CodeByMika/technikerarbeit2026-hardwarepruefadapter/Gehause/ISO-Ansicht.pdf

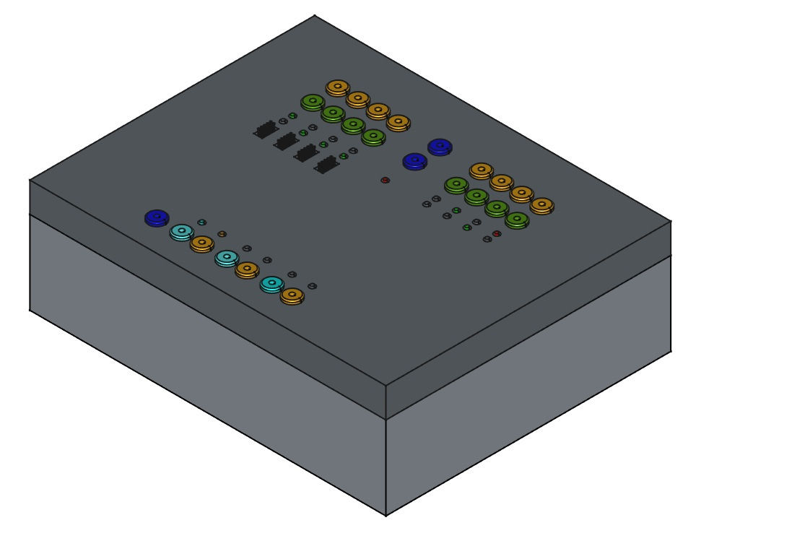
[picture p3: page 1]
