CodeByMika/technikerarbeit2026-hardwarepruefadapter/Hardware/Bauteildesigndaten/DMP3130L-7/DMP3130L-7.step

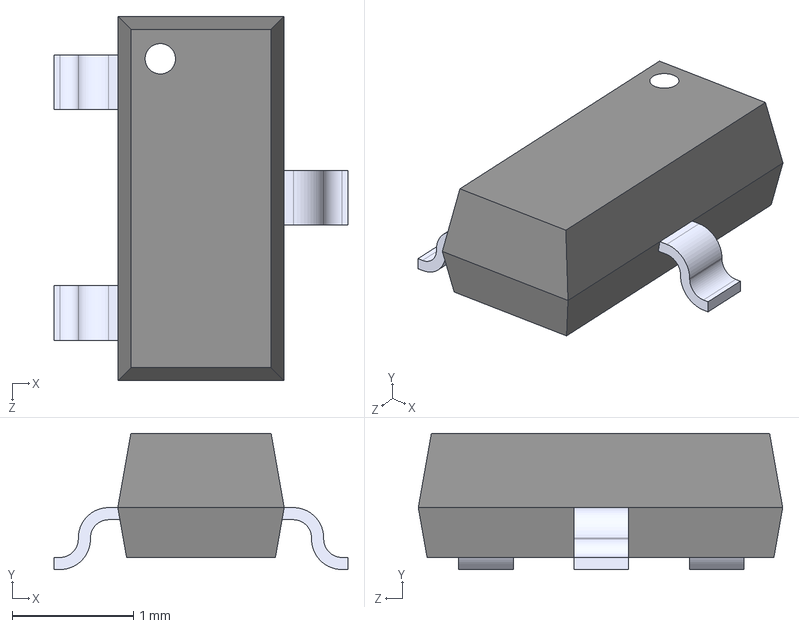
[picture p20: CAD file, 2026-06-18]
Hardware/Bauteildesigndaten/DMP3130L-7/DMP3130L-7.step
2.42 x 1.12 x 3.00 mm
