CodeByMika/technikerarbeit2026-hardwarepruefadapter/Hardware/Bauteildesigndaten/Importierte Bauteile/Buchsen/6120XX21621_61200821621/6120XX21621_61200821621.step

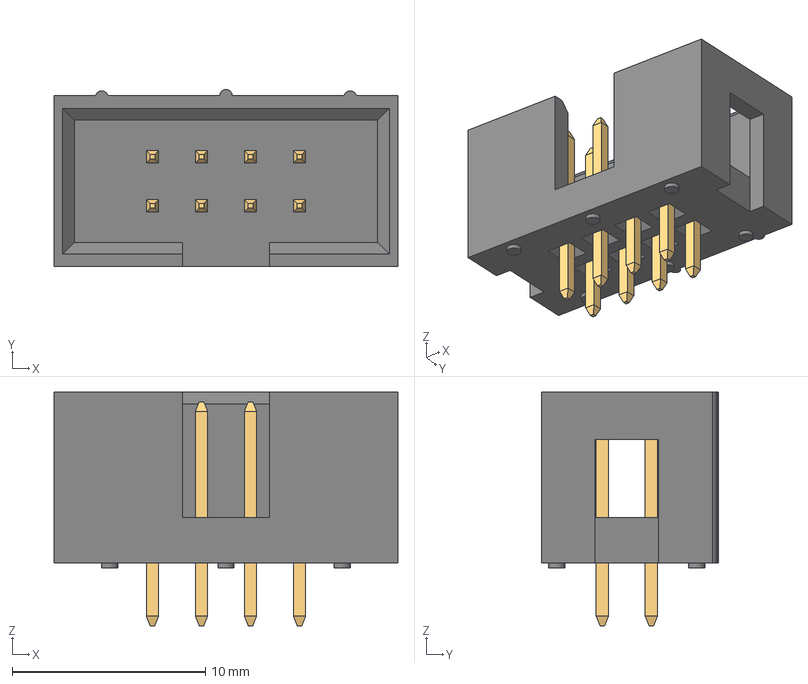
[picture p21: CAD file, 2026-06-18]
Hardware/Bauteildesigndaten/Importierte Bauteile/Buchsen/6120XX21621_61200821621/6120XX21621_61200821621.step
17.8 x 9.18 x 12.1 mm
6120xx21621_PIN x 8
