CodeByMika/technikerarbeit2026-hardwarepruefadapter/Hardware/Bauteildesigndaten/Importierte Bauteile/Buchsen/6120XX21621_61201021621/6120XX21621_61201021621.step

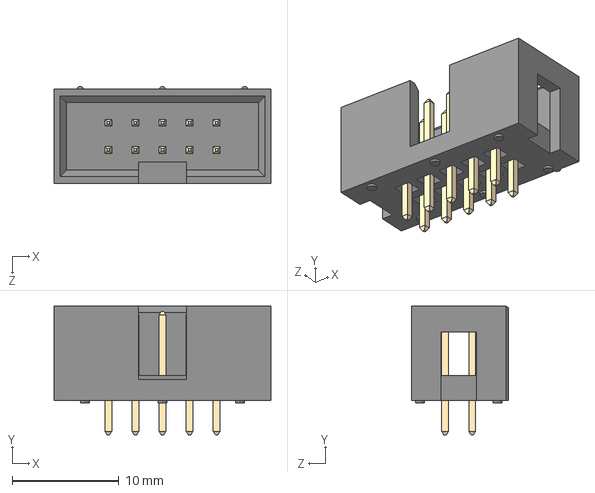
[picture p22: CAD file, 2026-06-18]
Hardware/Bauteildesigndaten/Importierte Bauteile/Buchsen/6120XX21621_61201021621/6120XX21621_61201021621.step
20.4 x 12.1 x 9.10 mm
