CodeByMika/technikerarbeit2026-hardwarepruefadapter/Hardware/Bauteildesigndaten/Importierte Bauteile/Buchsen/6130XX21121_61300621121/6130XX21121_61300621121.step

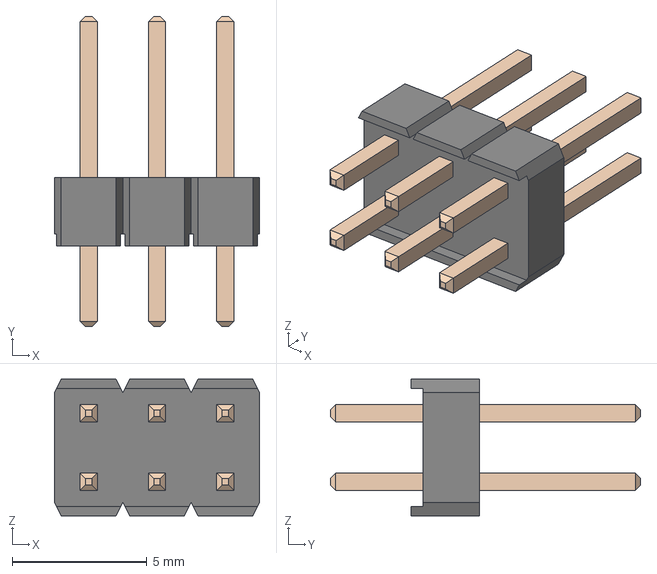
[picture p23: CAD file, 2026-06-18]
Hardware/Bauteildesigndaten/Importierte Bauteile/Buchsen/6130XX21121_61300621121/6130XX21121_61300621121.step
7.62 x 11.5 x 5.08 mm
6130xx21121_PIN x 6
