CodeByMika/technikerarbeit2026-hardwarepruefadapter/Hardware/Bauteildesigndaten/Importierte Bauteile/Buchsen/6130XX21121_61301221121/6130XX21121_61301221121.step

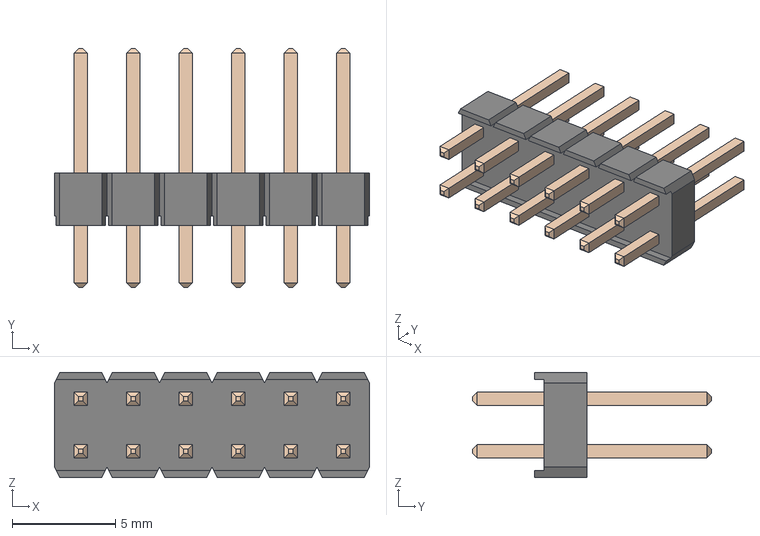
[picture p24: CAD file, 2026-06-18]
Hardware/Bauteildesigndaten/Importierte Bauteile/Buchsen/6130XX21121_61301221121/6130XX21121_61301221121.step
15.2 x 11.5 x 5.08 mm
6130xx21121_PIN x 12
