CodeByMika/technikerarbeit2026-hardwarepruefadapter/Hardware/Bauteildesigndaten/Importierte Bauteile/Buchsen/G800LQ592005HR/G800LQ592005HR.step

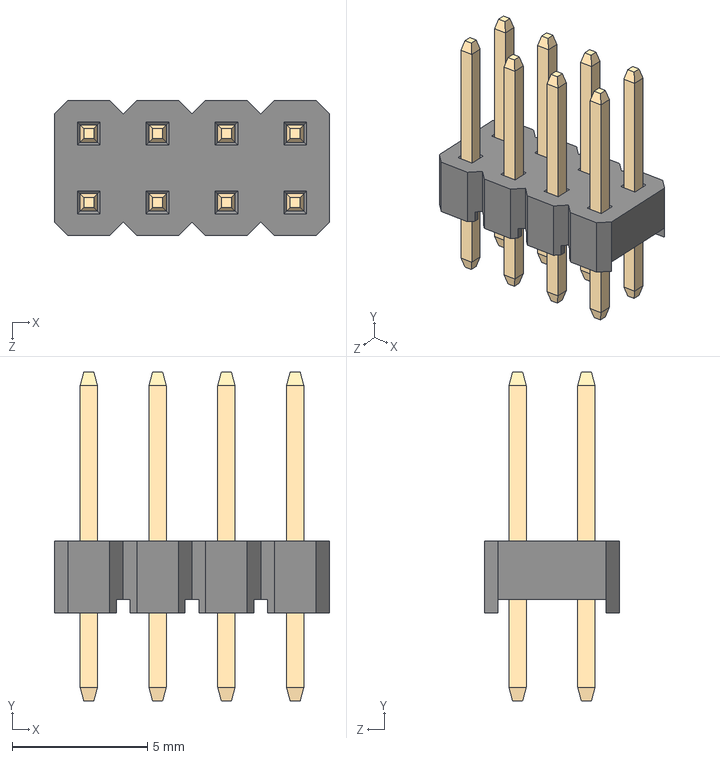
[picture p25: CAD file, 2026-06-18]
Hardware/Bauteildesigndaten/Importierte Bauteile/Buchsen/G800LQ592005HR/G800LQ592005HR.step
10.2 x 12.2 x 5.00 mm
