CodeByMika/technikerarbeit2026-hardwarepruefadapter/Hardware/Bauteildesigndaten/INA168QDBVRQ1/INA168QDBVRQ1.step

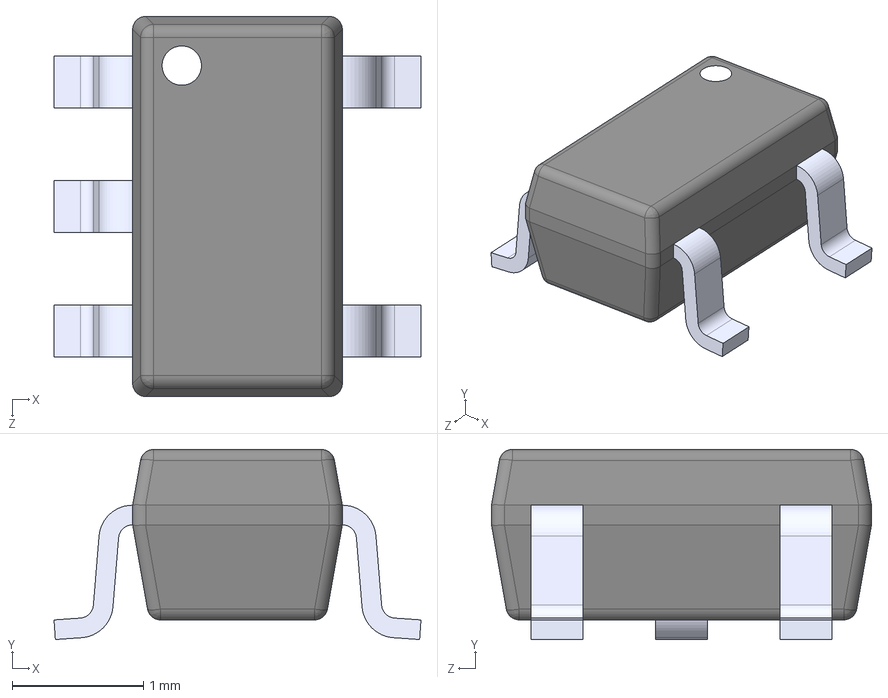
[picture p26: CAD file, 2026-06-18]
Hardware/Bauteildesigndaten/INA168QDBVRQ1/INA168QDBVRQ1.step
2.80 x 1.45 x 2.90 mm
