CodeByMika/technikerarbeit2026-hardwarepruefadapter/Hardware/Bauteildesigndaten/IRF9358PBF/IRF9358PBF.step

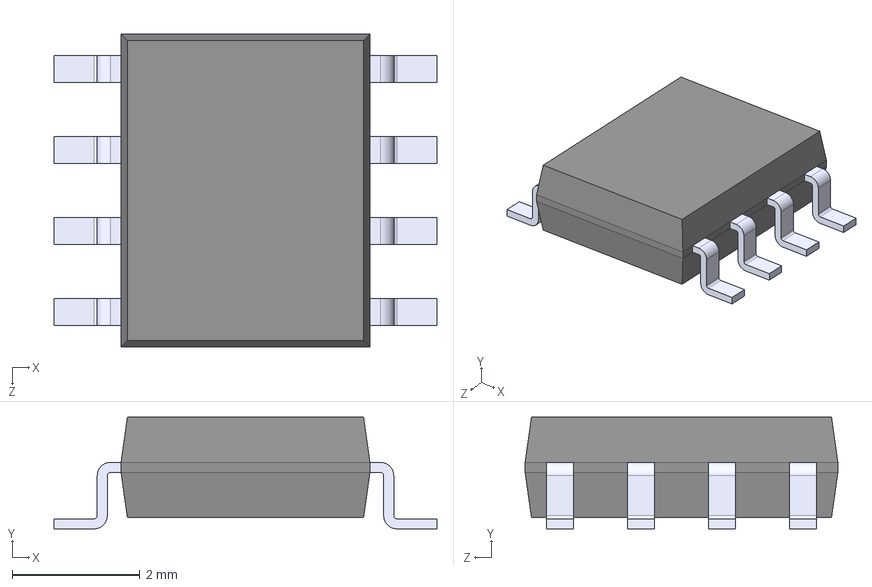
[picture p27: CAD file, 2026-06-18]
Hardware/Bauteildesigndaten/IRF9358PBF/IRF9358PBF.step
6.00 x 1.75 x 4.90 mm
