CodeByMika/technikerarbeit2026-hardwarepruefadapter/Hardware/Bauteildesigndaten/LP5018RSMR/LP5018RSMR.step

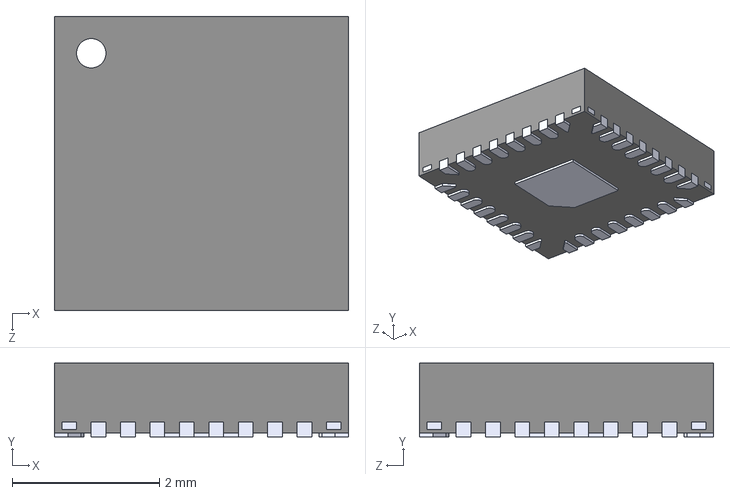
[picture p28: CAD file, 2026-06-18]
Hardware/Bauteildesigndaten/LP5018RSMR/LP5018RSMR.step
4.00 x 1.00 x 4.00 mm
