CodeByMika/technikerarbeit2026-hardwarepruefadapter/Hardware/Bauteildesigndaten/LSF0102DCTR/LSF0102DCTR.step

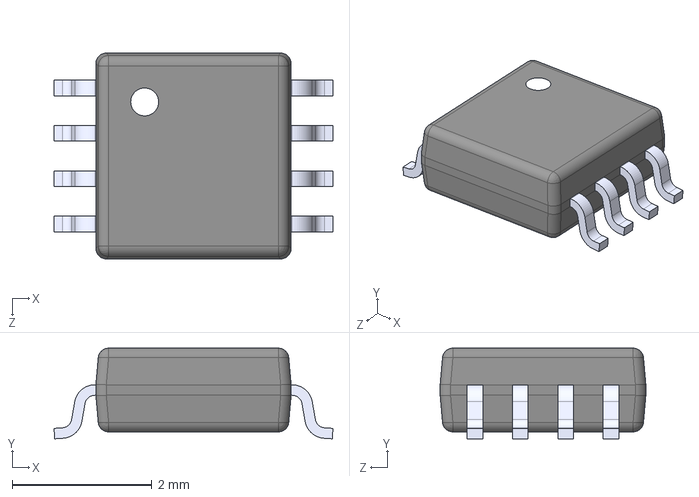
[picture p29: CAD file, 2026-06-18]
Hardware/Bauteildesigndaten/LSF0102DCTR/LSF0102DCTR.step
4.00 x 1.30 x 2.95 mm
