CodeByMika/technikerarbeit2026-hardwarepruefadapter/Hardware/Bauteildesigndaten/MF-MSMF010-2/MF-MSMF010-2.step

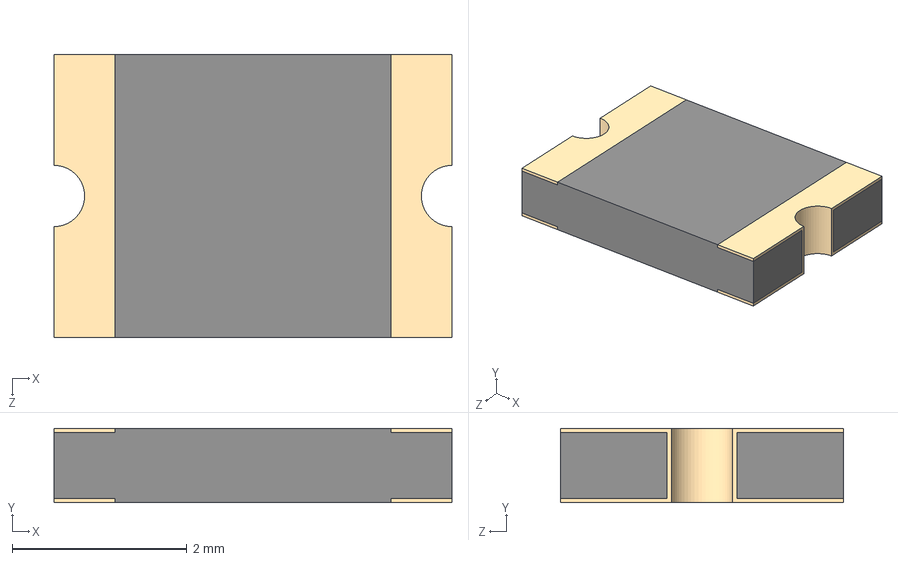
[picture p30: CAD file, 2026-06-18]
Hardware/Bauteildesigndaten/MF-MSMF010-2/MF-MSMF010-2.step
4.55 x 0.85 x 3.24 mm
