CodeByMika/technikerarbeit2026-hardwarepruefadapter/Hardware/Bauteildesigndaten/OPA2990IDR/OPA2990IDR.step

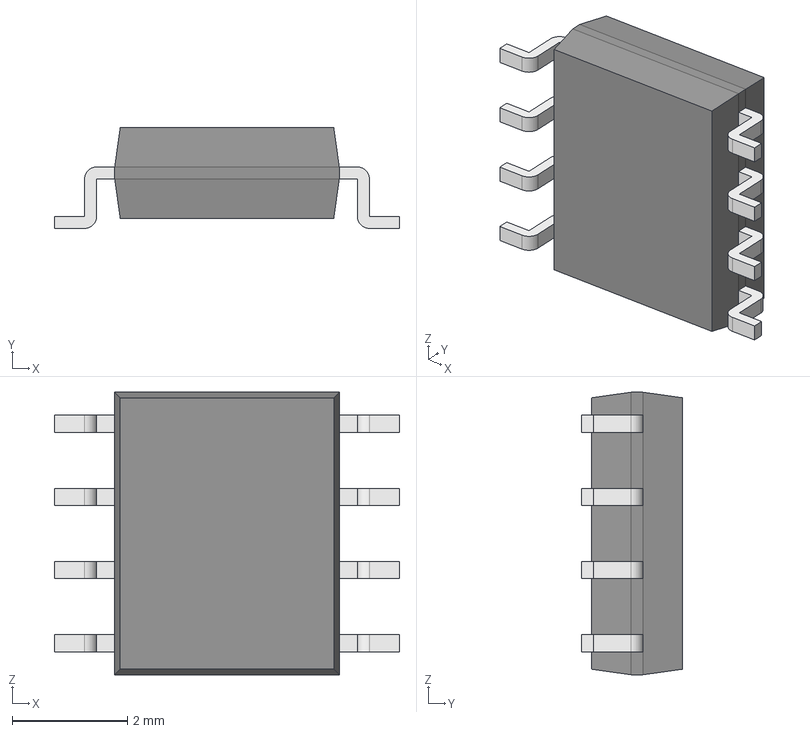
[picture p31: CAD file, 2026-06-18]
Hardware/Bauteildesigndaten/OPA2990IDR/OPA2990IDR.step
5.99 x 1.75 x 4.91 mm
Body001 (Mirror #1) x 4
XY-plane x 12
X-axis x 12
