CodeByMika/technikerarbeit2026-hardwarepruefadapter/Hardware/Bauteildesigndaten/SN65HVD3082ED/SN65HVD3082ED.step

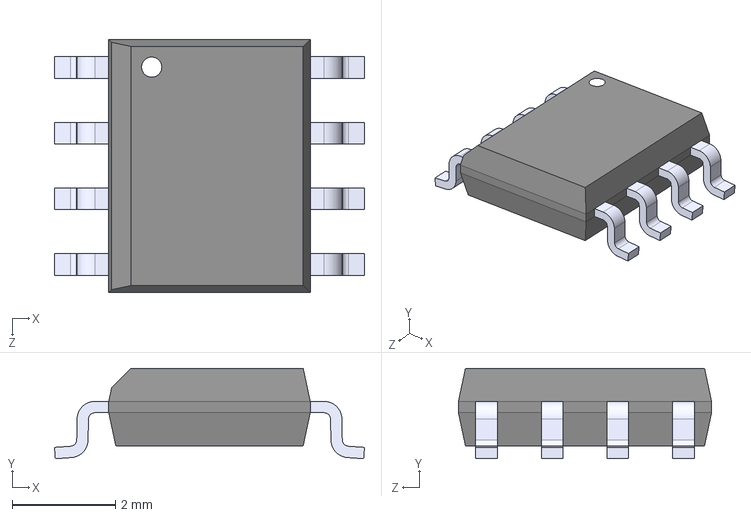
[picture p32: CAD file, 2026-06-18]
Hardware/Bauteildesigndaten/SN65HVD3082ED/SN65HVD3082ED.step
6.00 x 1.75 x 4.90 mm
