CodeByMika/technikerarbeit2026-hardwarepruefadapter/Hardware/Bauteildesigndaten/Spannungsversorgung/LM1117MPX-3.3_NOPB/LM1117MPX-3.3_NOPB.step

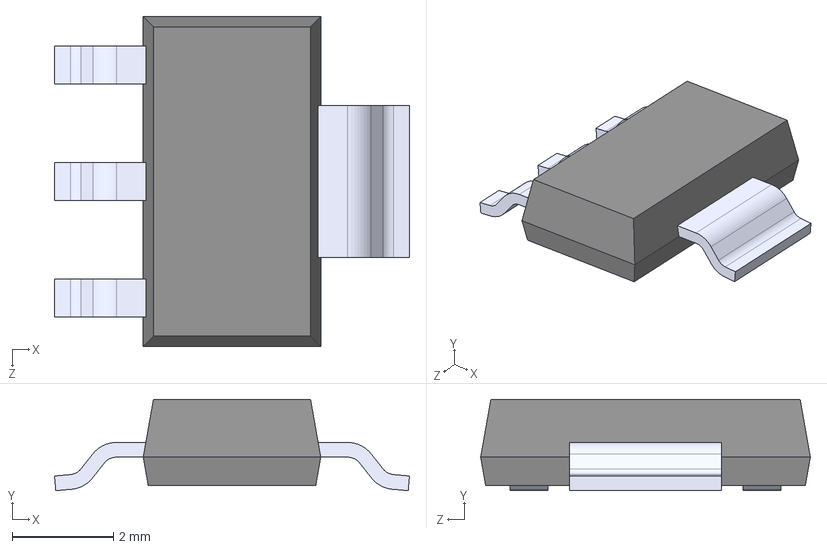
[picture p33: CAD file, 2026-06-18]
Hardware/Bauteildesigndaten/Spannungsversorgung/LM1117MPX-3.3_NOPB/LM1117MPX-3.3_NOPB.step
7.00 x 1.80 x 6.50 mm
