CodeByMika/technikerarbeit2026-hardwarepruefadapter/Hardware/Bauteildesigndaten/Stiftleisten u Buchsen/6120XX21621_61201621621/6120XX21621_61201621621.step

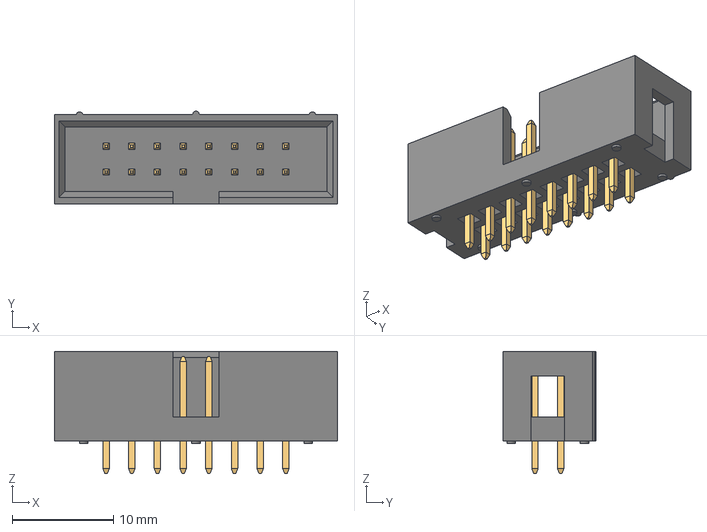
[picture p35: CAD file, 2026-06-18]
Hardware/Bauteildesigndaten/Stiftleisten u Buchsen/6120XX21621_61201621621/6120XX21621_61201621621.step
28.0 x 9.18 x 12.1 mm
6120xx21621_PIN x 16
