CodeByMika/technikerarbeit2026-hardwarepruefadapter/Hardware/Bauteildesigndaten/Stiftleisten u Buchsen/6130XX21121_61301421121/6130XX21121_61301421121.step

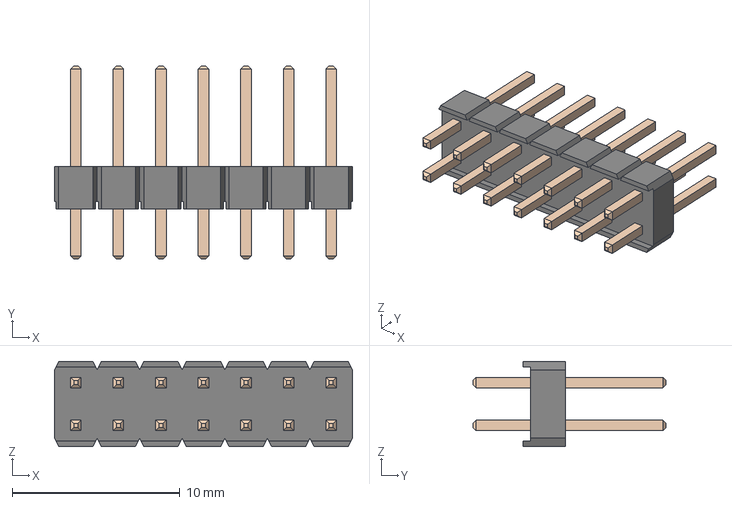
[picture p36: CAD file, 2026-06-18]
Hardware/Bauteildesigndaten/Stiftleisten u Buchsen/6130XX21121_61301421121/6130XX21121_61301421121.step
17.8 x 11.5 x 5.08 mm
6130xx21121_PIN x 14
