CodeByMika/technikerarbeit2026-hardwarepruefadapter/Hardware/Bauteildesigndaten/WE-LQS_3015/WE-LQS_3015.step

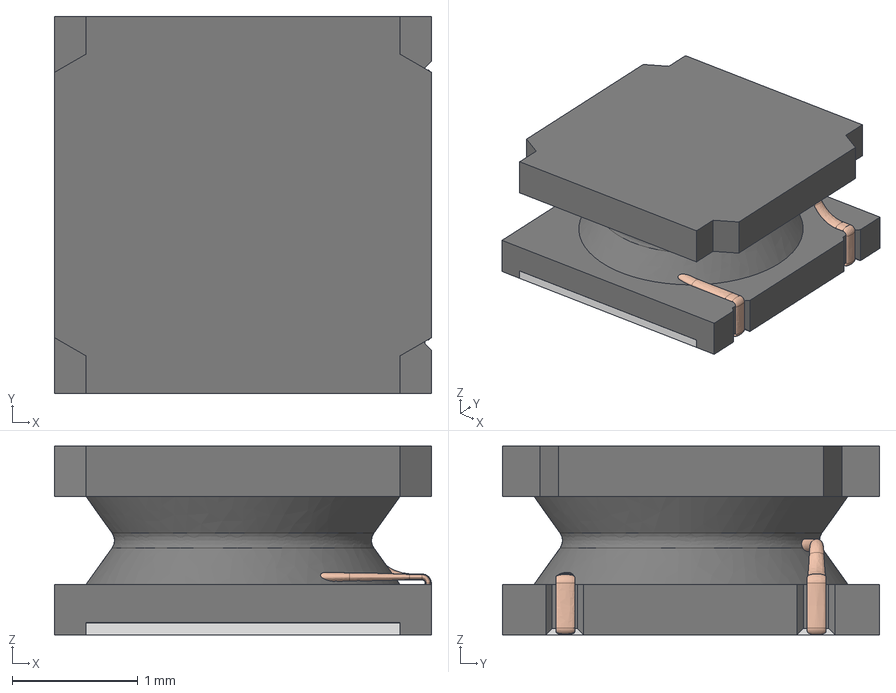
[picture p37: CAD file, 2026-06-18]
Hardware/Bauteildesigndaten/WE-LQS_3015/WE-LQS_3015.step
3.00 x 3.00 x 1.50 mm
