CodeByMika/technikerarbeit2026-hardwarepruefadapter/Hardware/Bauteildesigndaten/WE-MAPI_4020/Download_STP_WE-MAPI_4020+%28rev1%29.stp

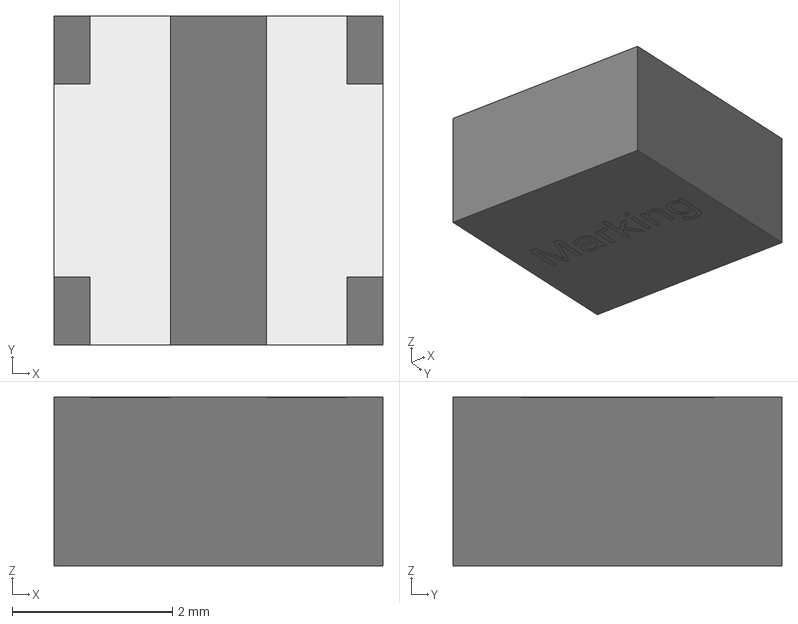
[picture p38: CAD file, 2026-06-18]
Hardware/Bauteildesigndaten/WE-MAPI_4020/Download_STP_WE-MAPI_4020+%28rev1%29.stp
4.10 x 4.10 x 2.10 mm
body_SSMC_4020
land_pattern_SSMC_4020 x 2
