CodeByMika/technikerarbeit2026-hardwarepruefadapter/Hardware/Bauteildesigndaten/WE-MPSB_1812/WE-MPSB_1812.step

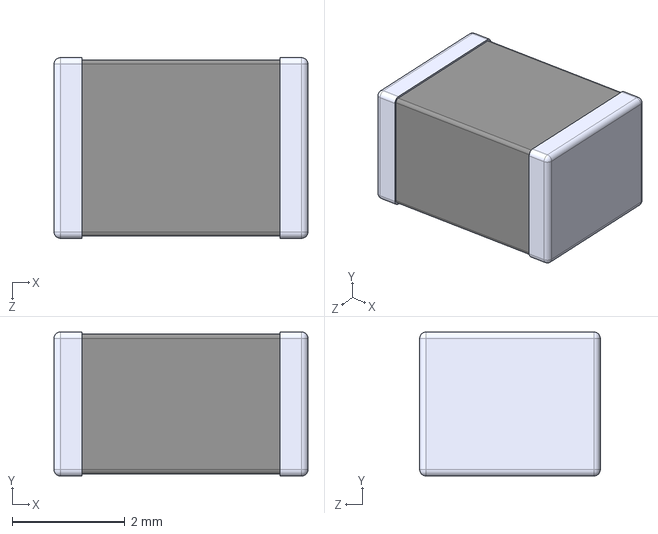
[picture p39: CAD file, 2026-06-18]
Hardware/Bauteildesigndaten/WE-MPSB_1812/WE-MPSB_1812.step
4.50 x 2.55 x 3.20 mm
