CodeByMika/technikerarbeit2026-hardwarepruefadapter/Hardware/Bauteildesigndaten/WL-SMSW_1204_A/WL-SMSW_1204_A.step

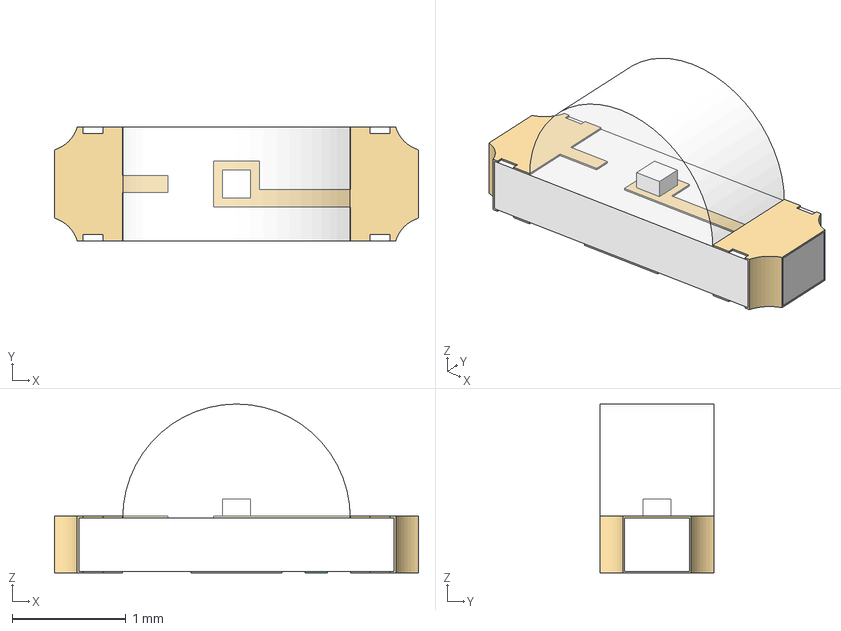
[picture p40: CAD file, 2026-06-18]
Hardware/Bauteildesigndaten/WL-SMSW_1204_A/WL-SMSW_1204_A.step
3.20 x 1.00 x 1.48 mm
glass housing
PCB
contact-pins
