CodeByMika/technikerarbeit2026-hardwarepruefadapter/Hardware/Bauteildesigndaten/XAL7030-332MEB/XAL7030-332MEB.step

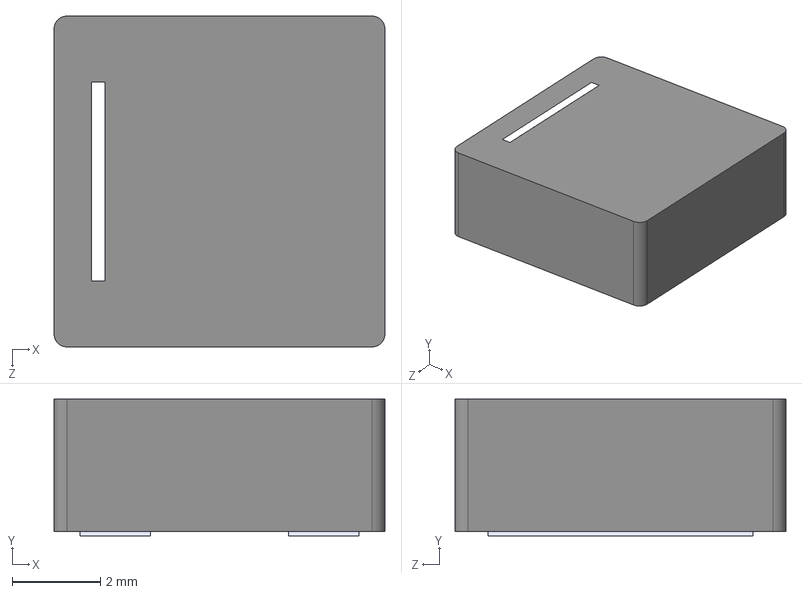
[picture p41: CAD file, 2026-06-18]
Hardware/Bauteildesigndaten/XAL7030-332MEB/XAL7030-332MEB.step
7.50 x 3.10 x 7.50 mm
