CodeByMika/technikerarbeit2026-hardwarepruefadapter/Dokumentation/Technikerarbeit2026-Pflichtenheft.pdf

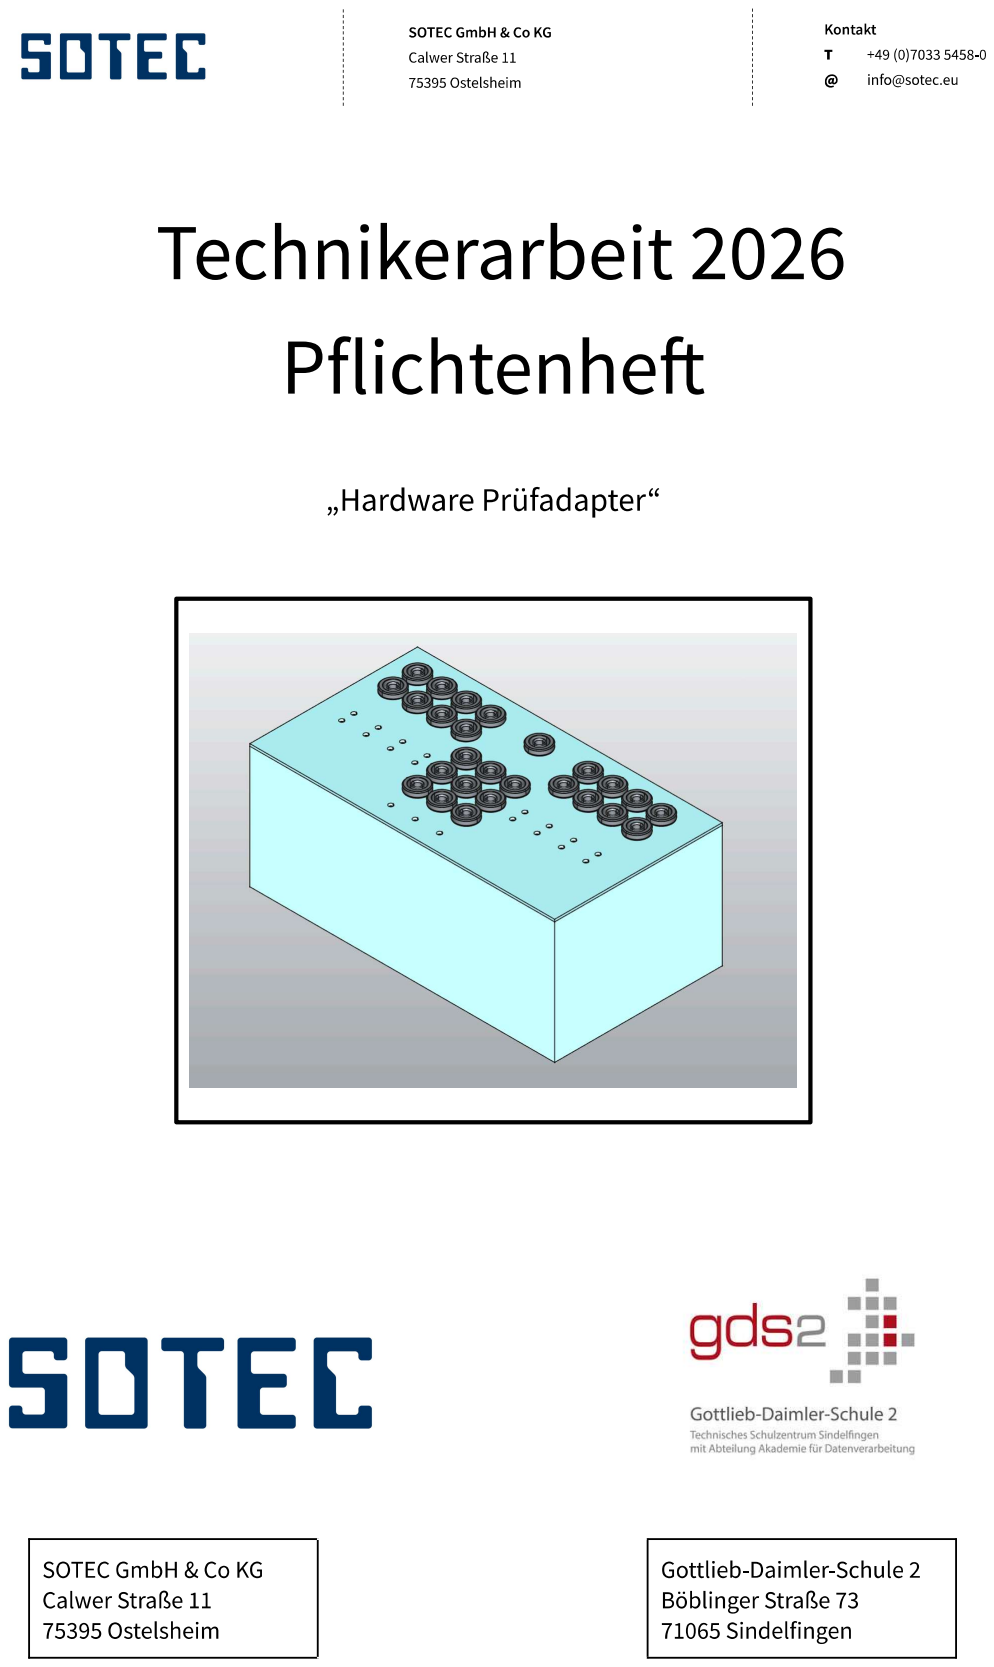
[picture p44: page 1]

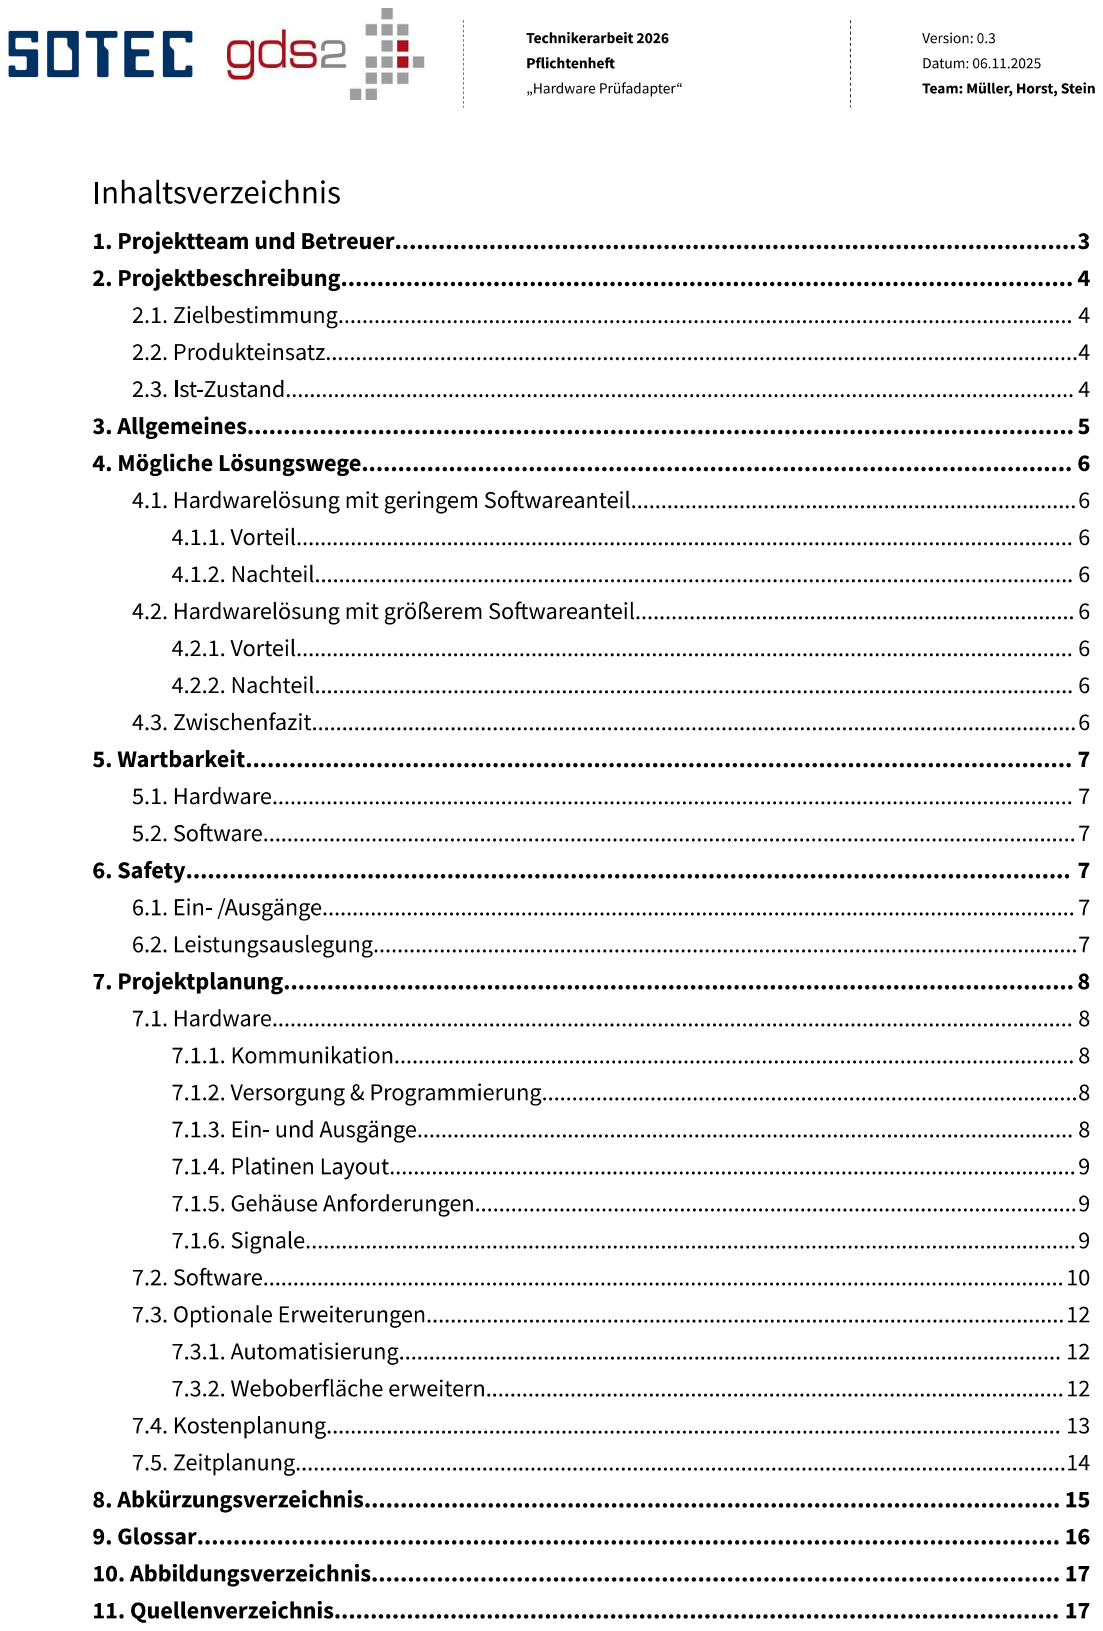
[picture p45: page 2]

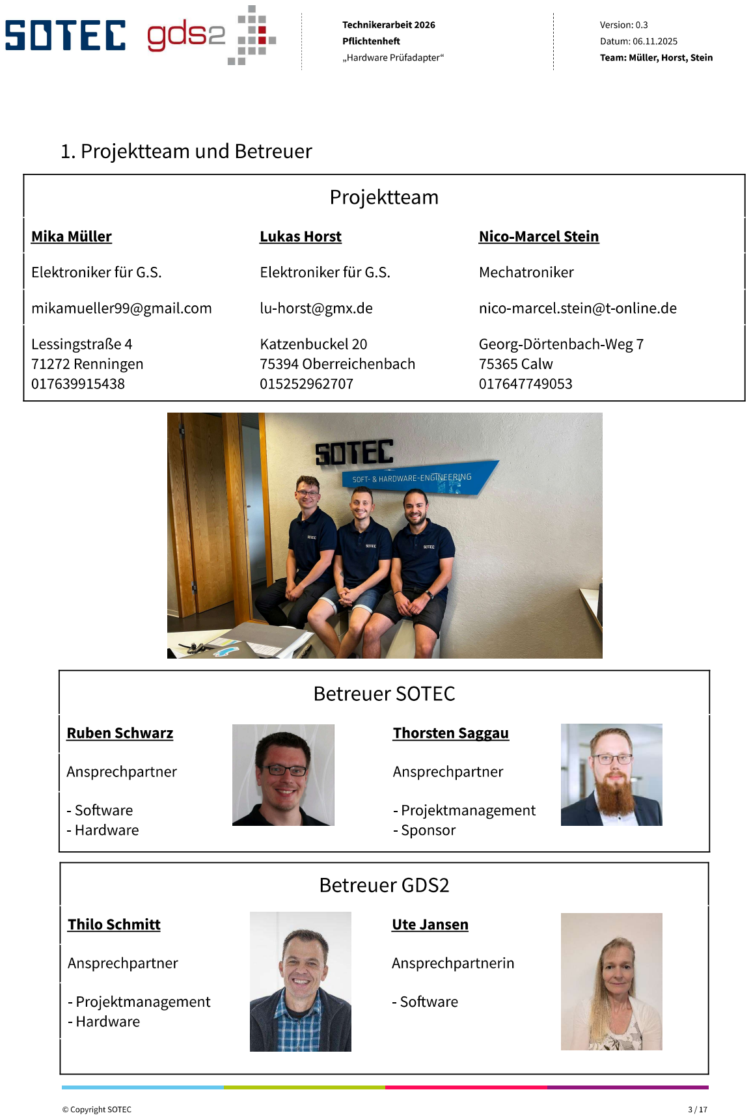
[picture p46: page 3]

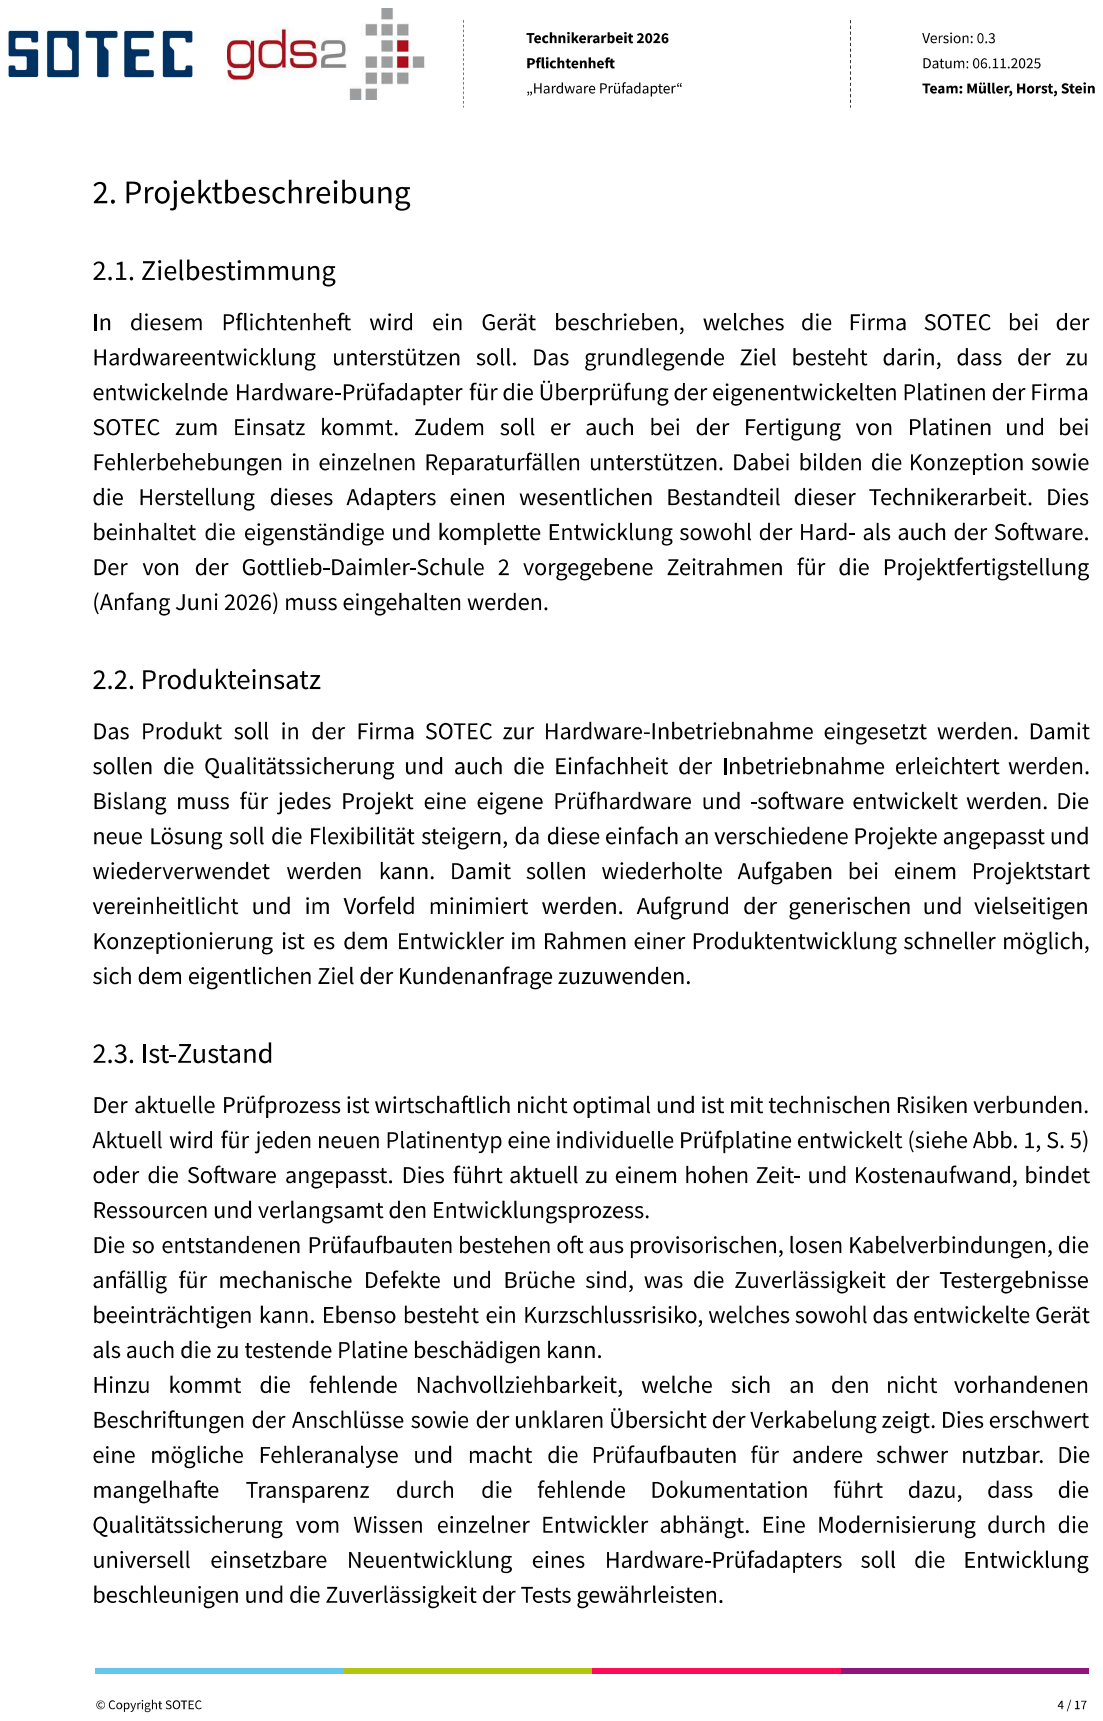
[picture p47: page 4]

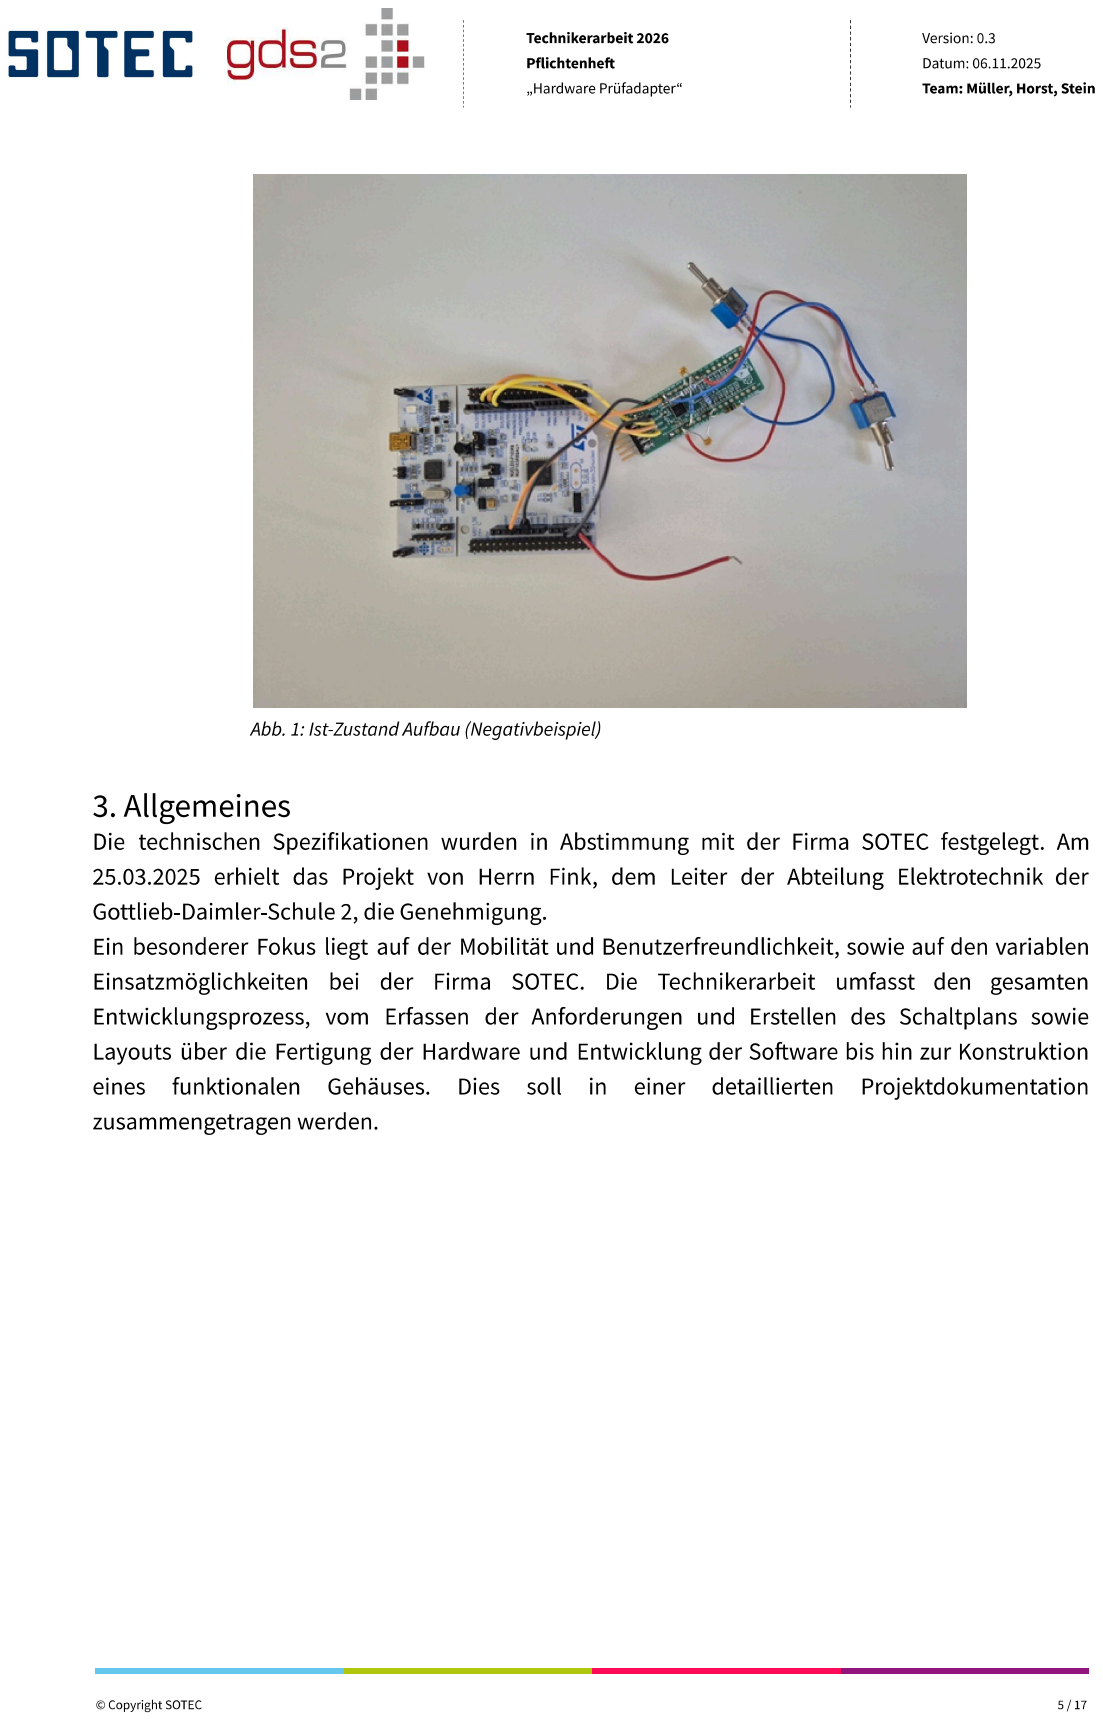
[picture p48: page 5]

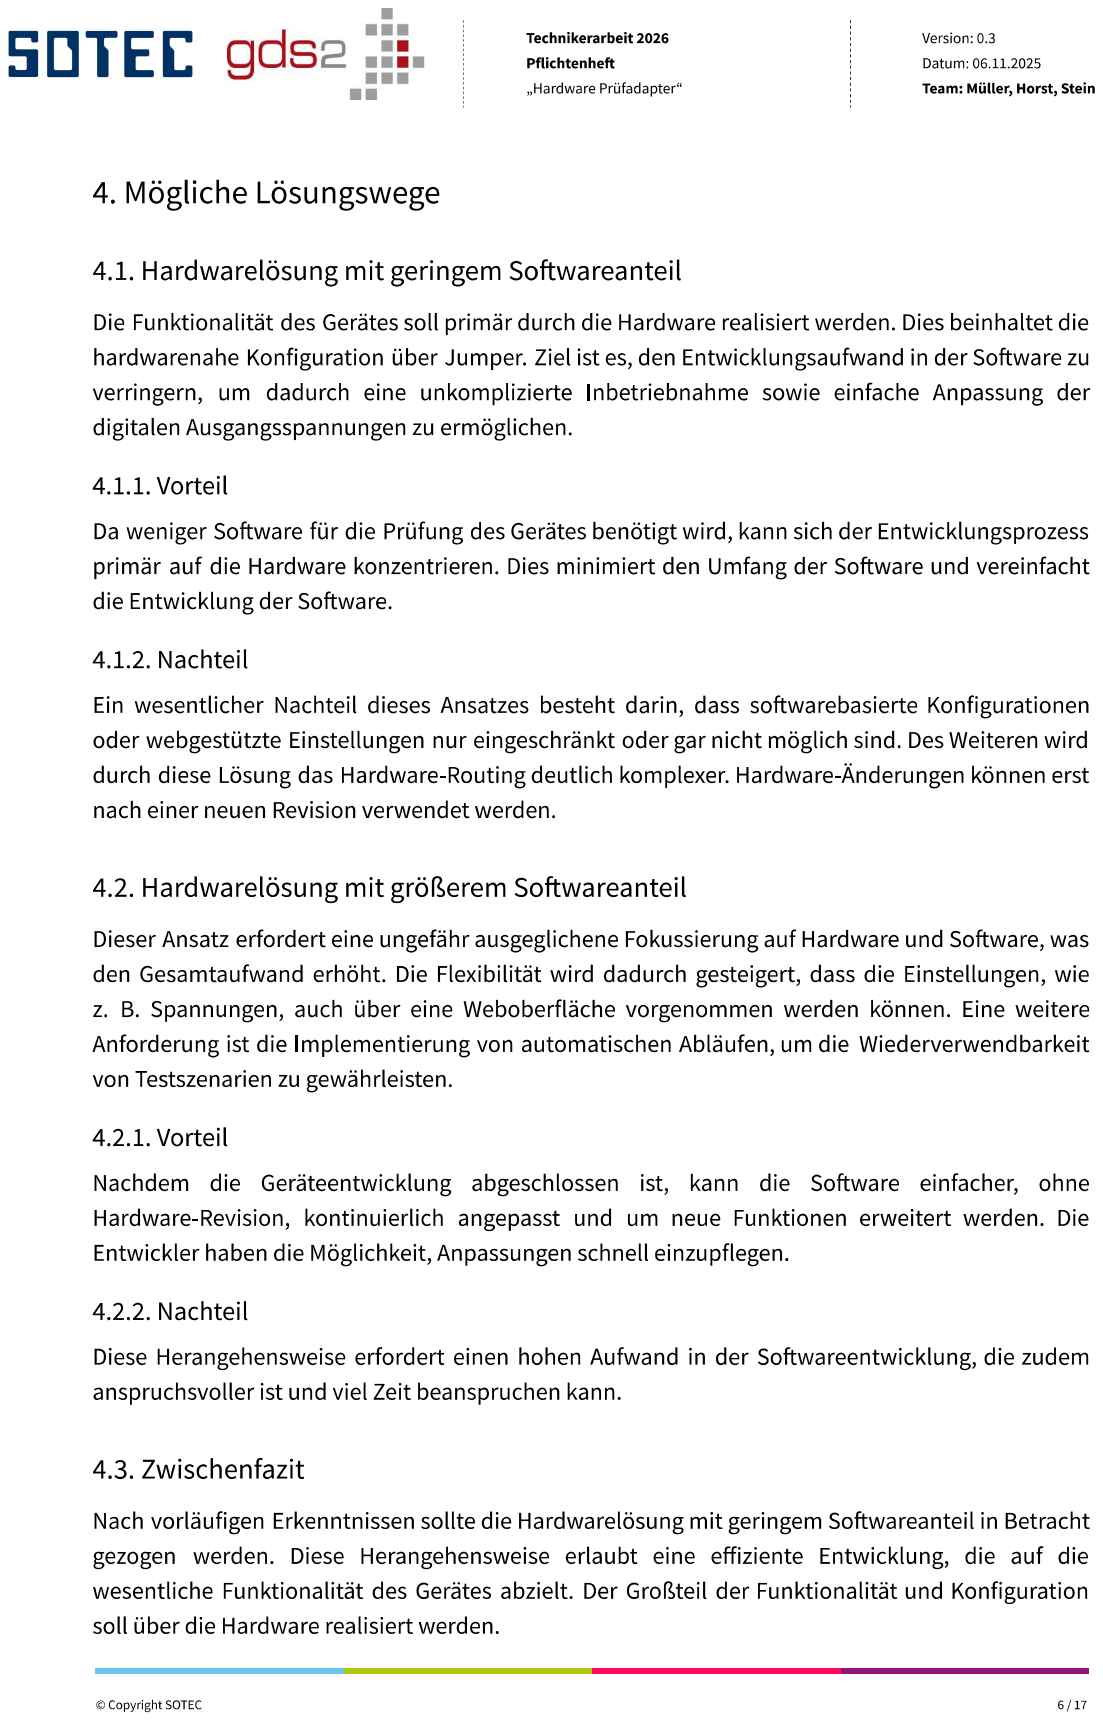
[picture p49: page 6]

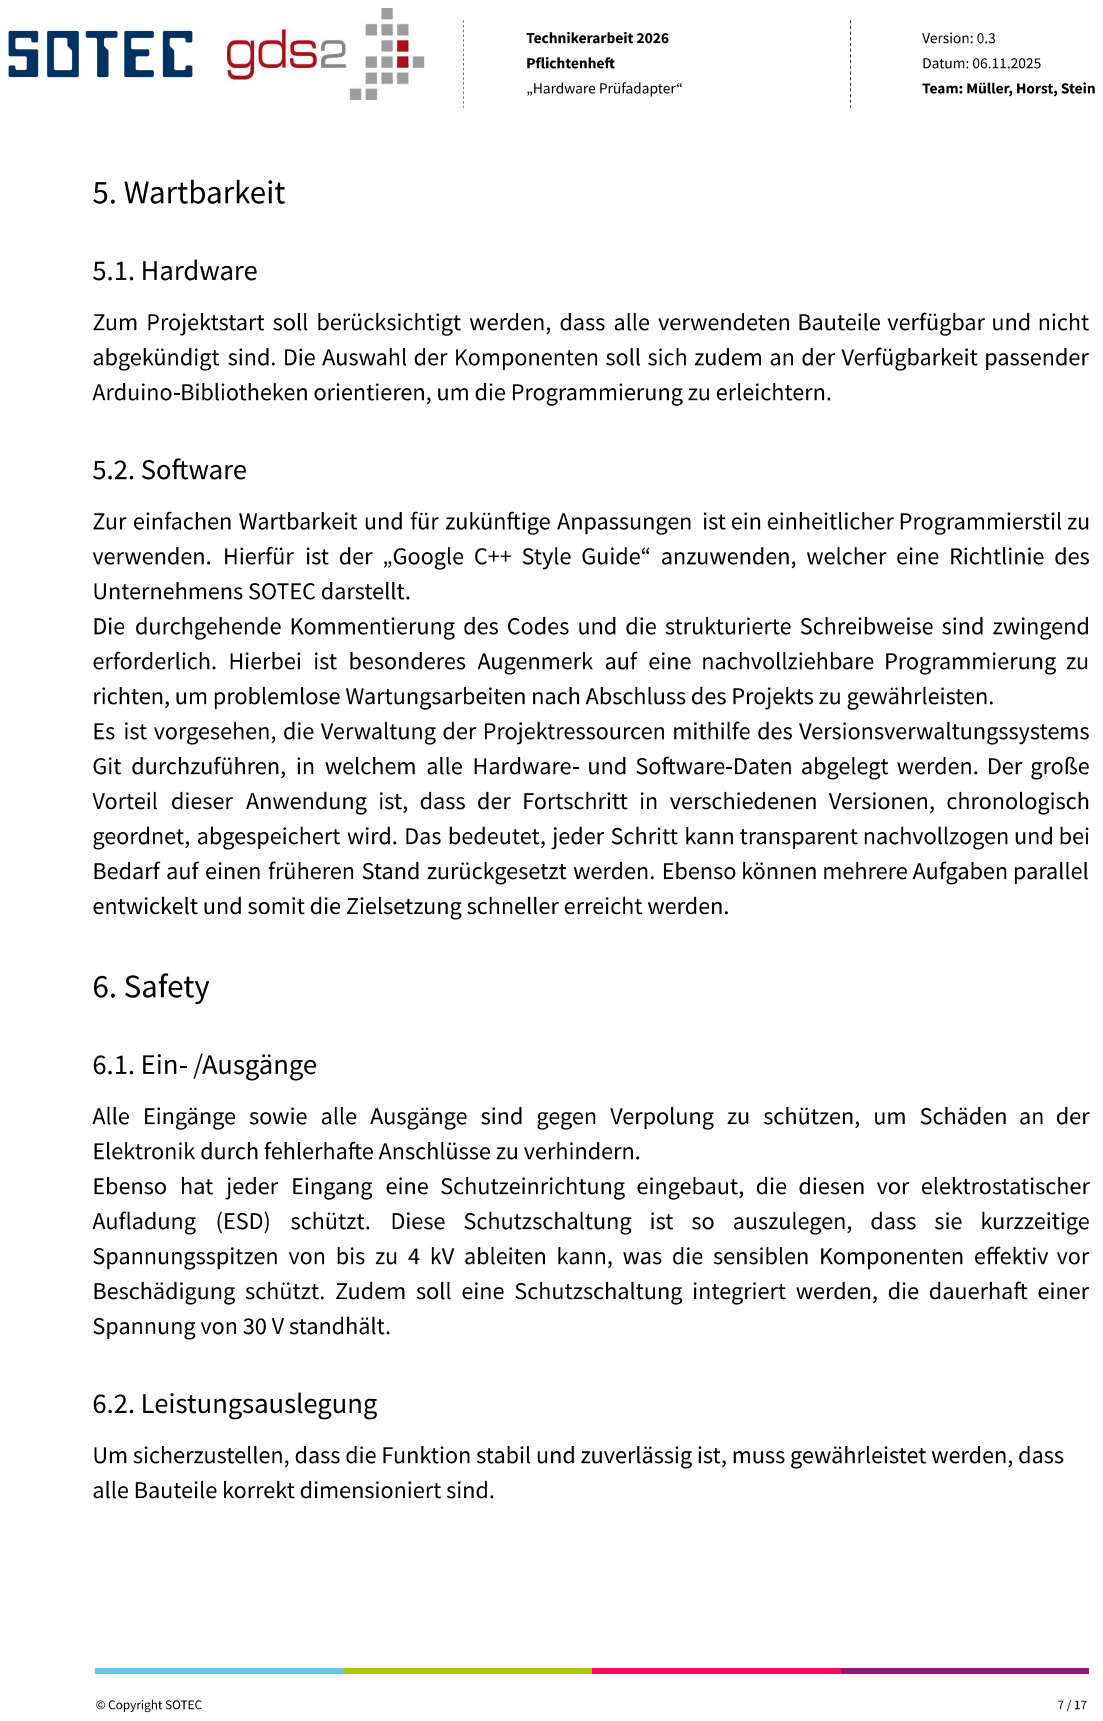
[picture p50: page 7]

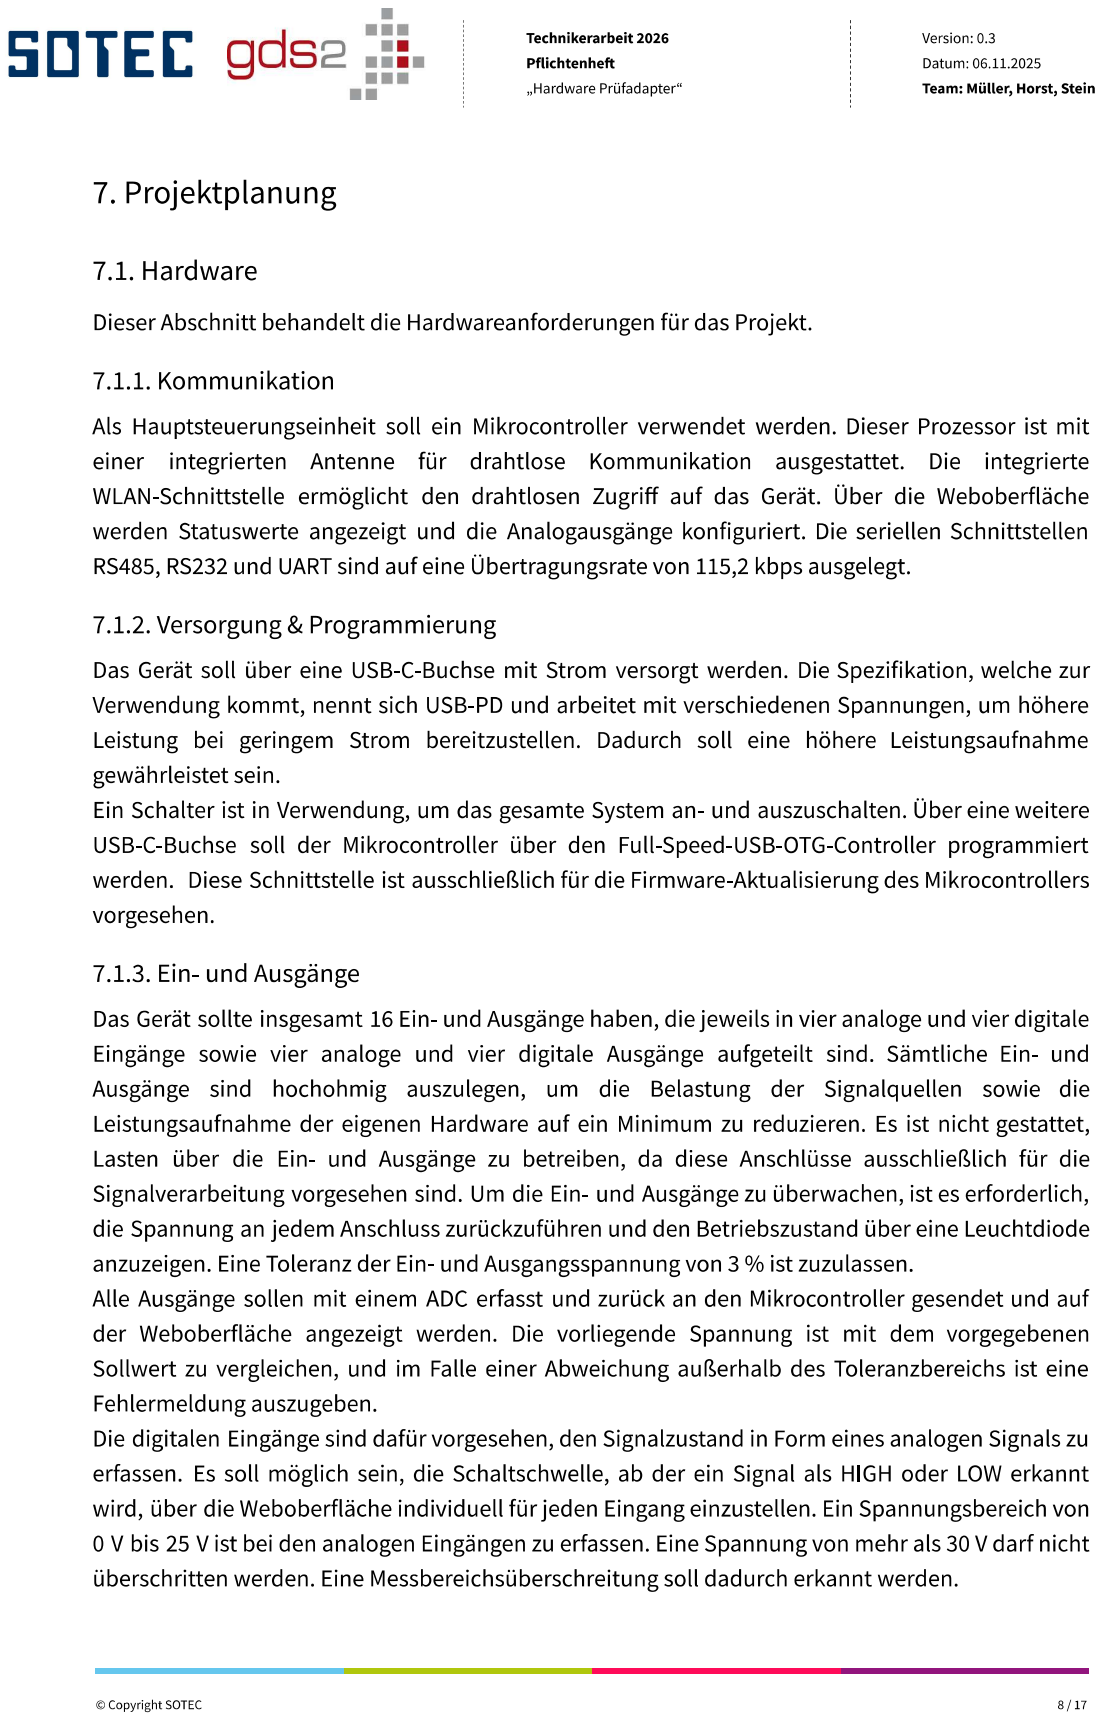
[picture p51: page 8]

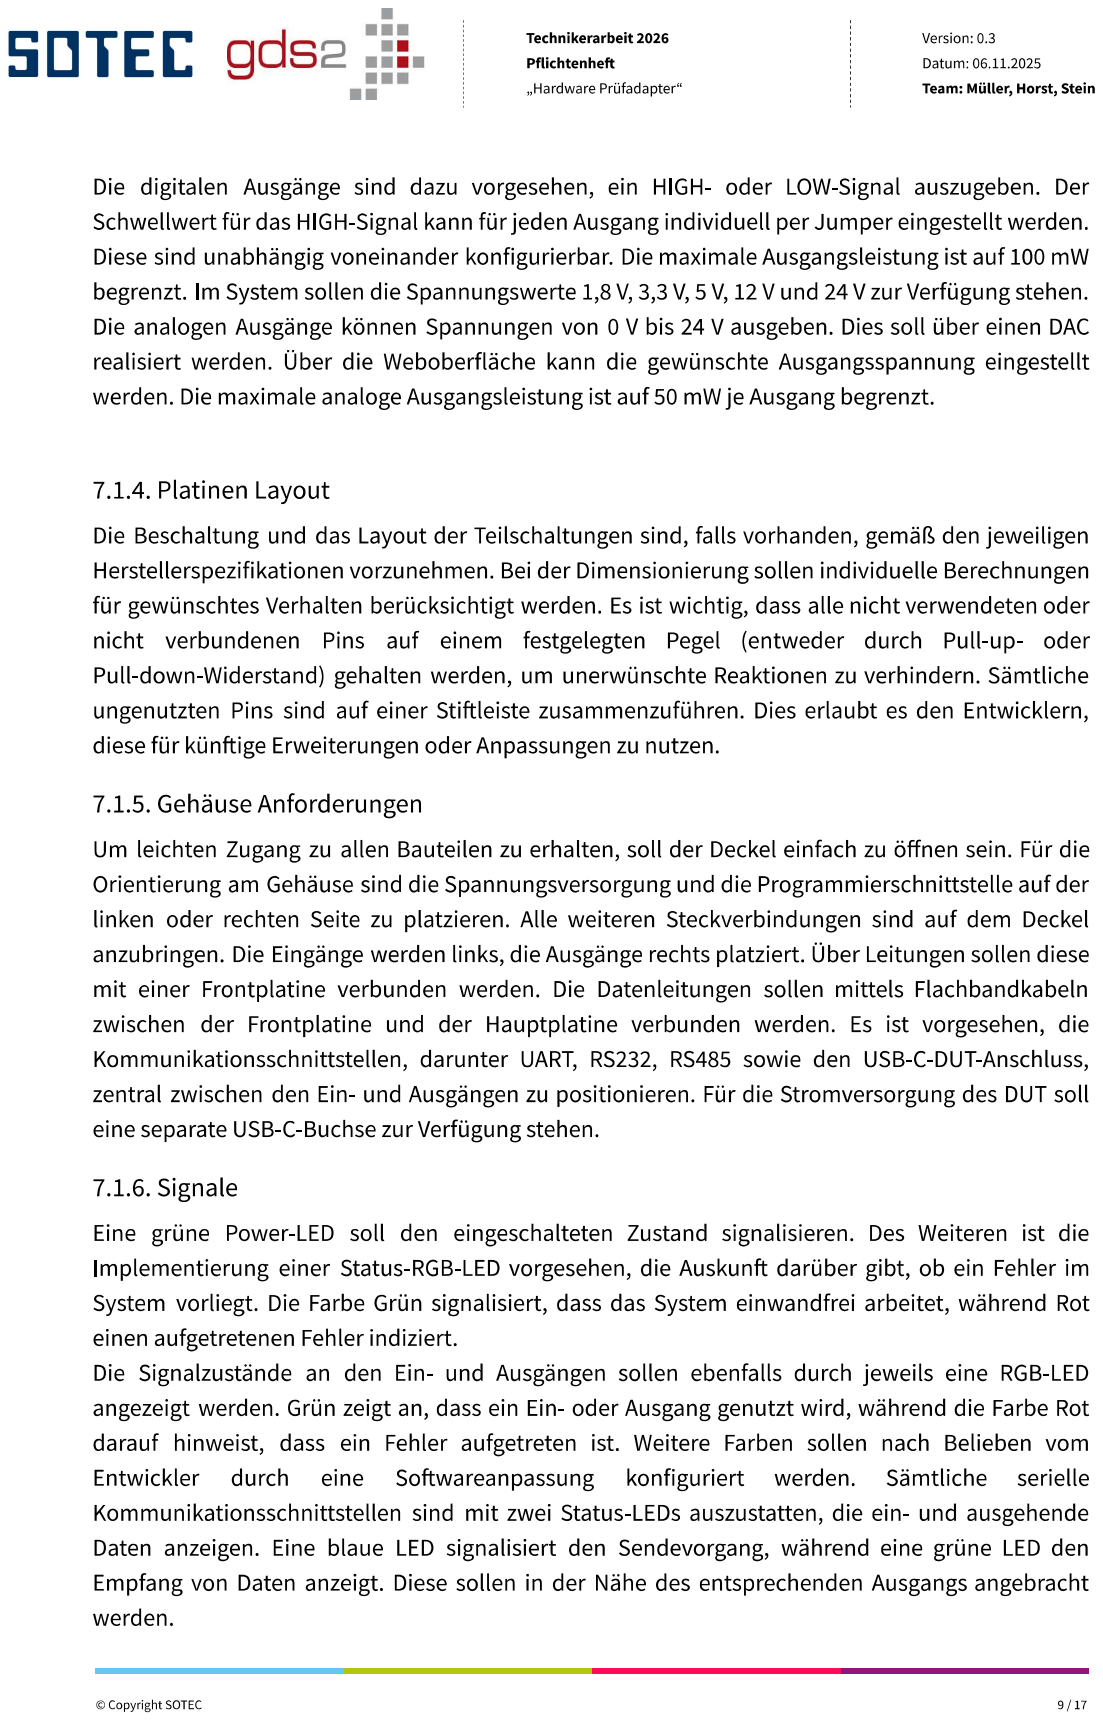
[picture p52: page 9]

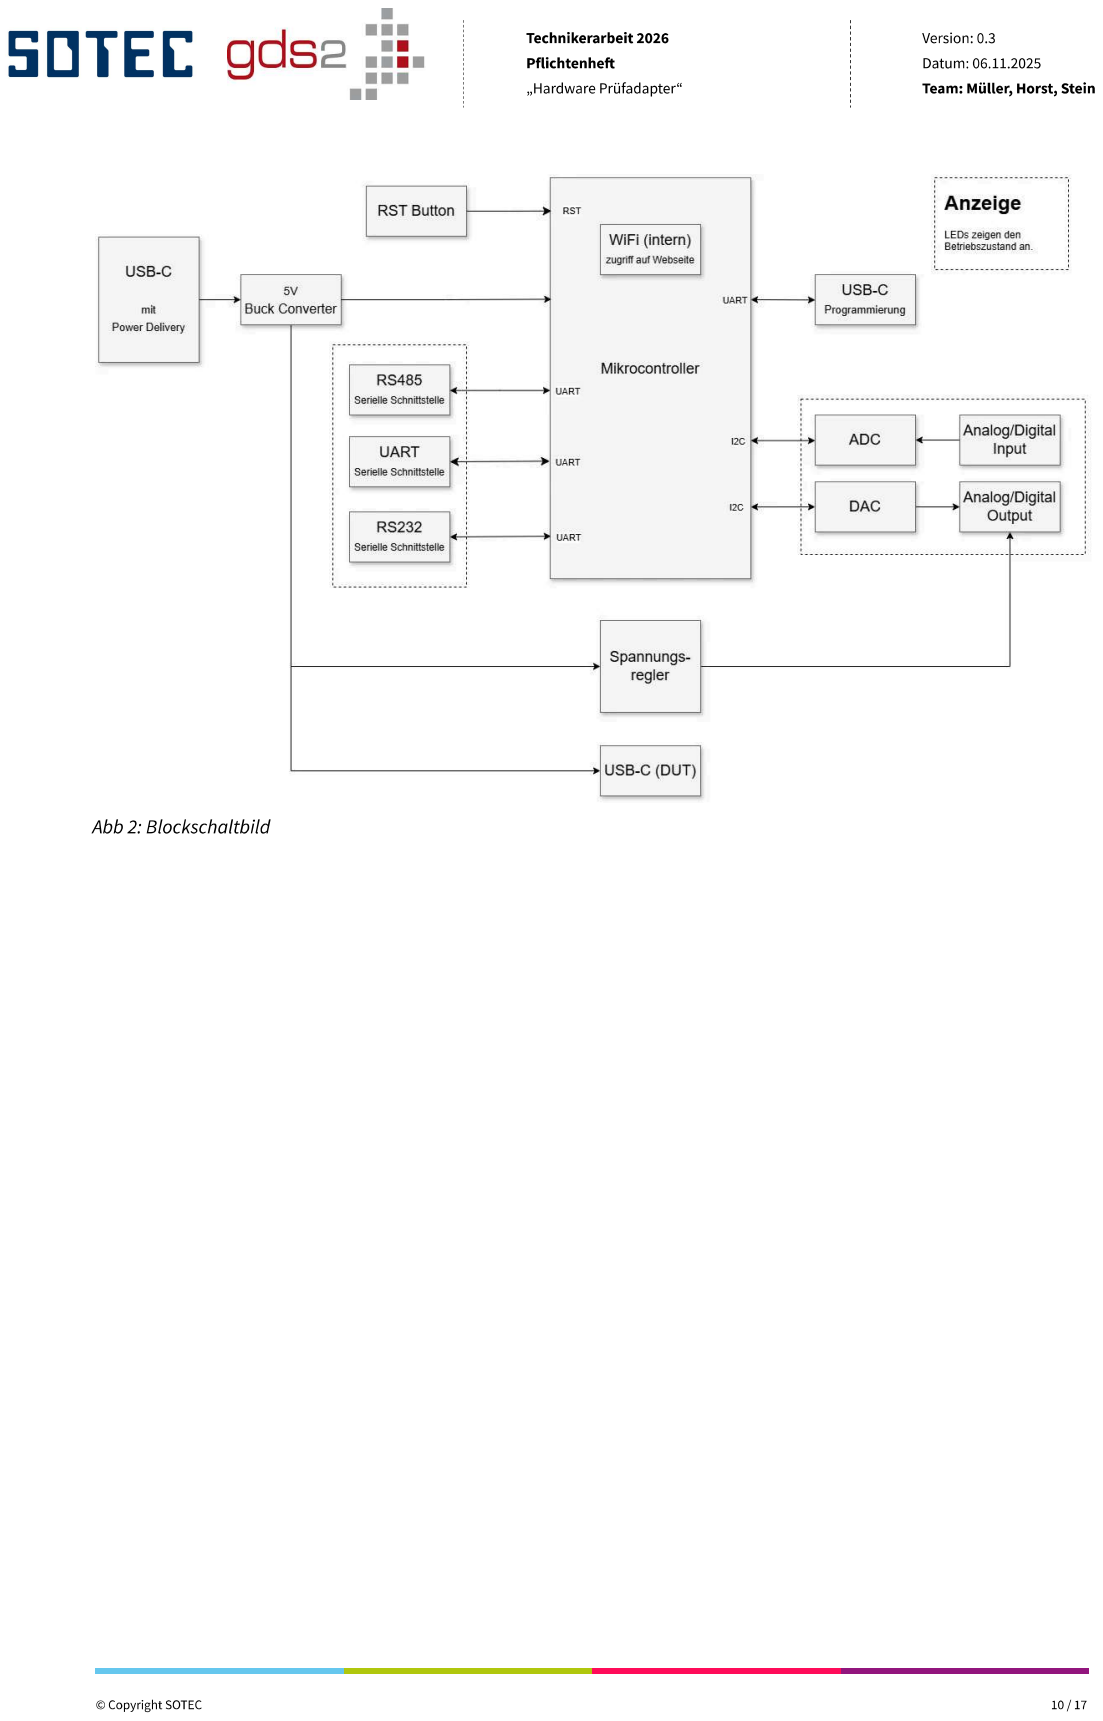
[picture p53: page 10]

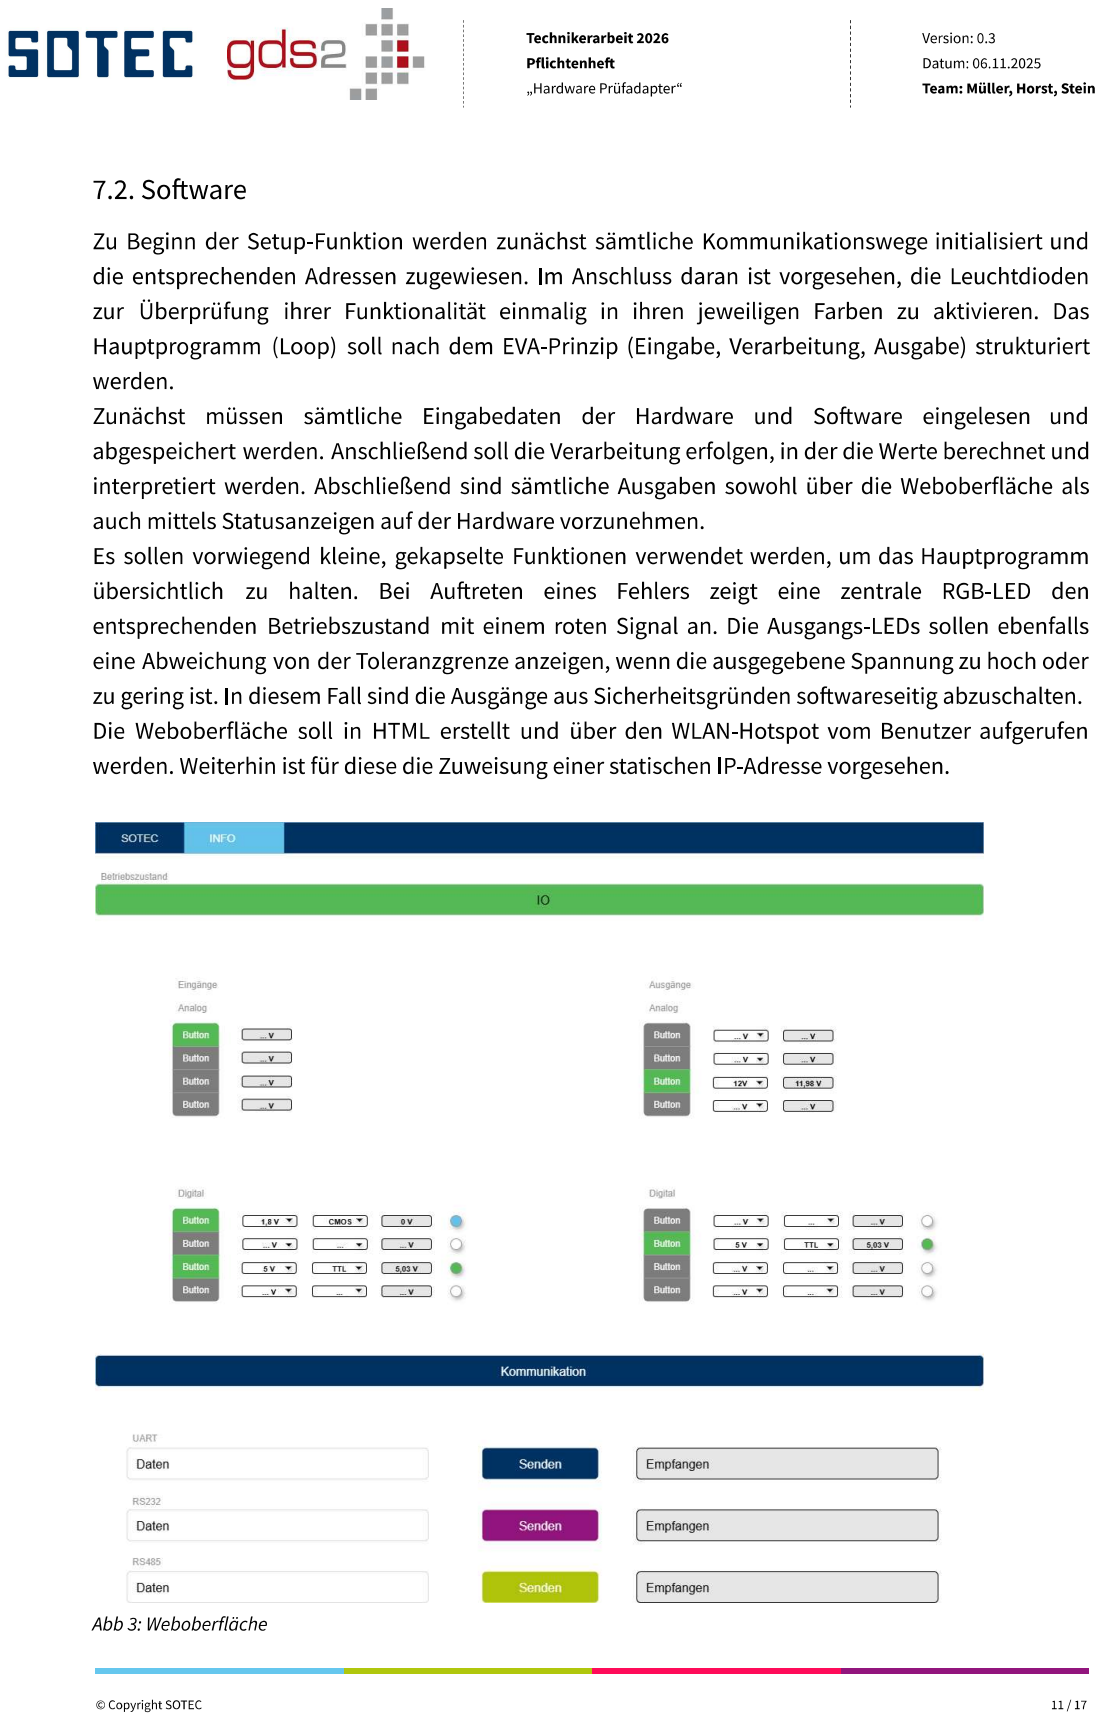
[picture p54: page 11]

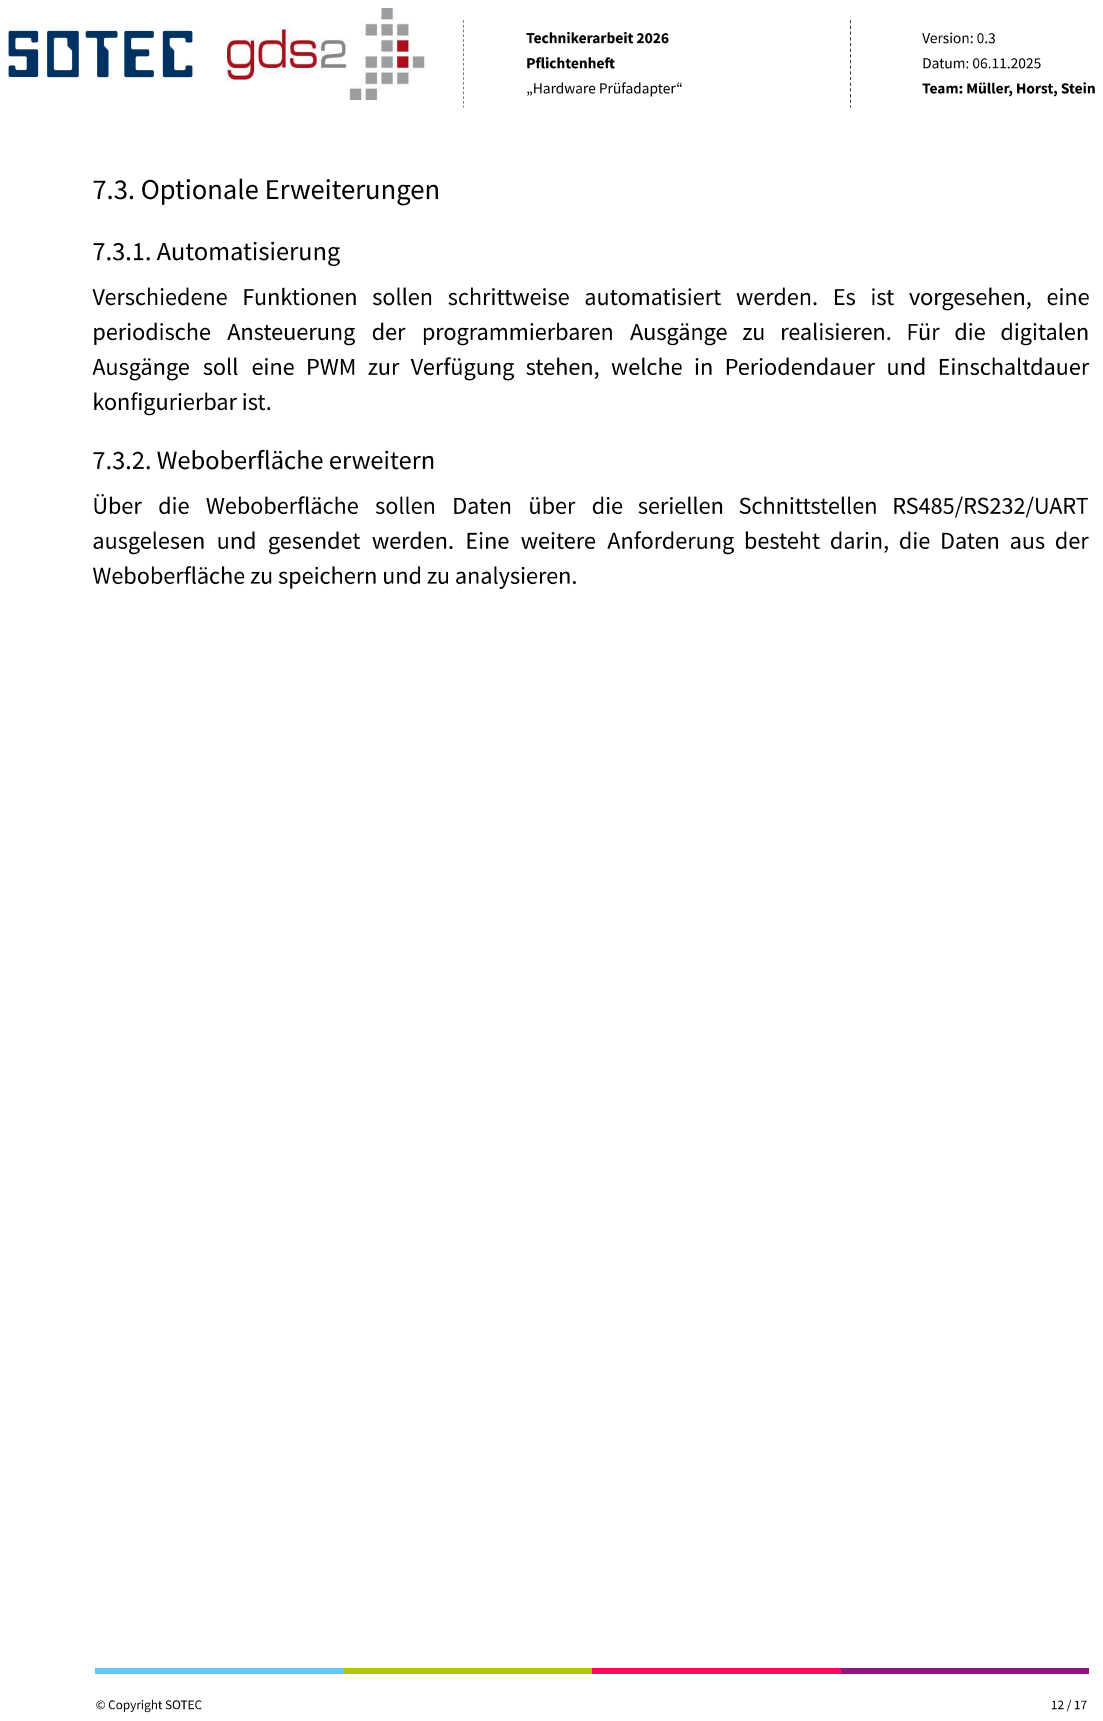
[picture p55: page 12]

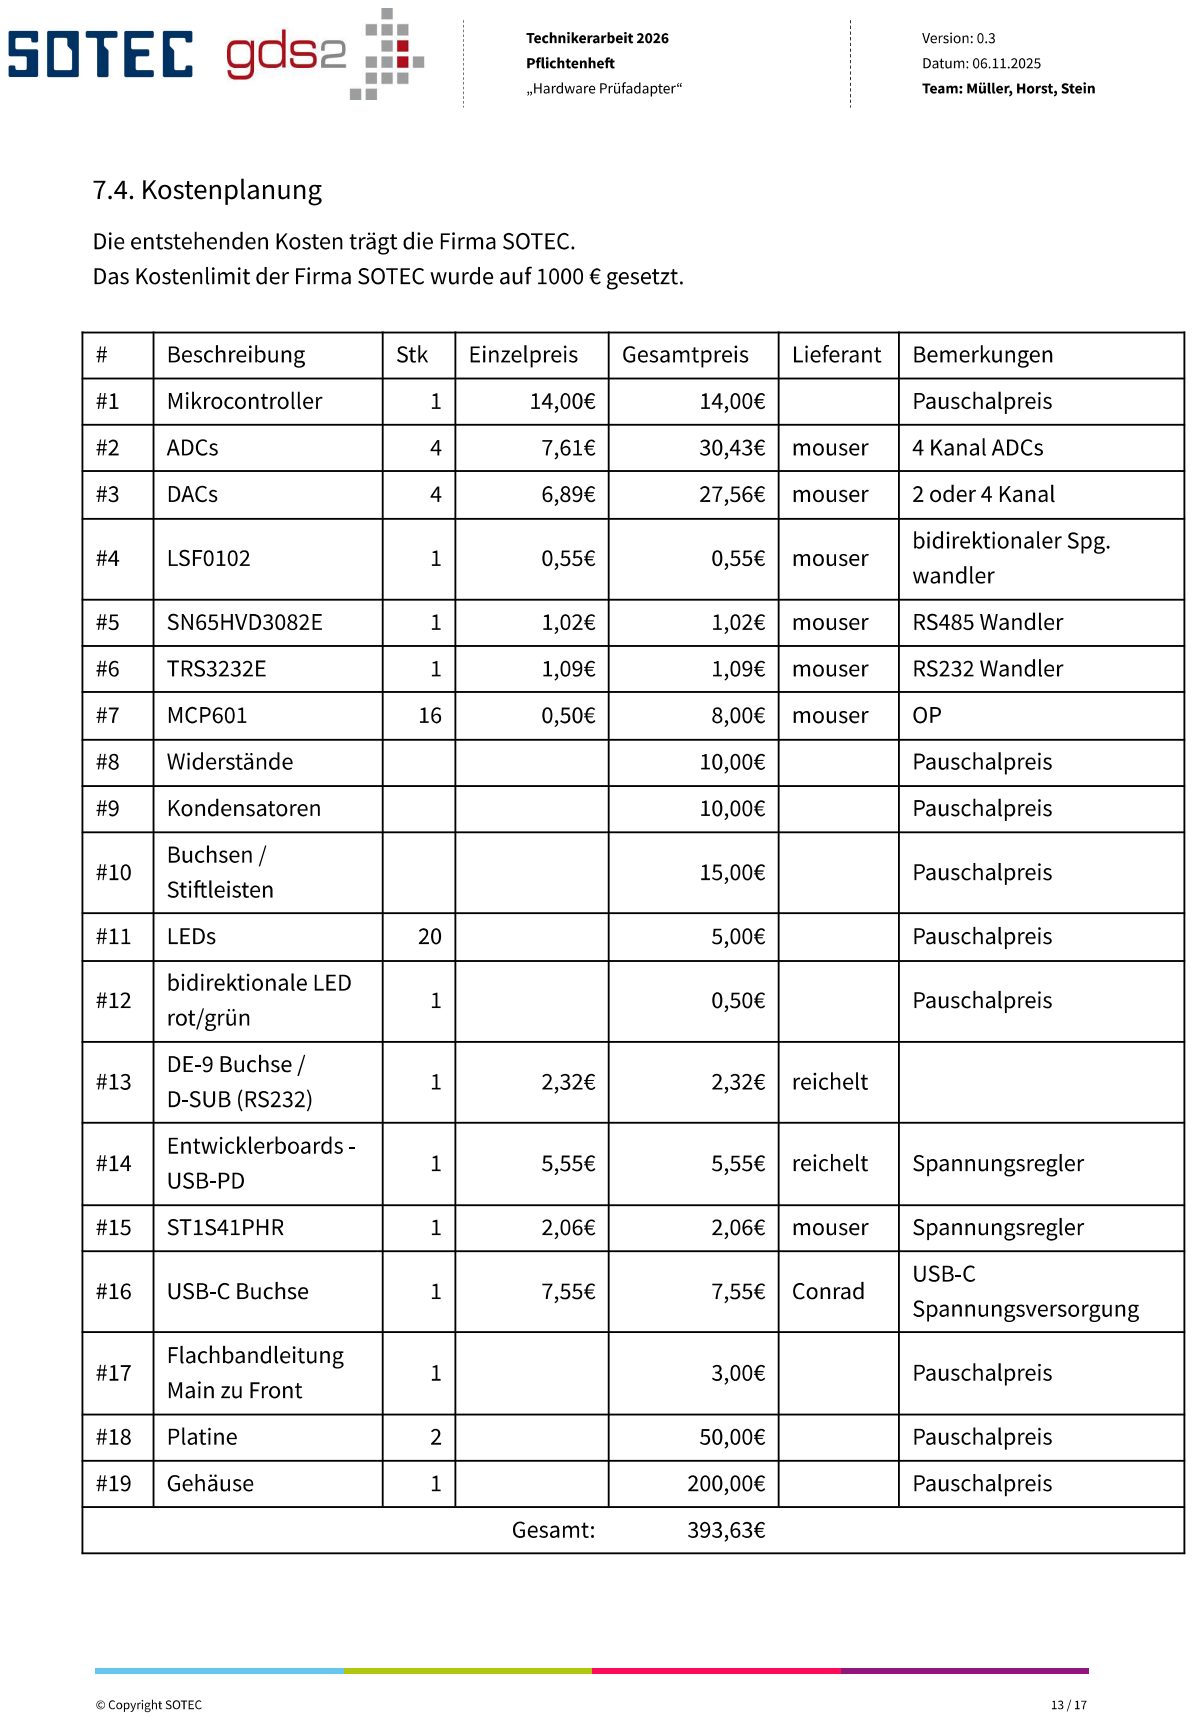
[picture p56: page 13]

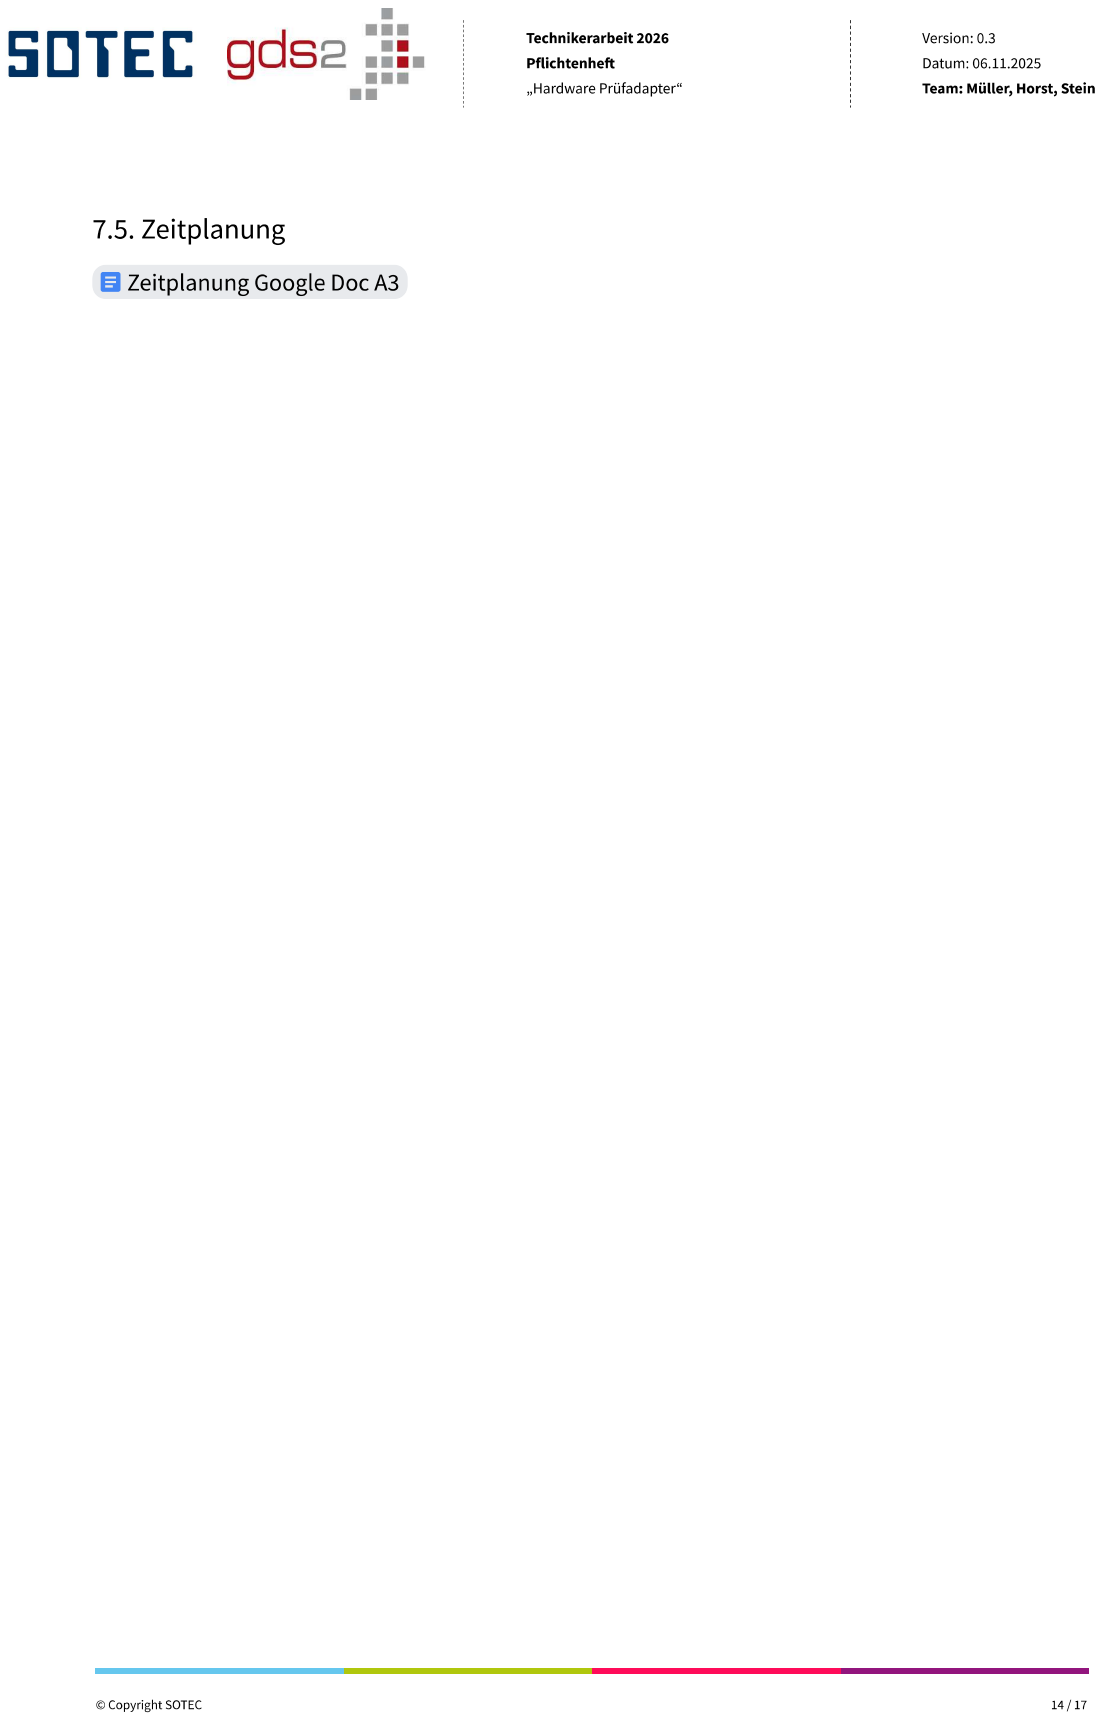
[picture p57: page 14]

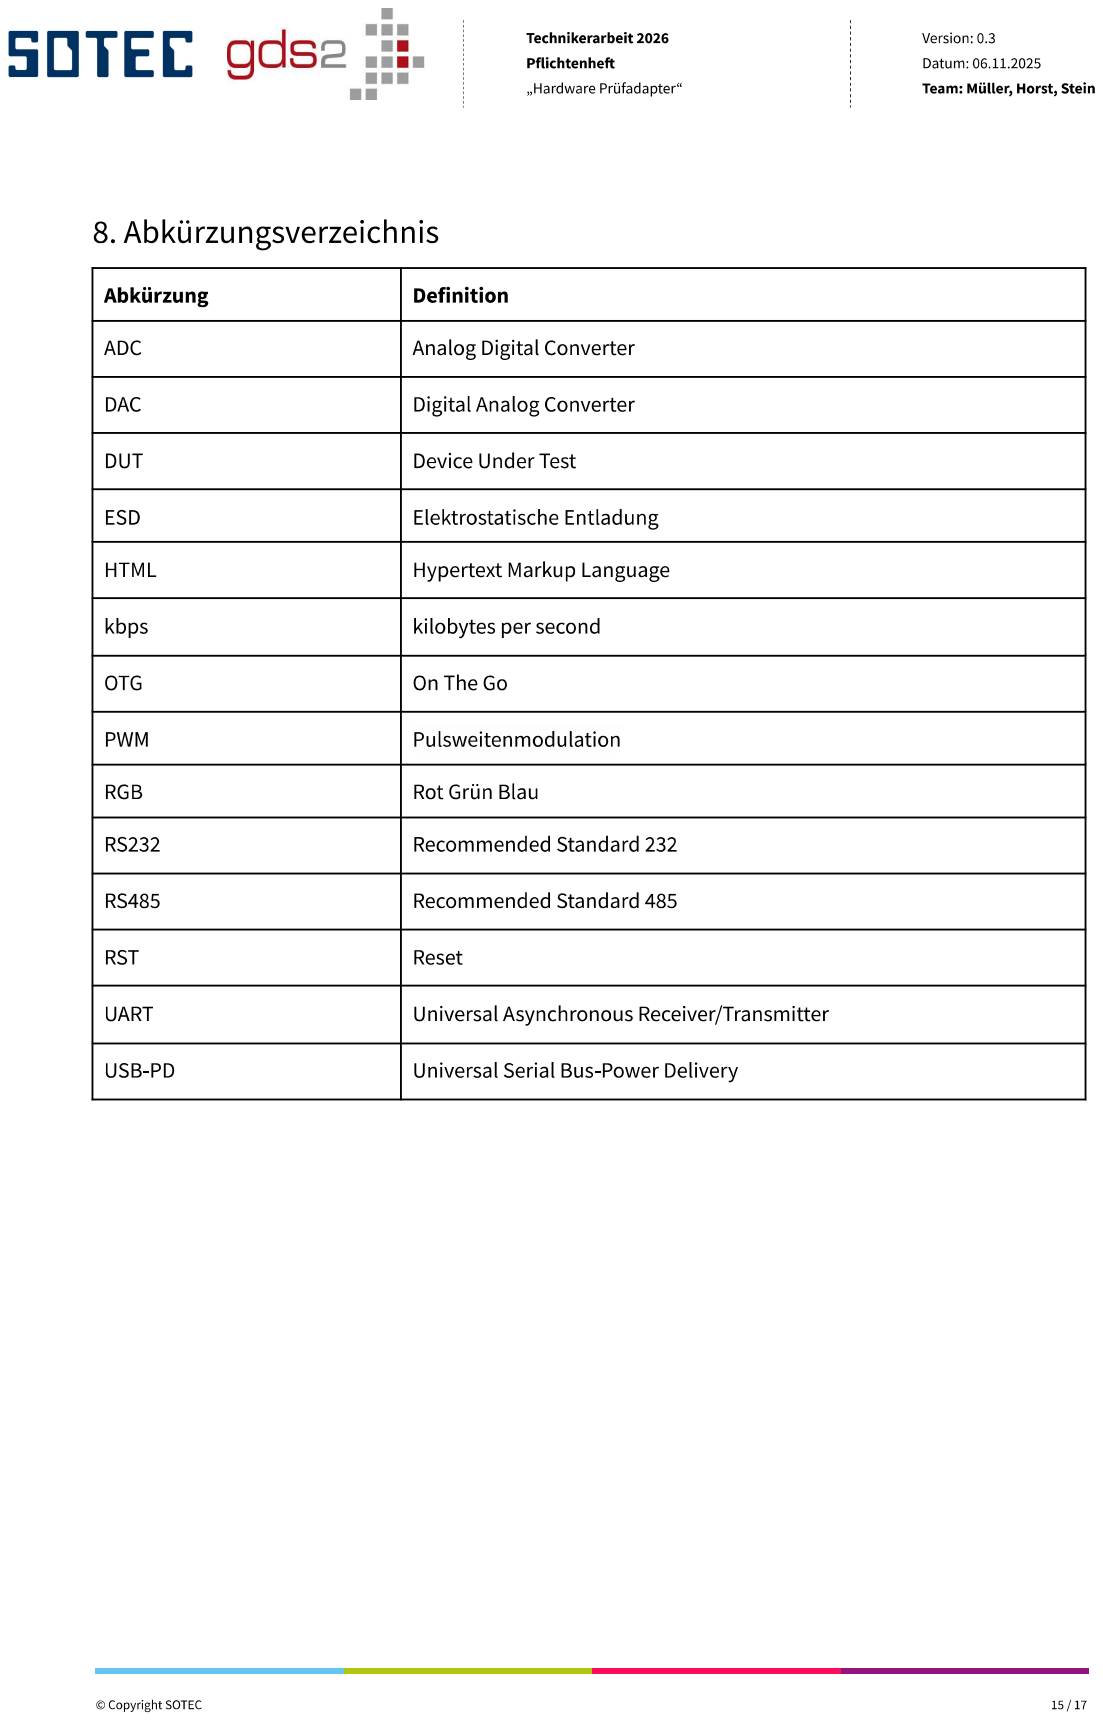
[picture p58: page 15]

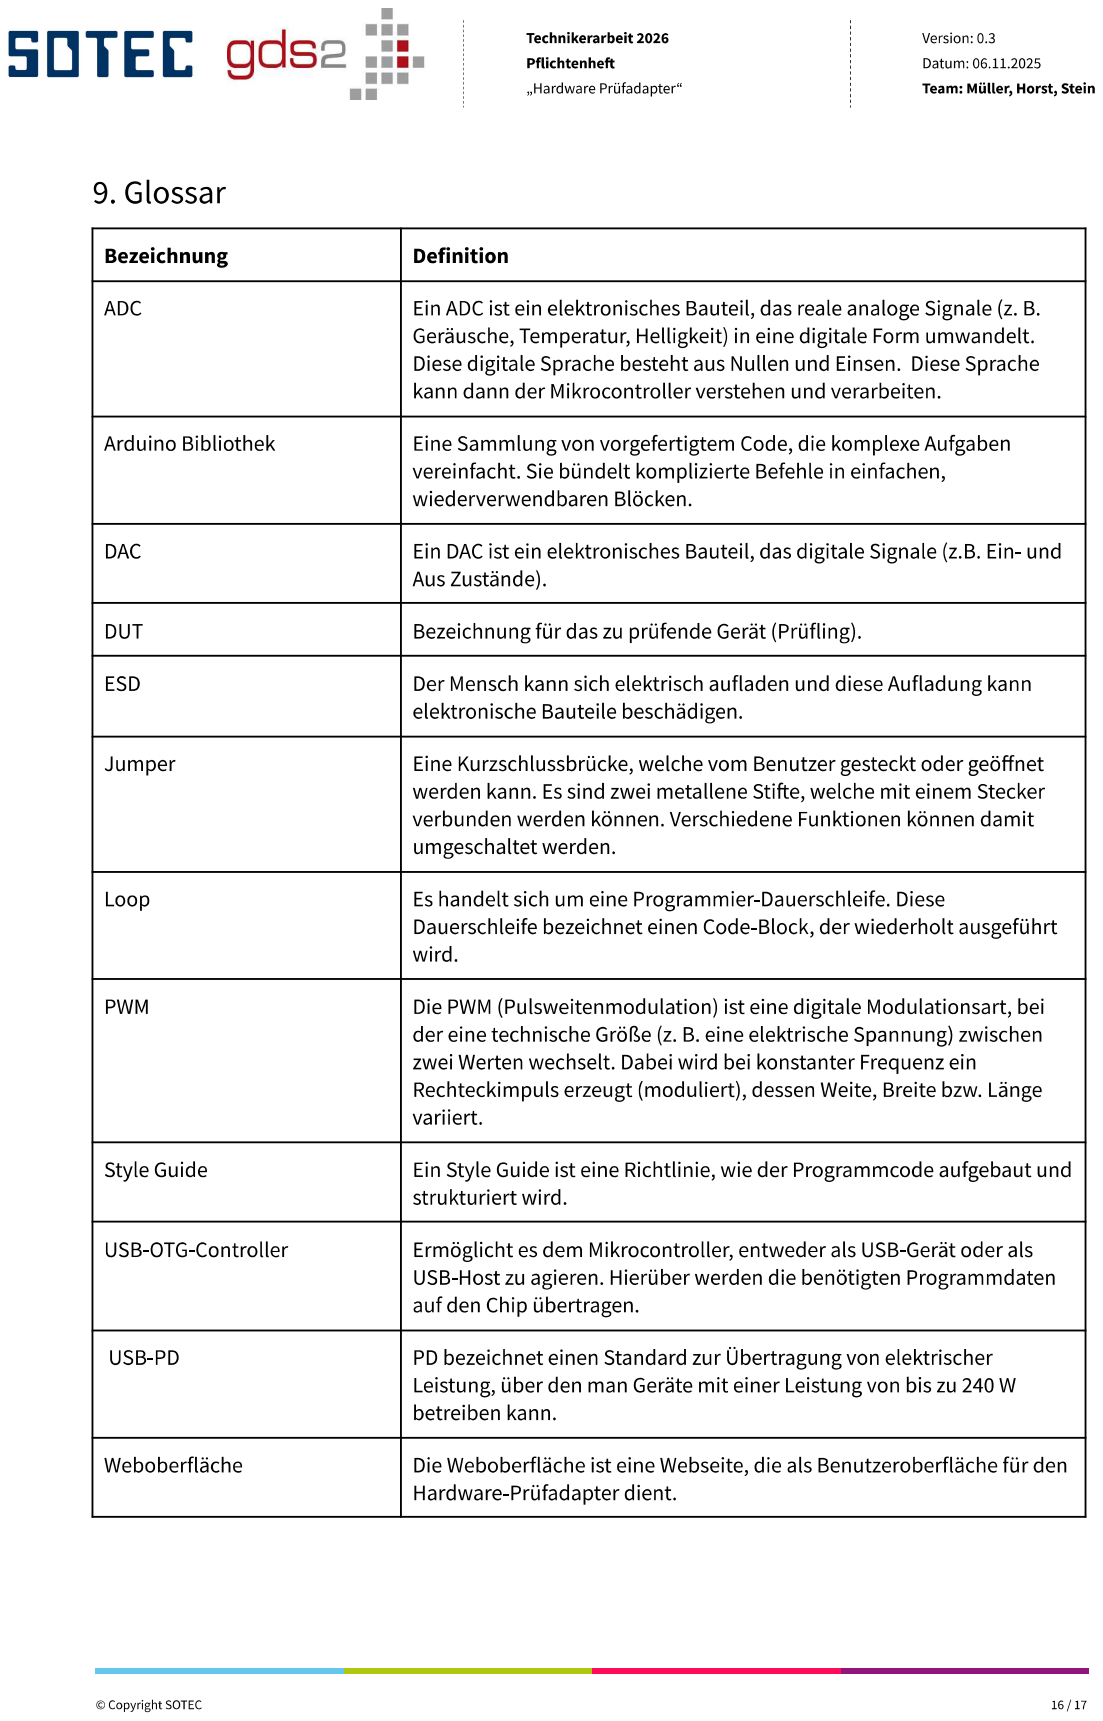
[picture p59: page 16]

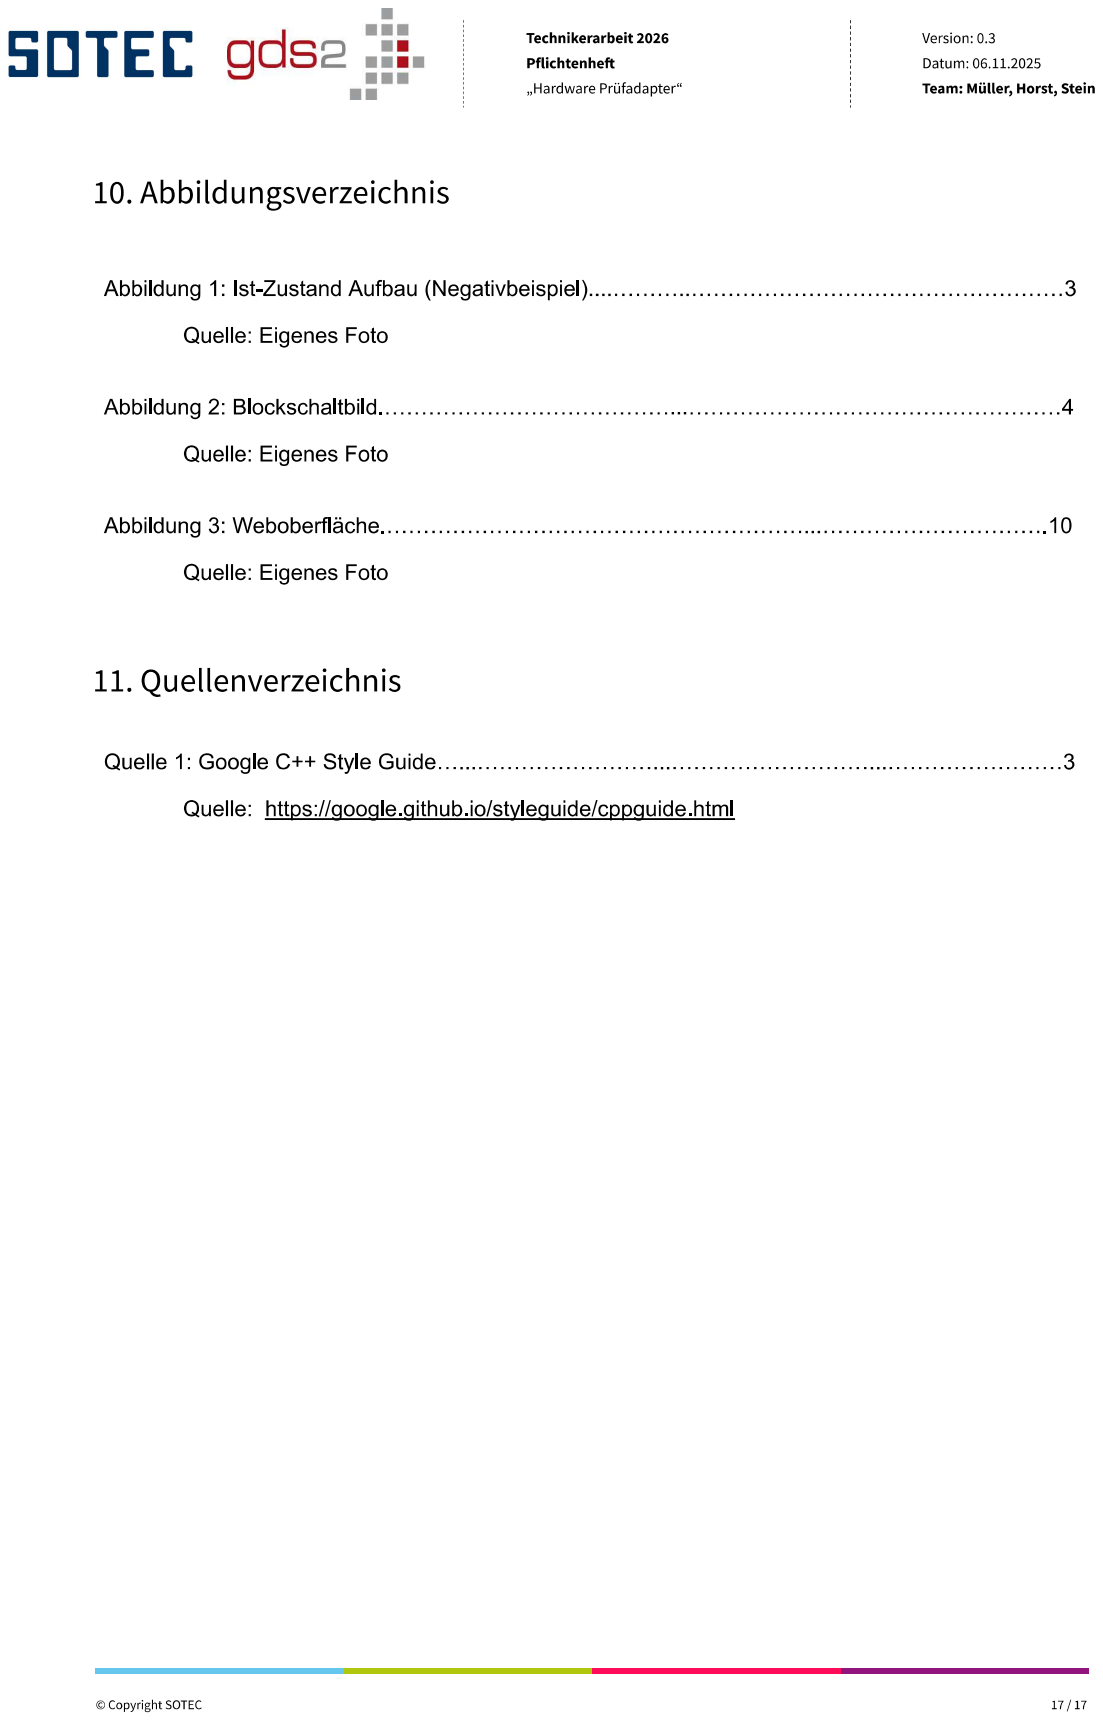
[picture p60: page 17]
