CodeByMika/technikerarbeit2026-hardwarepruefadapter/Hardware/hardware-pruefadapter/Analog-Eingaenge.kicad_sch

## KiCad design Hardware/hardware-pruefadapter/Analog-Eingaenge.kicad_sch (2026-06-18)

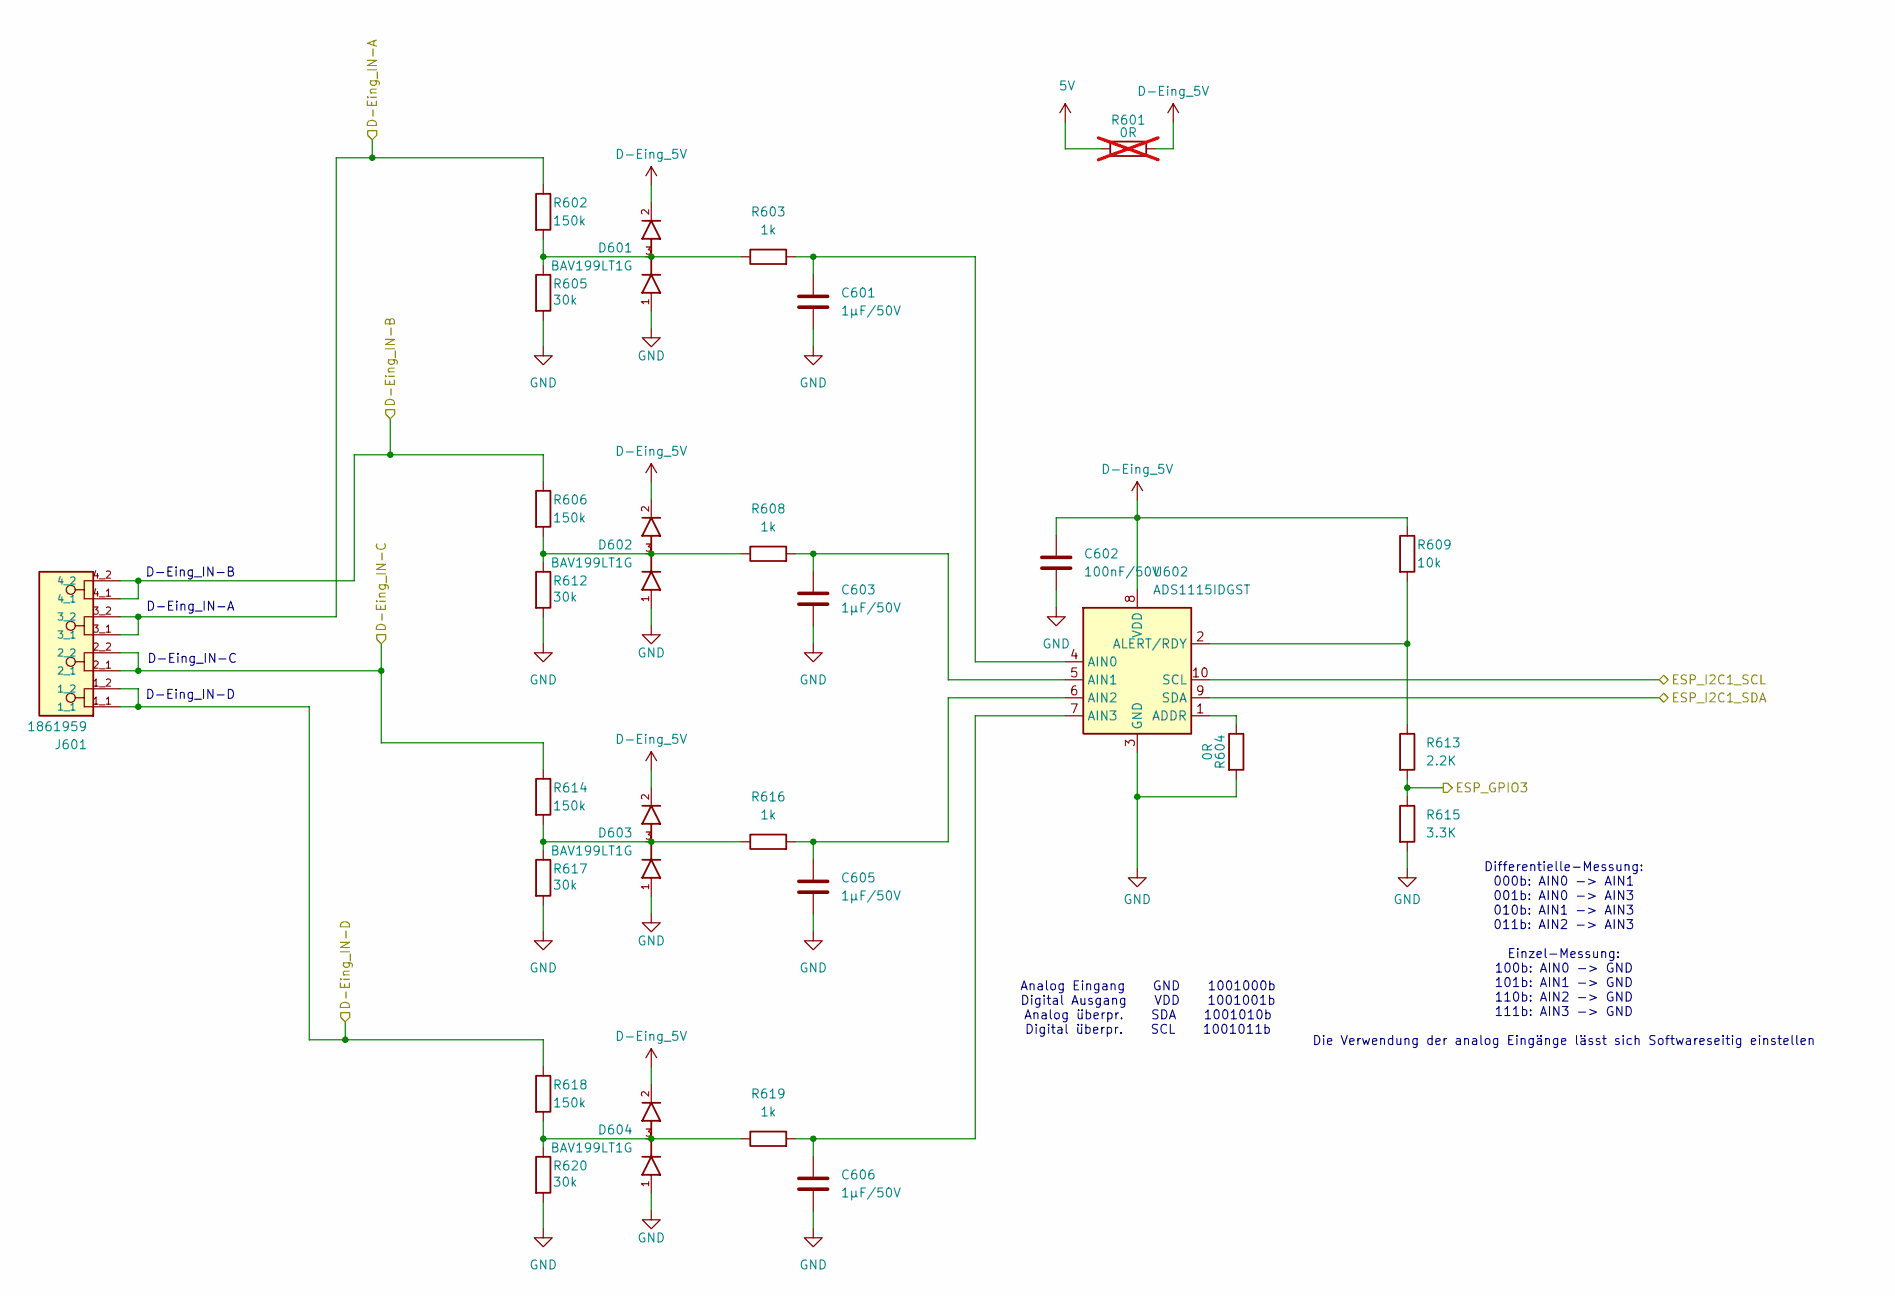
[picture p61: schematic Analog-Eingaenge.kicad_sch]

Parts:
C601, C603, C605, C606: 1µF/50V; C_0805_2012Metric; JLCPCB PN C28323
C602: 100nF/50V; C_0805_2012Metric; JLCPCB PN C1711
D601, D602, D603, D604: BAV199LT1G; TSOT-23; PARTREV 1.1.0; JLCPCB PN C145516
J601: 1861959; PHOENIX_1861959; Manufacturer_Part_Number 1861959; JLCPCB PN C6656102
R601: 0R; R_1206_3216Metric; JLCPCB PN C17888; not fitted
R602, R606, R614, R618: 150k; R_0805_2012Metric; JLCPCB PN C17470
R603, R608, R616, R619: 1k; R_0805_2012Metric; JLCPCB PN C17513
R604: 0R; R_0805_2012Metric; JLCPCB PN C17477
R605, R612, R617, R620: 30k; R_0805_2012Metric; JLCPCB PN C17621
R609: 10k; R_0805_2012Metric; JLCPCB PN C149881
R613: 2.2K; R_0805_2012Metric; JLCPCB PN C17520
R615: 3.3K; R_0805_2012Metric; JLCPCB PN C26010
U602: ADS1115IDGST; TSSOP-10_3x3mm_P0.5mm; Manufacturer_Part_Number ADS1115IDGST; JLCPCB PN C468683

Connections:
5V: R601.1
D-Eing_5V: C602.1, D601.2, D602.2, D603.2, D604.2, R601.2, R609.1, U602.8 (VDD)
D-Eing_IN-A: J601.3_1, J601.3_2, R602.1
D-Eing_IN-B: J601.4_1, J601.4_2, R606.1
D-Eing_IN-C: J601.2_1, J601.2_2, R614.1
D-Eing_IN-D: J601.1_1, J601.1_2, R618.1
ESP_GPIO3: R613.2, R615.1
ESP_I2C1_SCL: U602.10 (SCL)
ESP_I2C1_SDA: U602.9 (SDA)
GND: C601.2, C602.2, C603.2, C605.2, C606.2, D601.1, D602.1, D603.1, D604.1, R604.2, R605.2, R612.2, R615.2, R617.2, R620.2, U602.3 (GND)
unnamed: C601.1, R603.2, U602.4 (AIN0)
unnamed: C603.1, R608.2, U602.5 (AIN1)
unnamed: C605.1, R616.2, U602.6 (AIN2)
unnamed: C606.1, R619.2, U602.7 (AIN3)
unnamed: D601.3, R602.2, R603.1, R605.1
unnamed: D602.3, R606.2, R608.1, R612.1
unnamed: D603.3, R614.2, R616.1, R617.1
unnamed: D604.3, R618.2, R619.1, R620.1
unnamed: R604.1, U602.1 (ADDR)
unnamed: R609.2, R613.1, U602.2 (ALERT/RDY)

Notes on the sheet:
D-Eing_IN-D
D-Eing_IN-A
Analog Eingang GND 1001000b Digital Ausgang VDD 1001001b Analog überpr. SDA 1001010b Digital überpr. SCL 1001011b
D-Eing_IN-B
D-Eing_IN-C
Differentielle-Messung: 000b: AIN0 -> AIN1 001b: AIN0 -> AIN3 010b: AIN1 -> AIN3 011b: AIN2 -> AIN3 Einzel-Messung: 100b: AIN0 -> GND 101b: AIN1 -> GND 110b: AIN2 -> GND 111b: AIN3 -> GND Die Verwendung der analog Eingänge lässt sich Softwareseitig einstellen
