CodeByMika/technikerarbeit2026-hardwarepruefadapter/Hardware/hardware-pruefadapter/Analoge-Ausgaeng.kicad_sch

## KiCad design Hardware/hardware-pruefadapter/Analoge-Ausgaeng.kicad_sch (2026-06-18)

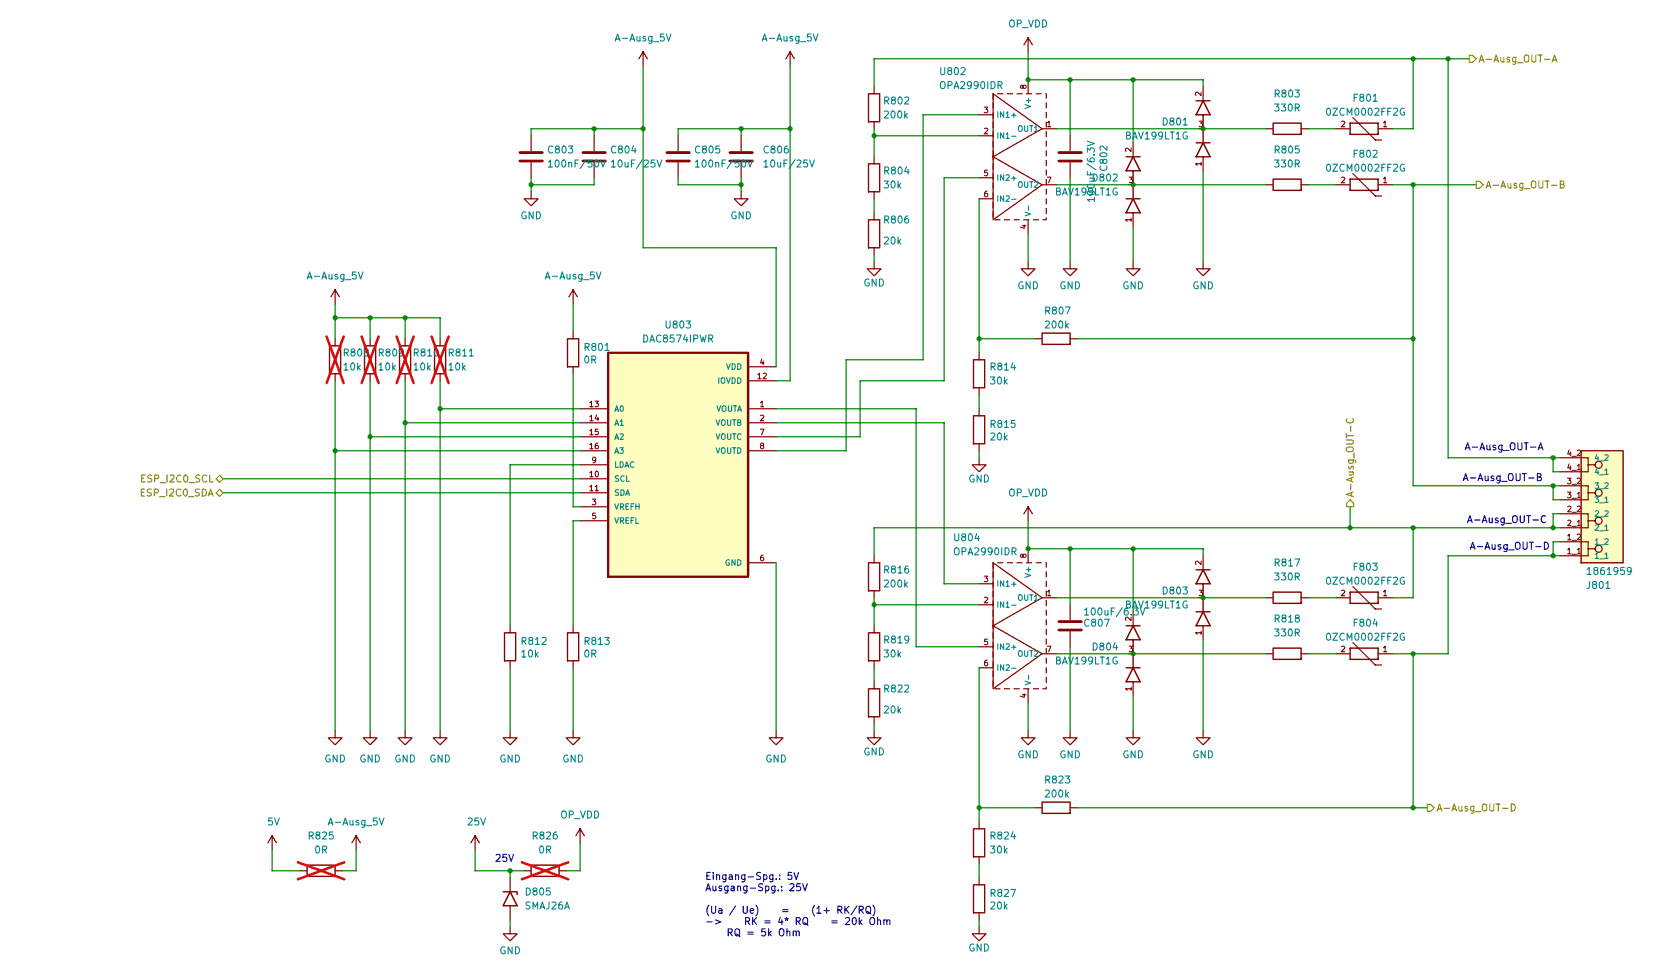
[picture p62: schematic Analoge-Ausgaeng.kicad_sch, part in row 1, column 2]

Parts:
C802, C807: 100uF/6.3V; C_1206_3216Metric; JLCPCB PN C15008
C803, C805: 100nF/50V; C_0805_2012Metric; JLCPCB PN C1711
C804, C806: 10uF/25V; C_0805_2012Metric; JLCPCB PN C15850
D801, D802, D803, D804: BAV199LT1G; TSOT-23; PARTREV 1.1.0; JLCPCB PN C145516
D805: SMAJ26A; D_SMA; Manufacturer_Part_Number SMAJ26A; JLCPCB PN C49370
F801, F802, F803, F804: 0ZCM0002FF2G; FUSC1607X85N; PARTREV Apr2020; JLCPCB PN C5299556
J801: 1861959; PHOENIX_1861959; Manufacturer_Part_Number 1861959; JLCPCB PN C6656102
R801, R813: 0R; R_0805_2012Metric; JLCPCB PN C17477
R802, R807, R816, R823: 200k; R_0805_2012Metric; JLCPCB PN C17539
R803, R805, R817, R818: 330R; R_2512_6332Metric; JLCPCB PN C19866
R804, R814, R819, R824: 30k; R_0805_2012Metric; JLCPCB PN C17621
R806, R815, R822, R827: 20k; R_0805_2012Metric; JLCPCB PN C4328
R808, R809, R810, R811: 10k; R_0805_2012Metric; JLCPCB PN C149881; not fitted
R812: 10k; R_0805_2012Metric; JLCPCB PN C149881
R825, R826: 0R; R_0805_2012Metric; JLCPCB PN C17477; not fitted
U802, U804: OPA2990IDR; SOIC127P600X175-8N; Manufacturer_Part_Number OPA2990IDR; JLCPCB PN C2058283
U803: DAC8574IPWR; SOP65P640X120-16N; Manufacturer_Part_Number DAC8574IPWR; JLCPCB PN C2864663

Connections:
5V: R825.1
25V: D805.1 (A1), R826.1
A-Ausg_5V: C803.1, C804.1, C805.1, C806.1, R801.1, R808.1, R809.1, R810.1, R811.1, R825.2, U803.4 (VDD), U803.12 (IOVDD)
A-Ausg_OUT-A: F801.1, J801.4_1, J801.4_2, R802.1
A-Ausg_OUT-B: F802.1, J801.3_1, J801.3_2, R807.2
A-Ausg_OUT-C: F803.1, J801.2_1, J801.2_2, R816.1
A-Ausg_OUT-D: F804.1, J801.1_1, J801.1_2, R823.2
ESP_I2C0_SCL: U803.10 (SCL)
ESP_I2C0_SDA: U803.11 (SDA)
GND: C802.1, C803.2, C804.2, C805.2, C806.2, C807.1, D801.1, D802.1, D803.1, D804.1, D805.2 (A2), R806.2, R808.2, R809.2, R810.2, R811.2, R812.2, R813.2, R815.2, R822.2, R827.2, U802.4 (V-), U803.6 (GND), U803.13 (A0), U803.14 (A1), U803.15 (A2), U803.16 (A3), U804.4 (V-)
unnamed: D801.3, R803.1, U802.1 (OUT1)
unnamed: D802.3, R805.1, U802.7 (OUT2)
unnamed: D803.3, R817.1, U804.1 (OUT1)
unnamed: D804.3, R818.1, U804.7 (OUT2)
unnamed: F801.2, R803.2
unnamed: F802.2, R805.2
unnamed: F803.2, R817.2
unnamed: F804.2, R818.2
unnamed: R801.2, U803.3 (VREFH)
unnamed: R802.2, R804.1, U802.2 (IN1-)
unnamed: R804.2, R806.1
unnamed: R807.1, R814.1, U802.6 (IN2-)
unnamed: R812.1, U803.9 (LDAC)
unnamed: R813.1, U803.5 (VREFL)
unnamed: R814.2, R815.1
unnamed: R816.2, R819.1, U804.2 (IN1-)
unnamed: R819.2, R822.1
unnamed: R823.1, R824.1, U804.6 (IN2-)
unnamed: R824.2, R827.1
unnamed: U802.3 (IN1+), U803.8 (VOUTD)
unnamed: U802.5 (IN2+), U803.7 (VOUTC)
unnamed: U803.1 (VOUTA), U804.5 (IN2+)
unnamed: U803.2 (VOUTB), U804.3 (IN1+)
OP_VDD: C802.2, C807.2, D801.2, D802.2, D803.2, D804.2, R826.2, U802.8 (V+), U804.8 (V+)

Notes on the sheet:
A-Ausg_OUT-B
A-Ausg_OUT-A
A-Ausg_OUT-C
A-Ausg_OUT-D
25V
https://www.ti.com/lit/ug/slau109/slau109.pdf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
Eingang-Spg.: 5V Ausgang-Spg.: 25V (Ua / Ue) = (1+ RK/RQ) -> RK = 4* RQ = 20k Ohm RQ = 5k Ohm
