CodeByMika/technikerarbeit2026-hardwarepruefadapter/Hardware/hardware-pruefadapter/Ausgang-Ueberpruefung.kicad_sch

## KiCad design Hardware/hardware-pruefadapter/Ausgang-Ueberpruefung.kicad_sch (2026-06-18)

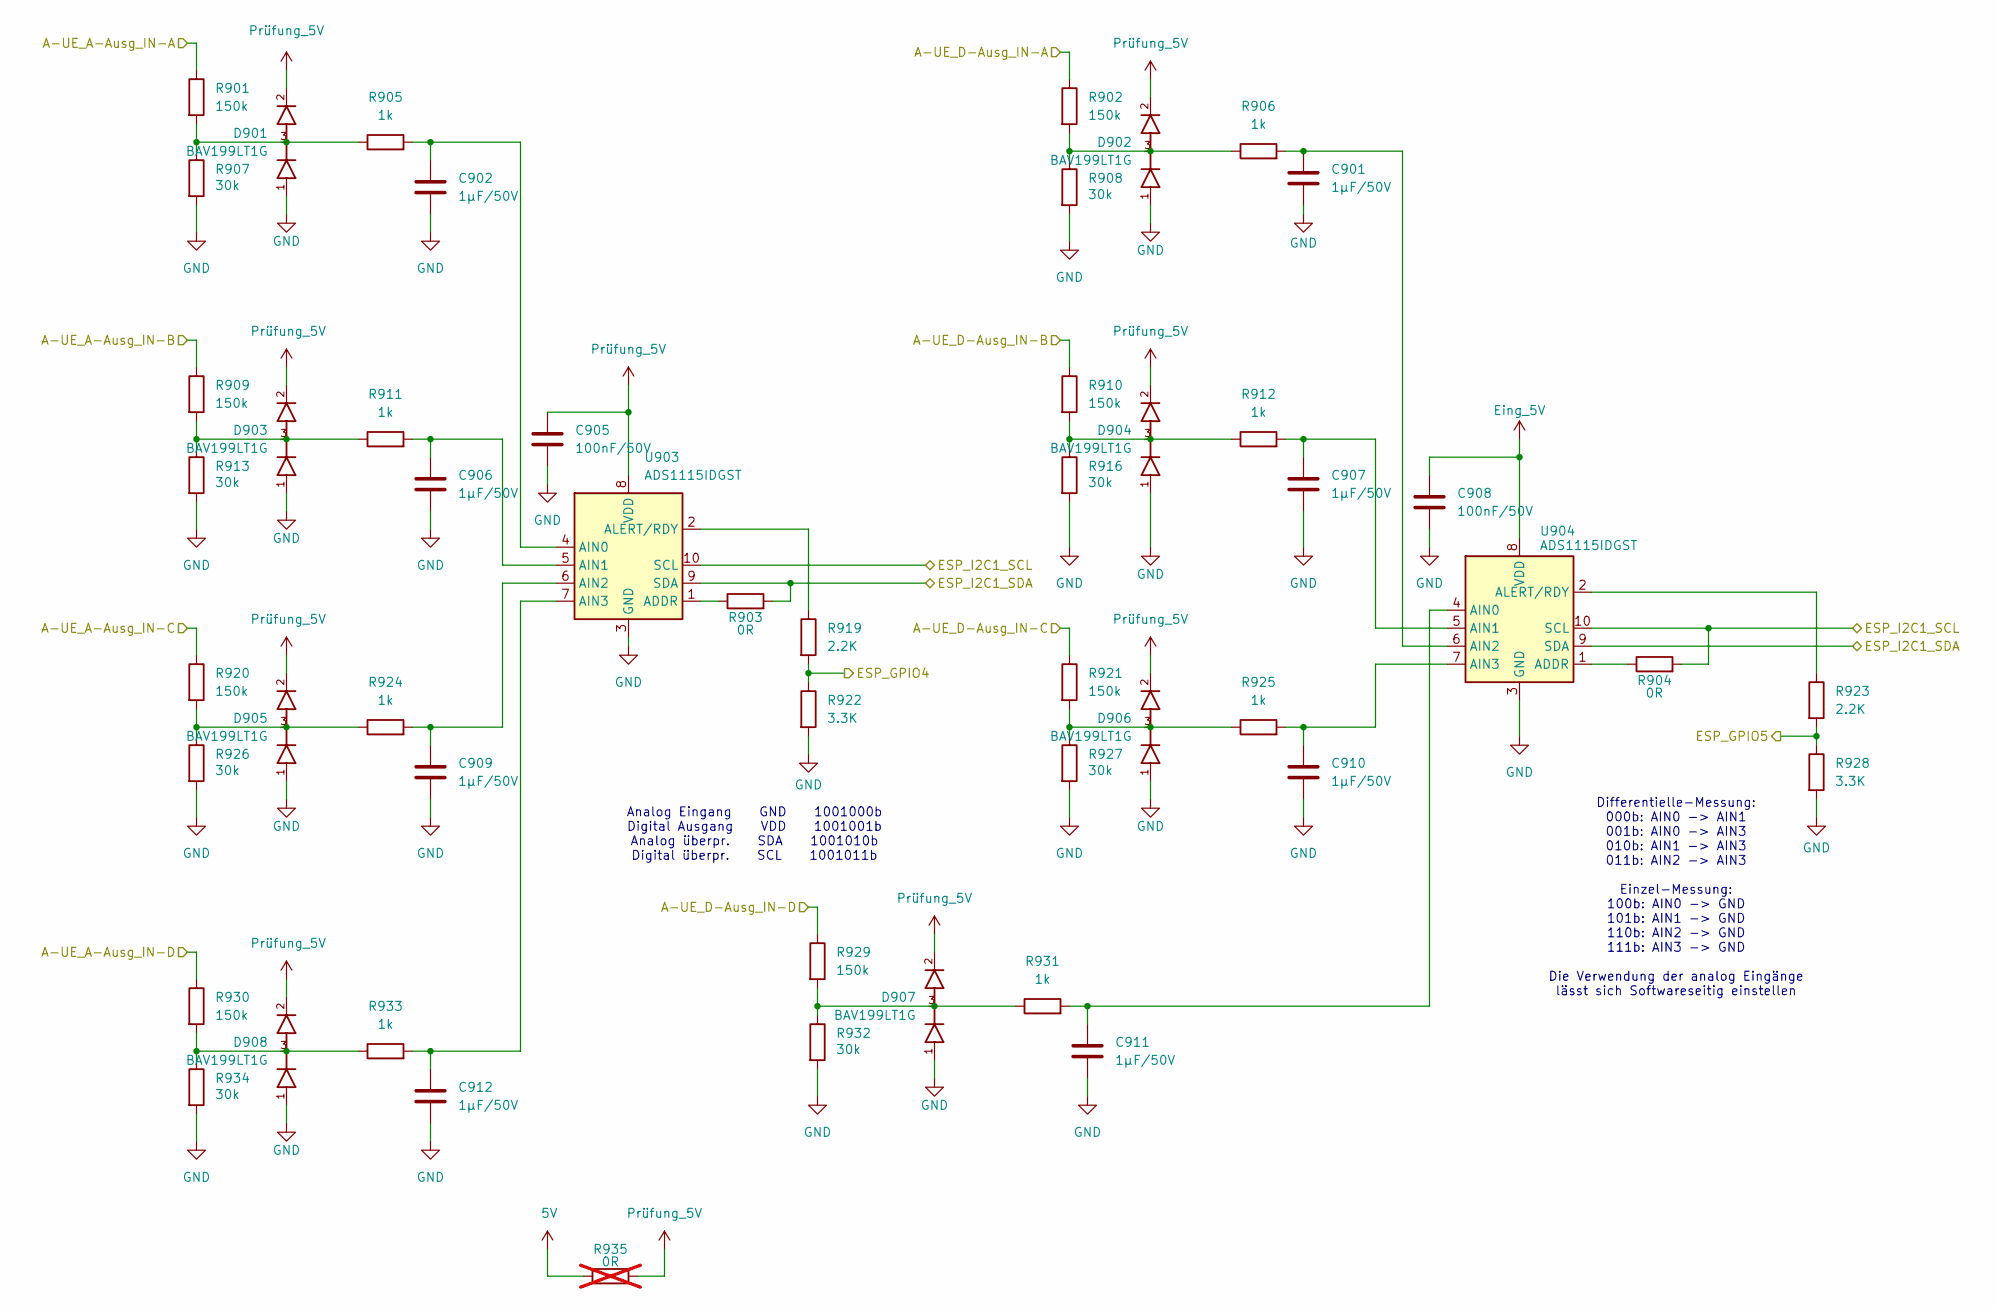
[picture p63: schematic Ausgang-Ueberpruefung.kicad_sch]

Parts:
C901, C902, C906, C907, C909, C910, C911, C912: 1µF/50V; C_0805_2012Metric; JLCPCB PN C28323
C905, C908: 100nF/50V; C_0805_2012Metric; JLCPCB PN C1711
D901, D902, D903, D904, D905, D906, D907, D908: BAV199LT1G; TSOT-23; PARTREV 1.1.0; JLCPCB PN C145516
R901, R902, R909, R910, R920, R921, R929, R930: 150k; R_0805_2012Metric; JLCPCB PN C17470
R903, R904: 0R; R_0805_2012Metric; JLCPCB PN C17477
R905, R906, R911, R912, R924, R925, R931, R933: 1k; R_0805_2012Metric; JLCPCB PN C17513
R907, R908, R913, R916, R926, R927, R932, R934: 30k; R_0805_2012Metric; JLCPCB PN C17621
R919, R923: 2.2K; R_0805_2012Metric; JLCPCB PN C17520
R922, R928: 3.3K; R_0805_2012Metric; JLCPCB PN C26010
R935: 0R; R_1206_3216Metric; JLCPCB PN C17888; not fitted
U903, U904: ADS1115IDGST; TSSOP-10_3x3mm_P0.5mm; Manufacturer_Part_Number ADS1115IDGST; JLCPCB PN C468683

Connections:
5V: R935.1
A-UE_A-Ausg_IN-A: R901.1
A-UE_A-Ausg_IN-B: R909.1
A-UE_A-Ausg_IN-C: R920.1
A-UE_A-Ausg_IN-D: R930.1
A-UE_D-Ausg_IN-A: R902.1
A-UE_D-Ausg_IN-B: R910.1
A-UE_D-Ausg_IN-C: R921.1
A-UE_D-Ausg_IN-D: R929.1
ESP_GPIO4: R919.2, R922.1
ESP_GPIO5: R923.2, R928.1
ESP_I2C1_SCL: R904.2, U903.10 (SCL), U904.10 (SCL)
ESP_I2C1_SDA: R903.2, U903.9 (SDA), U904.9 (SDA)
Eing_5V: C908.1, U904.8 (VDD)
GND: C901.2, C902.2, C905.2, C906.2, C907.2, C908.2, C909.2, C910.2, C911.2, C912.2, D901.1, D902.1, D903.1, D904.1, D905.1, D906.1, D907.1, D908.1, R907.2, R908.2, R913.2, R916.2, R922.2, R926.2, R927.2, R928.2, R932.2, R934.2, U903.3 (GND), U904.3 (GND)
unnamed: C901.1, R906.2, U904.6 (AIN2)
unnamed: C902.1, R905.2, U903.4 (AIN0)
unnamed: C906.1, R911.2, U903.5 (AIN1)
unnamed: C907.1, R912.2, U904.5 (AIN1)
unnamed: C909.1, R924.2, U903.6 (AIN2)
unnamed: C910.1, R925.2, U904.7 (AIN3)
unnamed: C911.1, R931.2, U904.4 (AIN0)
unnamed: C912.1, R933.2, U903.7 (AIN3)
unnamed: D901.3, R901.2, R905.1, R907.1
unnamed: D902.3, R902.2, R906.1, R908.1
unnamed: D903.3, R909.2, R911.1, R913.1
unnamed: D904.3, R910.2, R912.1, R916.1
unnamed: D905.3, R920.2, R924.1, R926.1
unnamed: D906.3, R921.2, R925.1, R927.1
unnamed: D907.3, R929.2, R931.1, R932.1
unnamed: D908.3, R930.2, R933.1, R934.1
unnamed: R903.1, U903.1 (ADDR)
unnamed: R904.1, U904.1 (ADDR)
unnamed: R919.1, U903.2 (ALERT/RDY)
unnamed: R923.1, U904.2 (ALERT/RDY)
Prüfung_5V: C905.1, D901.2, D902.2, D903.2, D904.2, D905.2, D906.2, D907.2, D908.2, R935.2, U903.8 (VDD)

Notes on the sheet:
Analog Eingang GND 1001000b Digital Ausgang VDD 1001001b Analog überpr. SDA 1001010b Digital überpr. SCL 1001011b
Differentielle-Messung: 000b: AIN0 -> AIN1 001b: AIN0 -> AIN3 010b: AIN1 -> AIN3 011b: AIN2 -> AIN3 Einzel-Messung: 100b: AIN0 -> GND 101b: AIN1 -> GND 110b: AIN2 -> GND 111b: AIN3 -> GND Die Verwendung der analog Eingänge lässt sich Softwareseitig einstellen
