CodeByMika/technikerarbeit2026-hardwarepruefadapter/Hardware/hardware-pruefadapter/Digital-Eingaenge.kicad_sch

## KiCad design Hardware/hardware-pruefadapter/Digital-Eingaenge.kicad_sch (2026-06-18)

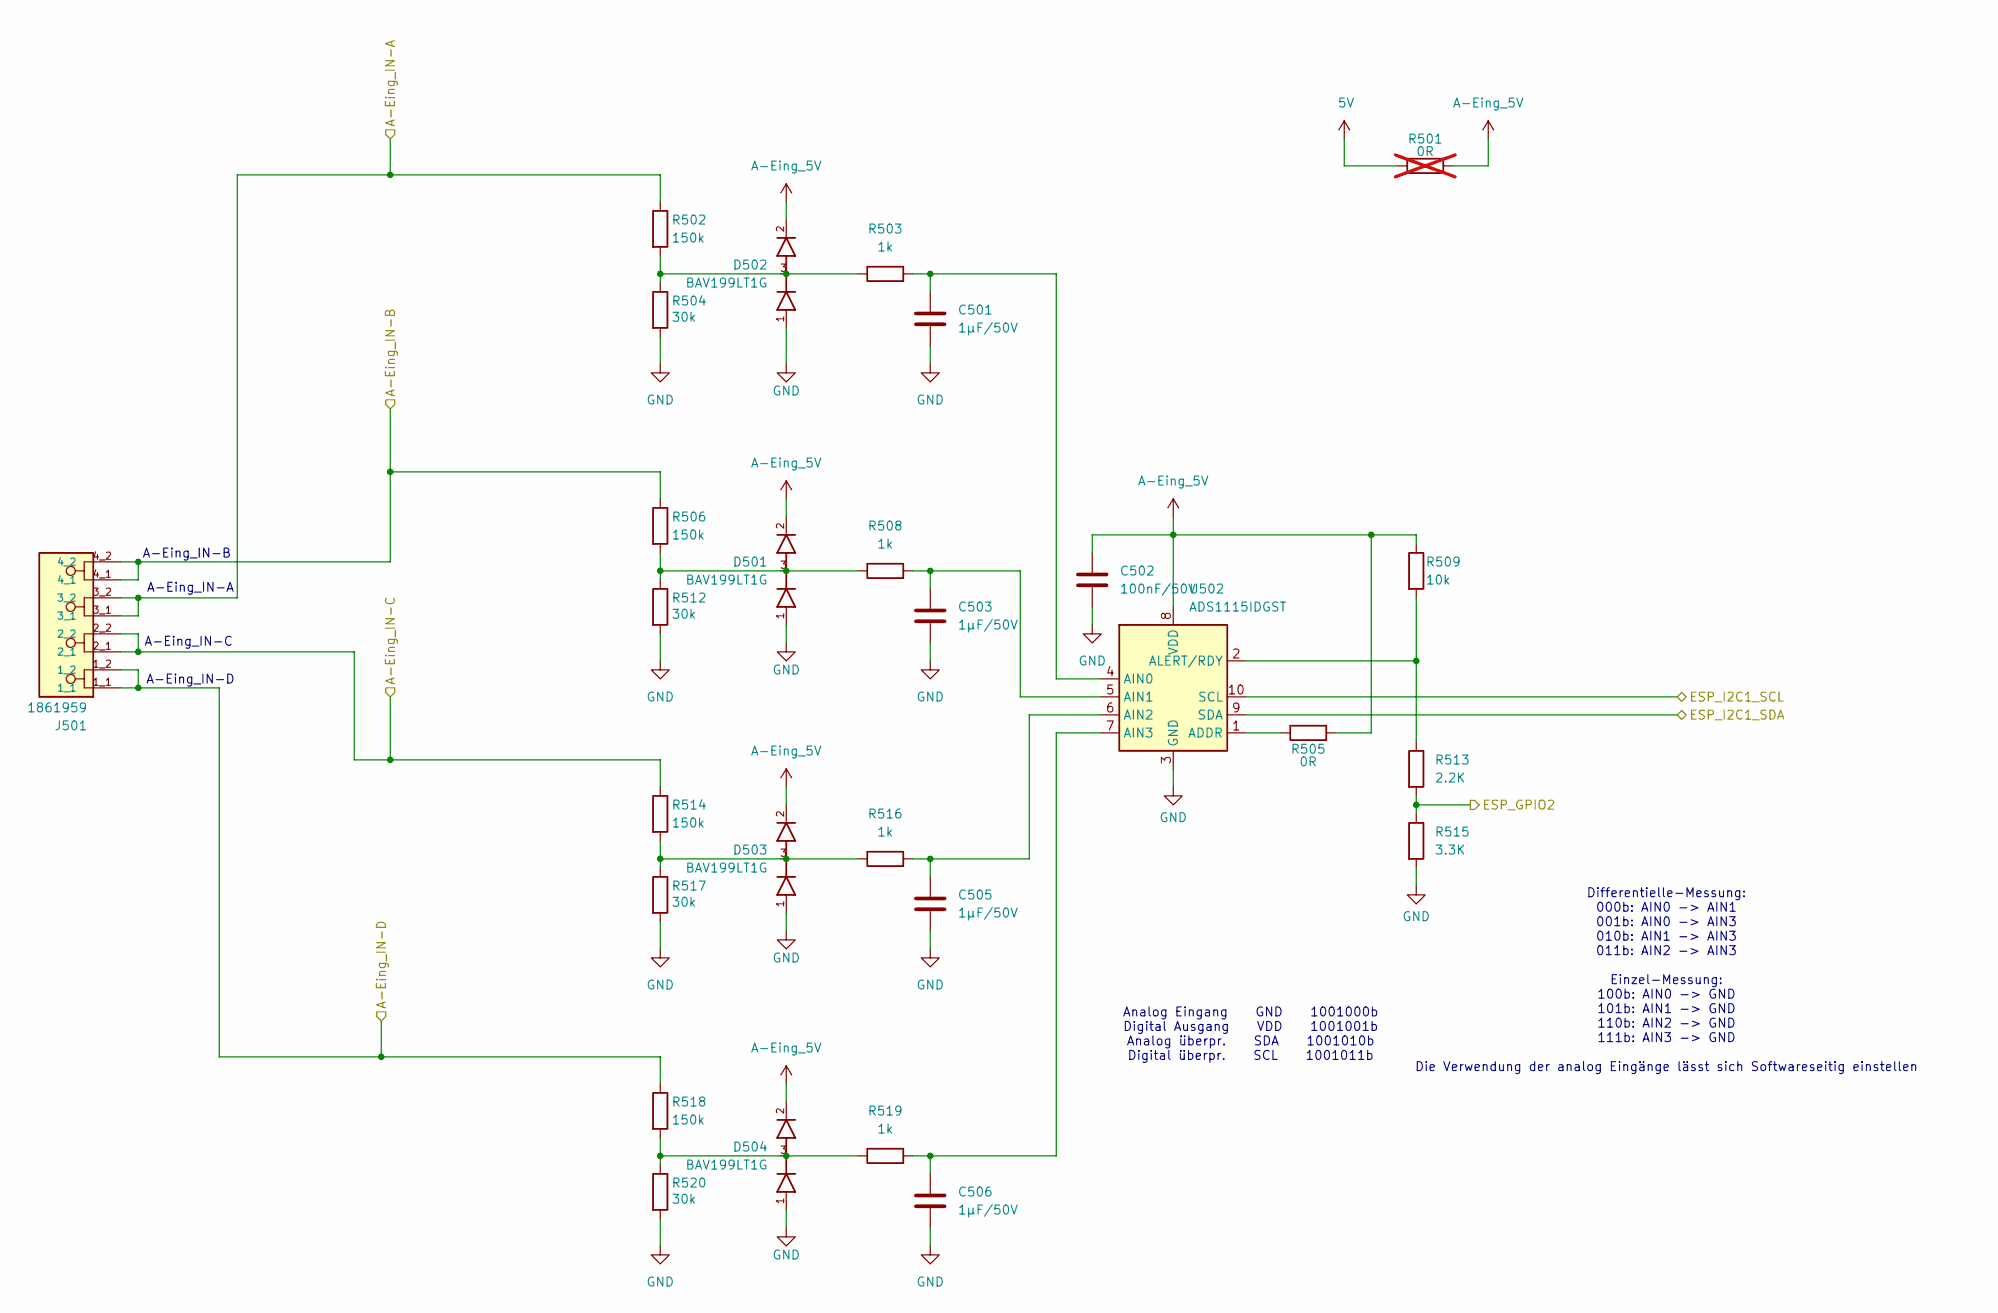
[picture p64: schematic Digital-Eingaenge.kicad_sch]

Parts:
C501, C503, C505, C506: 1µF/50V; C_0805_2012Metric; JLCPCB PN C28323
C502: 100nF/50V; C_0805_2012Metric; JLCPCB PN C1711
D501, D502, D503, D504: BAV199LT1G; TSOT-23; PARTREV 1.1.0; JLCPCB PN C145516
J501: 1861959; PHOENIX_1861959; Manufacturer_Part_Number 1861959; JLCPCB PN C6656102
R501: 0R; R_1206_3216Metric; JLCPCB PN C17888; not fitted
R502, R506, R514, R518: 150k; R_0805_2012Metric; JLCPCB PN C17470
R503, R508, R516, R519: 1k; R_0805_2012Metric; JLCPCB PN C17513
R504, R512, R517, R520: 30k; R_0805_2012Metric; JLCPCB PN C17621
R505: 0R; R_0805_2012Metric; JLCPCB PN C17477
R509: 10k; R_0805_2012Metric; JLCPCB PN C149881
R513: 2.2K; R_0805_2012Metric; JLCPCB PN C17520
R515: 3.3K; R_0805_2012Metric; JLCPCB PN C26010
U502: ADS1115IDGST; TSSOP-10_3x3mm_P0.5mm; Manufacturer_Part_Number ADS1115IDGST; JLCPCB PN C468683

Connections:
5V: R501.1
A-Eing_5V: C502.2, D501.2, D502.2, D503.2, D504.2, R501.2, R505.2, R509.1, U502.8 (VDD)
A-Eing_IN-A: J501.3_1, J501.3_2, R502.1
A-Eing_IN-B: J501.4_1, J501.4_2, R506.1
A-Eing_IN-C: J501.2_1, J501.2_2, R514.1
A-Eing_IN-D: J501.1_1, J501.1_2, R518.1
ESP_GPIO2: R513.2, R515.1
ESP_I2C1_SCL: U502.10 (SCL)
ESP_I2C1_SDA: U502.9 (SDA)
GND: C501.2, C502.1, C503.2, C505.2, C506.2, D501.1, D502.1, D503.1, D504.1, R504.2, R512.2, R515.2, R517.2, R520.2, U502.3 (GND)
unnamed: C501.1, R503.2, U502.4 (AIN0)
unnamed: C503.1, R508.2, U502.5 (AIN1)
unnamed: C505.1, R516.2, U502.6 (AIN2)
unnamed: C506.1, R519.2, U502.7 (AIN3)
unnamed: D501.3, R506.2, R508.1, R512.1
unnamed: D502.3, R502.2, R503.1, R504.1
unnamed: D503.3, R514.2, R516.1, R517.1
unnamed: D504.3, R518.2, R519.1, R520.1
unnamed: R505.1, U502.1 (ADDR)
unnamed: R509.2, R513.1, U502.2 (ALERT/RDY)

Notes on the sheet:
A-Eing_IN-B
Differentielle-Messung: 000b: AIN0 -> AIN1 001b: AIN0 -> AIN3 010b: AIN1 -> AIN3 011b: AIN2 -> AIN3 Einzel-Messung: 100b: AIN0 -> GND 101b: AIN1 -> GND 110b: AIN2 -> GND 111b: AIN3 -> GND Die Verwendung der analog Eingänge lässt sich Softwareseitig einstellen
A-Eing_IN-A
A-Eing_IN-C
A-Eing_IN-D
Analog Eingang GND 1001000b Digital Ausgang VDD 1001001b Analog überpr. SDA 1001010b Digital überpr. SCL 1001011b
