CodeByMika/technikerarbeit2026-hardwarepruefadapter/Hardware/hardware-pruefadapter/Digitale-Ausgaenge.kicad_sch

## KiCad design Hardware/hardware-pruefadapter/Digitale-Ausgaenge.kicad_sch (2026-06-18)

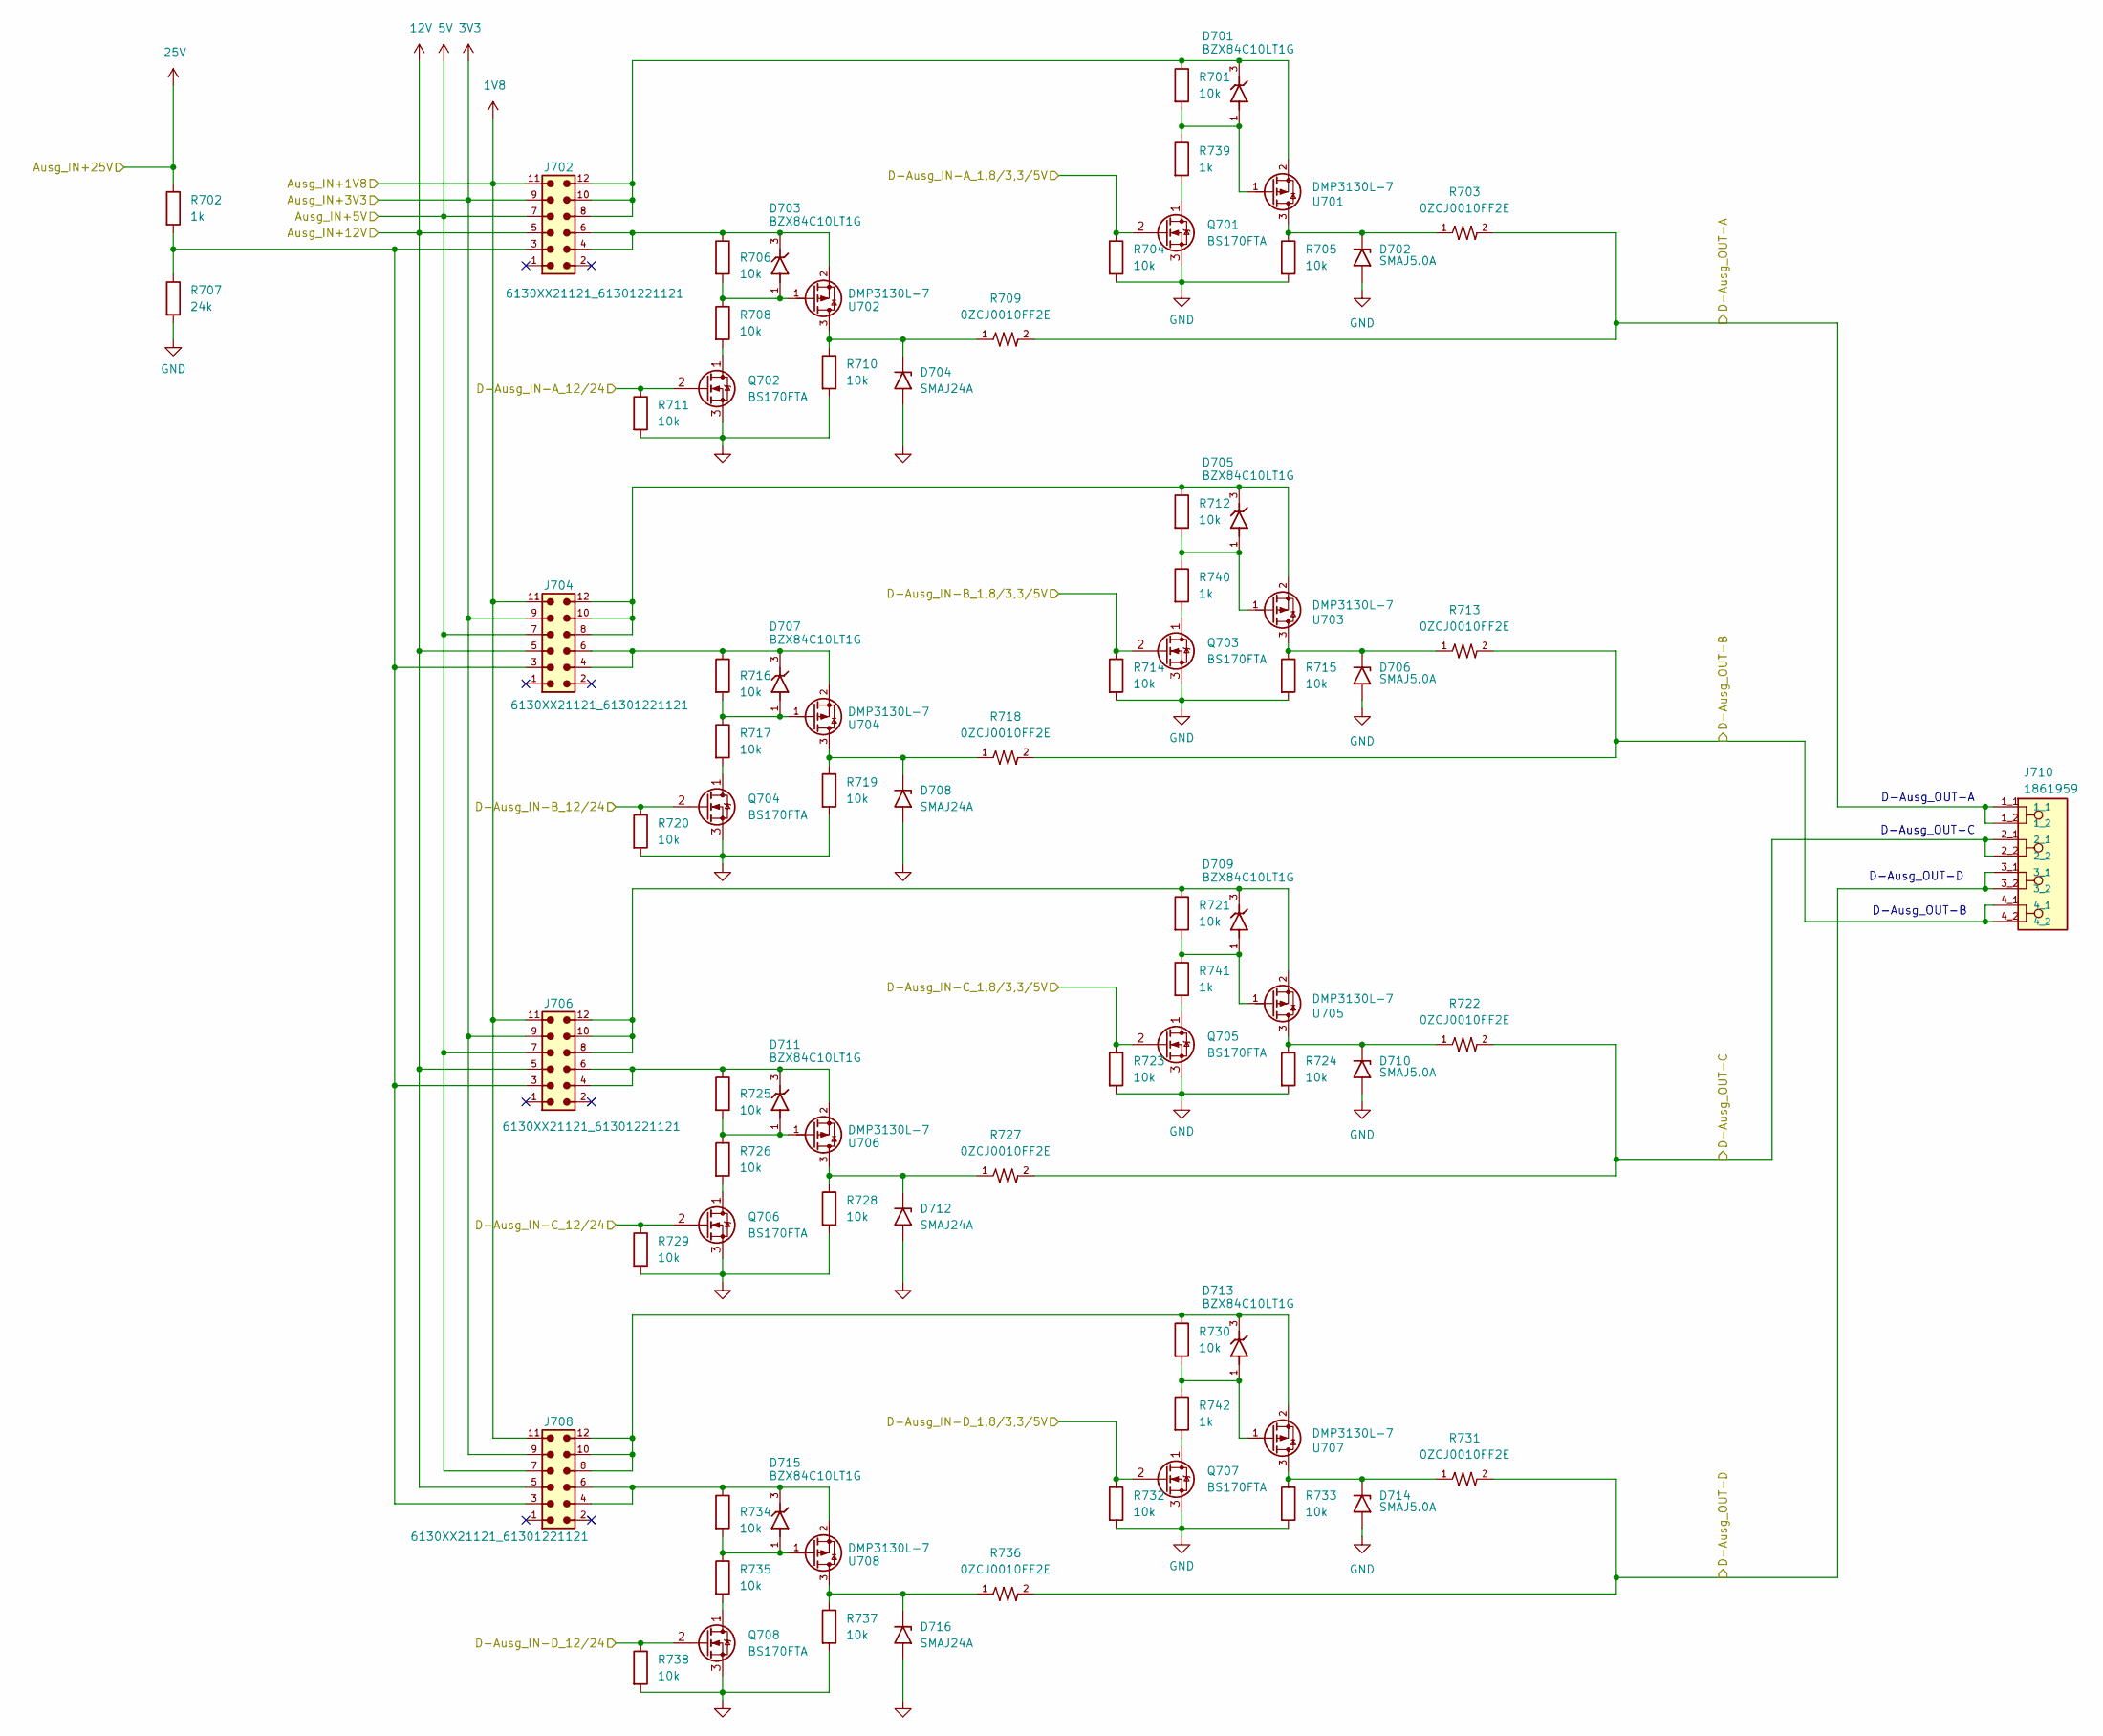
[picture p65: schematic Digitale-Ausgaenge.kicad_sch]

Parts:
D701, D703, D705, D707, D709, D711, D713, D715: BZX84C10LT1G; SOT95P240X111-3N; PARTREV 23; JLCPCB PN C82476
D702, D706, D710, D714: SMAJ5.0A; D_SMA; Manufacturer_Part_Number SMAJ5.0A; JLCPCB PN C10758
D704, D708, D712, D716: SMAJ24A; D_SMA; Manufacturer_Part_Number SMAJ24A; JLCPCB PN C10769
J702, J704, J706, J708: 6130XX21121_61301221121; 61301221121; Manufacturer_Part_Number 61301221121; JLCPCB PN C6699258
J710: 1861959; PHOENIX_1861959; Manufacturer_Part_Number 1861959; JLCPCB PN C6656102
Q701, Q702, Q703, Q704, Q705, Q706, Q707, Q708: BS170FTA; SOT-23; Manufacturer_Part_Number BS170FTA; JLCPCB PN C5236685
R701, R704, R705, R706, R708, R710, R711, R712, R714, R715, R716, R717, R719, R720, R721, R723, R724, R725, R726, R728, R729, R730, R732, R733, R734, R735, R737, R738: 10k; R_0805_2012Metric; JLCPCB PN C149881
R702: 1k; R_1206_3216Metric; JLCPCB PN C4410
R703, R709, R713, R718, R722, R727, R731, R736: 0ZCJ0010FF2E; RESC3216X125N; Manufacturer_Part_Number 0ZCJ0010FF2E; JLCPCB PN C194142
R707: 24k; R_1206_3216Metric; JLCPCB PN C17960
R739, R740, R741, R742: 1k; R_0805_2012Metric; JLCPCB PN C17513
U701, U702, U703, U704, U705, U706, U707, U708: DMP3130L-7; SOT103P240X110-3N; MPN DMP3068L-7; JLCPCB PN C155233

Connections:
1V8: J702.11, J704.11, J706.11, J708.11
3V3: J702.9, J704.9, J706.9, J708.9
5V: J702.7, J704.7, J706.7, J708.7
12V: J702.5, J704.5, J706.5, J708.5
25V: R702.1
D-Ausg_IN-A_1,8/3,3/5V: Q701.2 (G), R704.1
D-Ausg_IN-A_12/24: Q702.2 (G), R711.1
D-Ausg_IN-B_1,8/3,3/5V: Q703.2 (G), R714.1
D-Ausg_IN-B_12/24: Q704.2 (G), R720.1
D-Ausg_IN-C_1,8/3,3/5V: Q705.2 (G), R723.1
D-Ausg_IN-C_12/24: Q706.2 (G), R729.1
D-Ausg_IN-D_1,8/3,3/5V: Q707.2 (G), R732.1
D-Ausg_IN-D_12/24: Q708.2 (G), R738.1
D-Ausg_OUT-A: J710.1_1, J710.1_2, R703.2, R709.2
D-Ausg_OUT-B: J710.4_1, J710.4_2, R713.2, R718.2
D-Ausg_OUT-C: J710.2_1, J710.2_2, R722.2, R727.2
D-Ausg_OUT-D: J710.3_1, J710.3_2, R731.2, R736.2
GND: D702.2 (A2), D704.2 (A2), D706.2 (A2), D708.2 (A2), D710.2 (A2), D712.2 (A2), D714.2 (A2), D716.2 (A2), Q701.3 (S), Q702.3 (S), Q703.3 (S), Q704.3 (S), Q705.3 (S), Q706.3 (S), Q707.3 (S), Q708.3 (S), R704.2, R705.2, R707.2, R710.2, R711.2, R714.2, R715.2, R719.2, R720.2, R723.2, R724.2, R728.2, R729.2, R732.2, R733.2, R737.2, R738.2
unnamed: D701.1, R701.2, R739.1, U701.1
unnamed: D701.3, J702.8, J702.10, J702.12, R701.1, U701.2
unnamed: D702.1 (A1), R703.1, R705.1, U701.3
unnamed: D703.1, R706.2, R708.1, U702.1
unnamed: D703.3, J702.4, J702.6, R706.1, U702.2
unnamed: D704.1 (A1), R709.1, R710.1, U702.3
unnamed: D705.1, R712.2, R740.1, U703.1
unnamed: D705.3, J704.8, J704.10, J704.12, R712.1, U703.2
unnamed: D706.1 (A1), R713.1, R715.1, U703.3
unnamed: D707.1, R716.2, R717.1, U704.1
unnamed: D707.3, J704.4, J704.6, R716.1, U704.2
unnamed: D708.1 (A1), R718.1, R719.1, U704.3
unnamed: D709.1, R721.2, R741.1, U705.1
unnamed: D709.3, J706.8, J706.10, J706.12, R721.1, U705.2
unnamed: D710.1 (A1), R722.1, R724.1, U705.3
unnamed: D711.1, R725.2, R726.1, U706.1
unnamed: D711.3, J706.4, J706.6, R725.1, U706.2
unnamed: D712.1 (A1), R727.1, R728.1, U706.3
unnamed: D713.1, R730.2, R742.1, U707.1
unnamed: D713.3, J708.8, J708.10, J708.12, R730.1, U707.2
unnamed: D714.1 (A1), R731.1, R733.1, U707.3
unnamed: D715.1, R734.2, R735.1, U708.1
unnamed: D715.3, J708.4, J708.6, R734.1, U708.2
unnamed: D716.1 (A1), R736.1, R737.1, U708.3
unnamed: J702.3, J704.3, J706.3, J708.3, R702.2, R707.1
unnamed: Q701.1 (D), R739.2
unnamed: Q702.1 (D), R708.2
unnamed: Q703.1 (D), R740.2
unnamed: Q704.1 (D), R717.2
unnamed: Q705.1 (D), R741.2
unnamed: Q706.1 (D), R726.2
unnamed: Q707.1 (D), R742.2
unnamed: Q708.1 (D), R735.2

Notes on the sheet:
D-Ausg_OUT-C
D-Ausg_OUT-D
D-Ausg_OUT-B
D-Ausg_OUT-A
