CodeByMika/technikerarbeit2026-hardwarepruefadapter/Hardware/hardware-pruefadapter/ESP32.kicad_sch

## KiCad design Hardware/hardware-pruefadapter/ESP32.kicad_sch (2026-06-18)

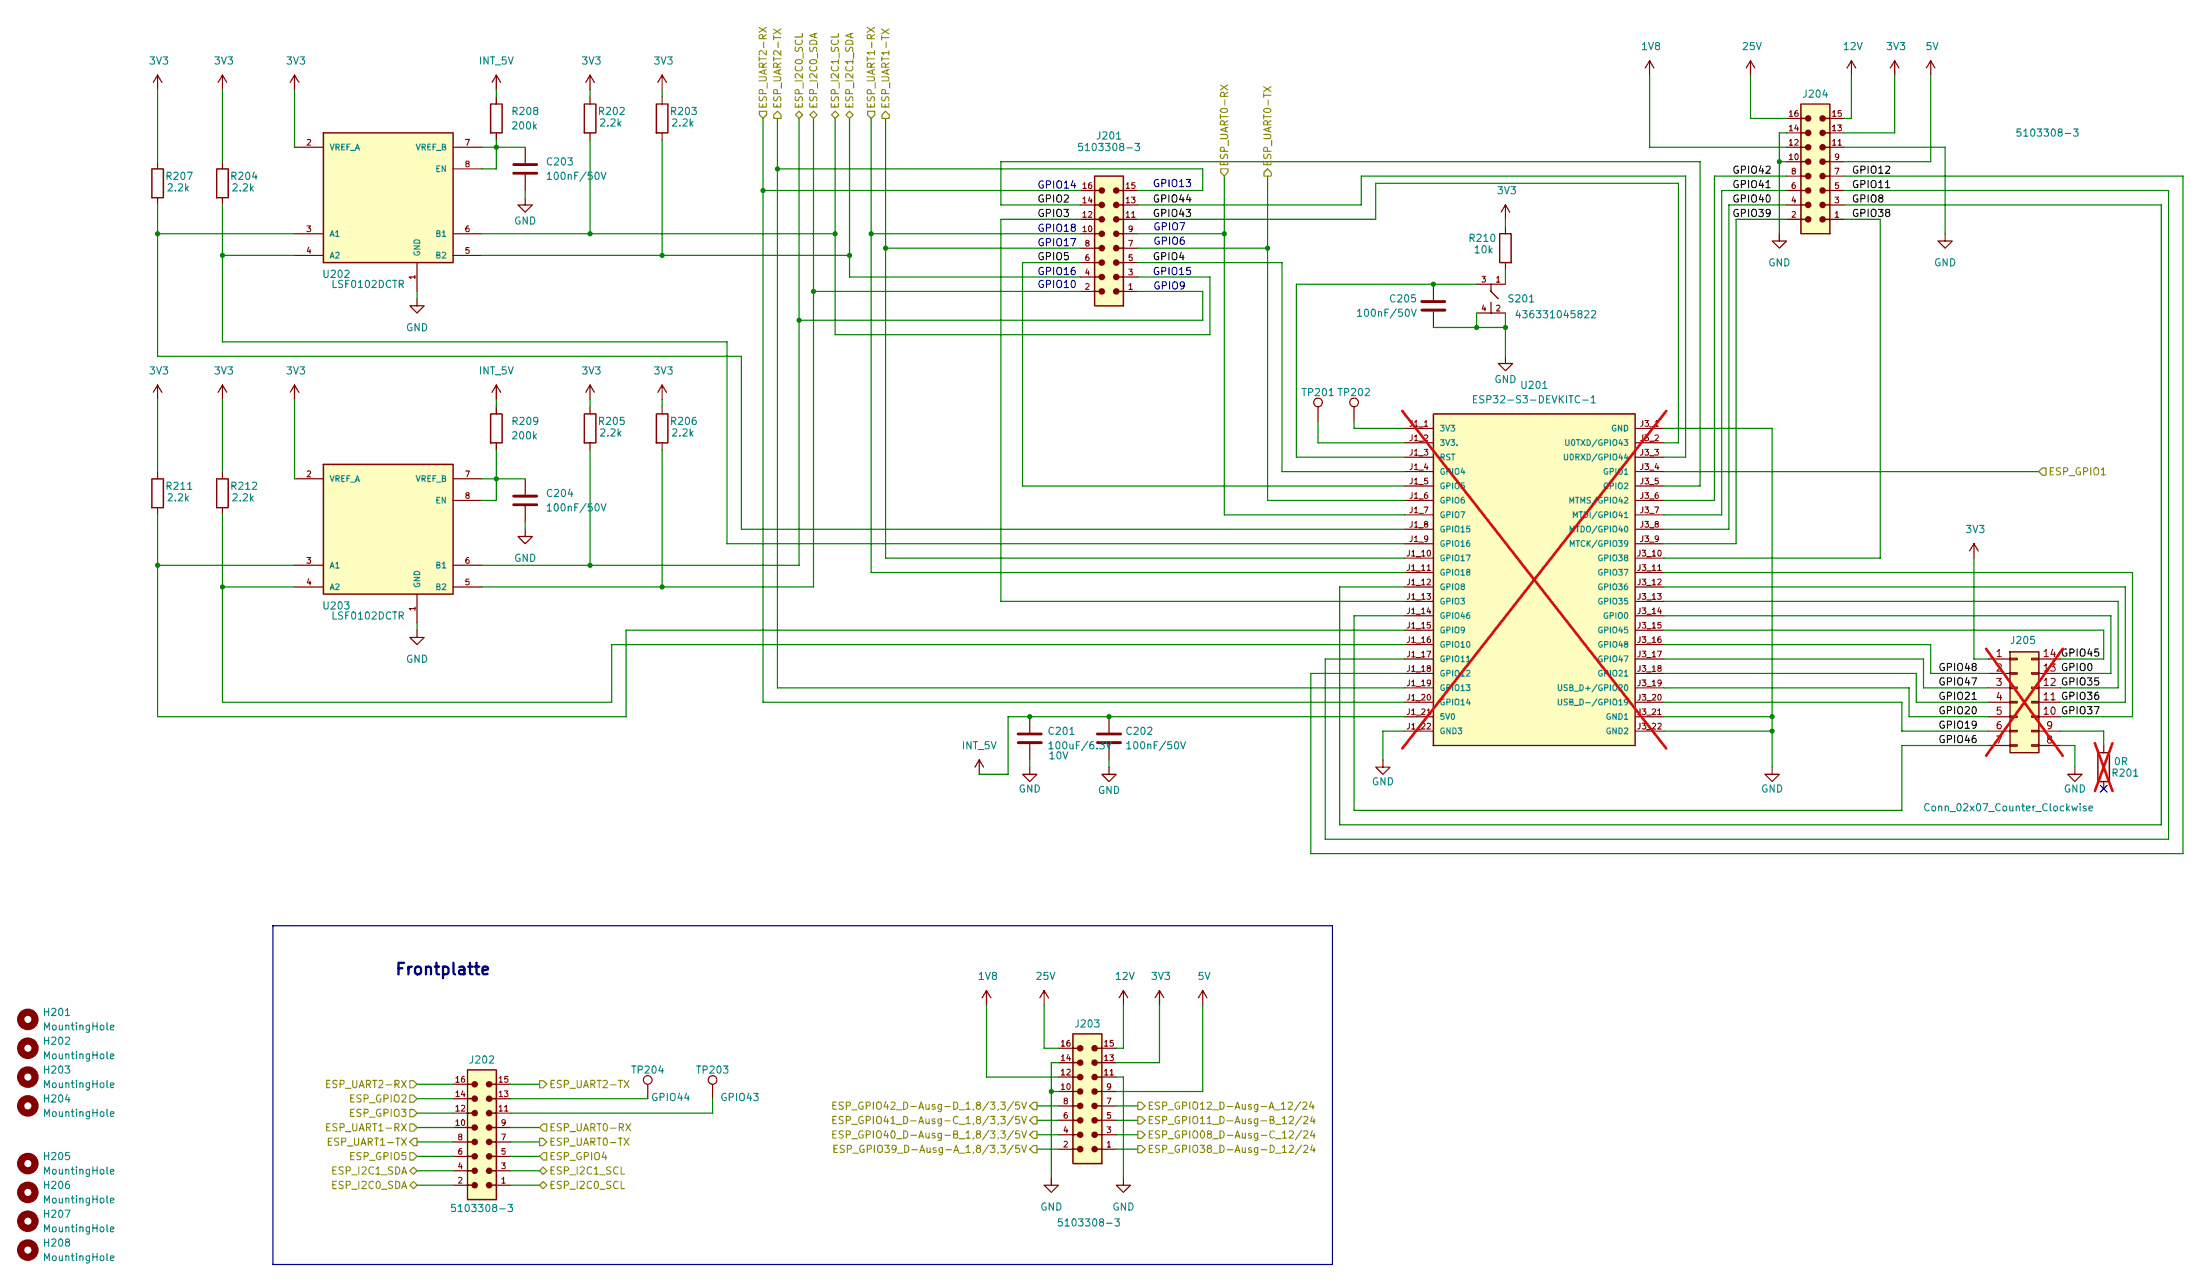
[picture p66: schematic ESP32.kicad_sch]

Parts:
C201: 100uF/6.3V; C_1206_3216Metric; JLCPCB PN C15008
C202: 100nF/50V; C_1206_3216Metric; JLCPCB PN C24497
C203, C204, C205: 100nF/50V; C_0805_2012Metric; JLCPCB PN C1711
H201, H202, H203, H204, H205, H206, H207, H208: MountingHole; MountingHole_3.2mm_M3
J201, J202, J203, J204: 5103308-3; 61201621621; Manufacturer_Part_Number 5103308-3; JLCPCB PN C305956
J205: Conn_02x07_Counter_Clockwise; 61301421121; not fitted
R201: 0R; R_0805_2012Metric; JLCPCB PN C17477; not fitted
R202, R203, R204, R205, R206, R207, R211, R212: 2.2k; R_0805_2012Metric; JLCPCB PN C17520
R208, R209: 200k; R_0805_2012Metric; JLCPCB PN C17539
R210: 10k; R_0805_2012Metric; JLCPCB PN C149881
S201: 436331045822; 4363X10458XX; Manufacturer_Part_Number 436331045822; JLCPCB PN C6089591
TP201, TP202: TestPoint_Pad_D1.5mm
TP203: GPIO43; TestPoint_Pad_D1.5mm
TP204: GPIO44; TestPoint_Pad_D1.5mm
U201: ESP32-S3-DEVKITC-1; ESP32-S3-DEVKITC-1-N8R8; Manufacturer_Part_Number ESP32-S3-DEVKITC-1; not fitted
U202, U203: LSF0102DCTR; SOP65P400X130-8N; PARTREV J; JLCPCB PN C132024

Connections:
1V8: J203.12, J204.12
3V3: J203.13, J204.13, J205.1, R202.1, R203.1, R204.1, R205.1, R206.1, R207.1, R210.1, R211.1, R212.1, U202.2 (VREF_A), U203.2 (VREF_A)
5V: J203.9, J204.9
12V: J203.15, J204.15
25V: J203.16, J204.16
ESP_GPIO1: U201.J3_4 (GPIO1)
ESP_GPIO2: J202.14
ESP_GPIO3: J202.12
ESP_GPIO4: J202.5
ESP_GPIO5: J202.6
ESP_GPIO08_D-Ausg-C_12/24: J203.3
ESP_GPIO11_D-Ausg-B_12/24: J203.5
ESP_GPIO12_D-Ausg-A_12/24: J203.7
ESP_GPIO38_D-Ausg-D_12/24: J203.1
ESP_GPIO39_D-Ausg-A_1,8/3,3/5V: J203.2
ESP_GPIO40_D-Ausg-B_1,8/3,3/5V: J203.4
ESP_GPIO41_D-Ausg-C_1,8/3,3/5V: J203.6
ESP_GPIO42_D-Ausg-D_1,8/3,3/5V: J203.8
ESP_I2C0_SCL: J201.1, J202.1, R205.2, U203.6 (B1)
ESP_I2C0_SDA: J201.2, J202.2, R206.2, U203.5 (B2)
ESP_I2C1_SCL: J201.3, J202.3, R202.2, U202.6 (B1)
ESP_I2C1_SDA: J201.4, J202.4, R203.2, U202.5 (B2)
ESP_UART0-RX: J201.9, J202.9, U201.J1_7 (GPIO7)
ESP_UART0-TX: J201.7, J202.7, U201.J1_6 (GPIO6)
ESP_UART1-RX: J201.10, J202.10, U201.J1_11 (GPIO18)
ESP_UART1-TX: J201.8, J202.8, U201.J1_10 (GPIO17)
ESP_UART2-RX: J201.16, J202.16, U201.J1_20 (GPIO14)
ESP_UART2-TX: J201.15, J202.15, U201.J1_19 (GPIO13)
GND: C201.2, C202.2, C203.2, C204.2, C205.2, J203.10, J203.11, J203.14, J204.10, J204.11, J204.14, J205.8, S201.2, S201.4, U201.J1_22 (GND3), U201.J3_1 (GND), U201.J3_21 (GND1), U201.J3_22 (GND2), U202.1 (GND), U203.1 (GND)
GPIO0: J205.13, U201.J3_14 (GPIO0)
GPIO2: J201.14, U201.J3_5 (GPIO2)
GPIO3: J201.12, U201.J1_13 (GPIO3)
GPIO4: J201.5, U201.J1_4 (GPIO4)
GPIO5: J201.6, U201.J1_5 (GPIO5)
GPIO8: J204.3, U201.J1_12 (GPIO8)
GPIO11: J204.5, U201.J1_17 (GPIO11)
GPIO12: J204.7, U201.J1_18 (GPIO12)
GPIO19: J205.6, U201.J3_20 (USB_D-/GPIO19)
GPIO20: J205.5, U201.J3_19 (USB_D+/GPIO20)
GPIO21: J205.4, U201.J3_18 (GPIO21)
GPIO35: J205.12, U201.J3_13 (GPIO35)
GPIO36: J205.11, U201.J3_12 (GPIO36)
GPIO37: J205.10, U201.J3_11 (GPIO37)
GPIO38: J204.1, U201.J3_10 (GPIO38)
GPIO39: J204.2, U201.J3_9 (MTCK/GPIO39)
GPIO40: J204.4, U201.J3_8 (MTDO/GPIO40)
GPIO41: J204.6, U201.J3_7 (MTDI/GPIO41)
GPIO42: J204.8, U201.J3_6 (MTMS/GPIO42)
GPIO43: J201.11, U201.J3_2 (U0TXD/GPIO43)
GPIO44: J201.13, U201.J3_3 (U0RXD/GPIO44)
GPIO45: J205.14, U201.J3_15 (GPIO45)
GPIO46: J205.7, U201.J1_14 (GPIO46)
GPIO47: J205.3, U201.J3_17 (GPIO47)
GPIO48: J205.2, U201.J3_16 (GPIO48)
INT_5V: C201.1, C202.1, R208.1, R209.1, U201.J1_21 (5V0)
unnamed: C203.1, R208.2, U202.7 (VREF_B), U202.8 (EN)
unnamed: C204.1, R209.2, U203.7 (VREF_B), U203.8 (EN)
unnamed: C205.1, S201.3, U201.J1_3 (RST)
unnamed: J202.11, TP203.1
unnamed: J202.13, TP204.1
unnamed: J205.9, R201.1
unnamed: R204.2, U201.J1_9 (GPIO16), U202.4 (A2)
unnamed: R207.2, U201.J1_8 (GPIO15), U202.3 (A1)
unnamed: R210.2, S201.1
unnamed: R211.2, U201.J1_15 (GPIO9), U203.3 (A1)
unnamed: R212.2, U201.J1_16 (GPIO10), U203.4 (A2)
unnamed: TP201.1, U201.J1_2 (3V3.)
unnamed: TP202.1, U201.J1_1 (3V3)

Notes on the sheet:
Frontplatte
GPIO7
GPIO18
GPIO13
GPIO14
GPIO6
GPIO17
GPIO15
GPIO16
GPIO9
GPIO10
