CodeByMika/technikerarbeit2026-hardwarepruefadapter/Hardware/hardware-pruefadapter/LED-Treiber.kicad_sch

## KiCad design Hardware/hardware-pruefadapter/LED-Treiber.kicad_sch (2026-06-18)

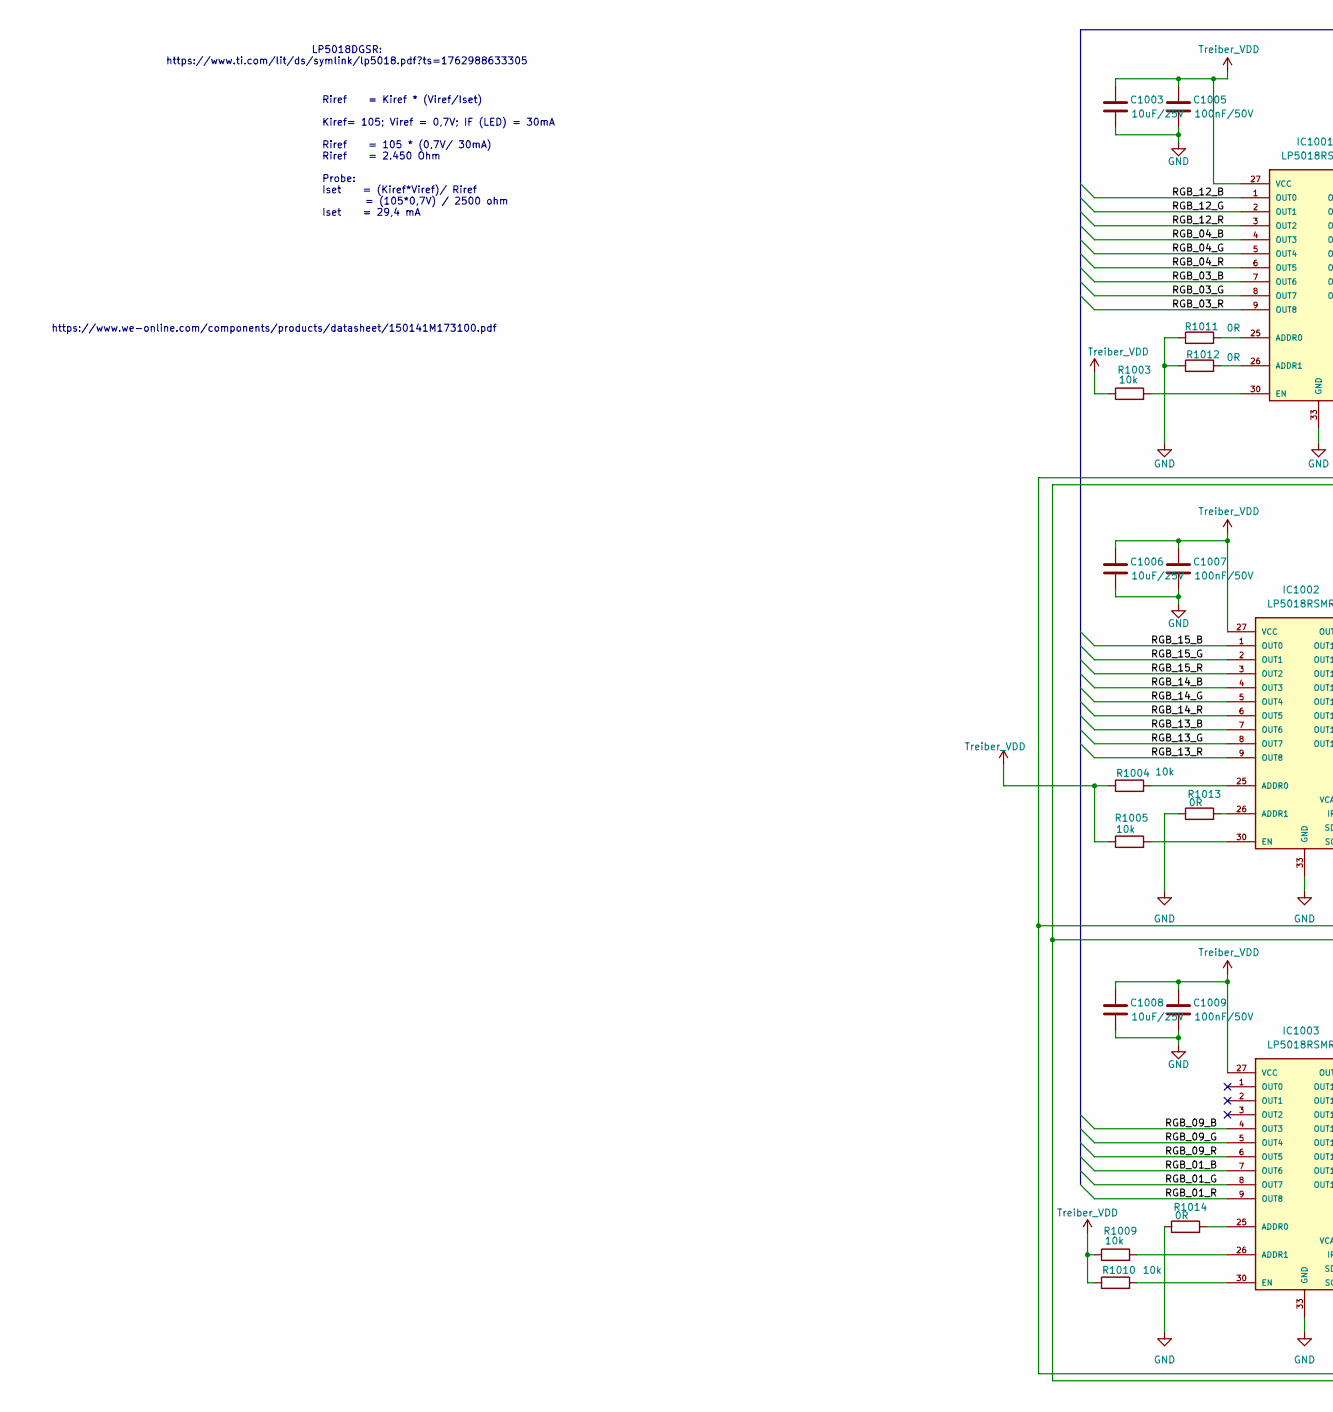
[picture p67: schematic LED-Treiber.kicad_sch, part in row 1, column 1]

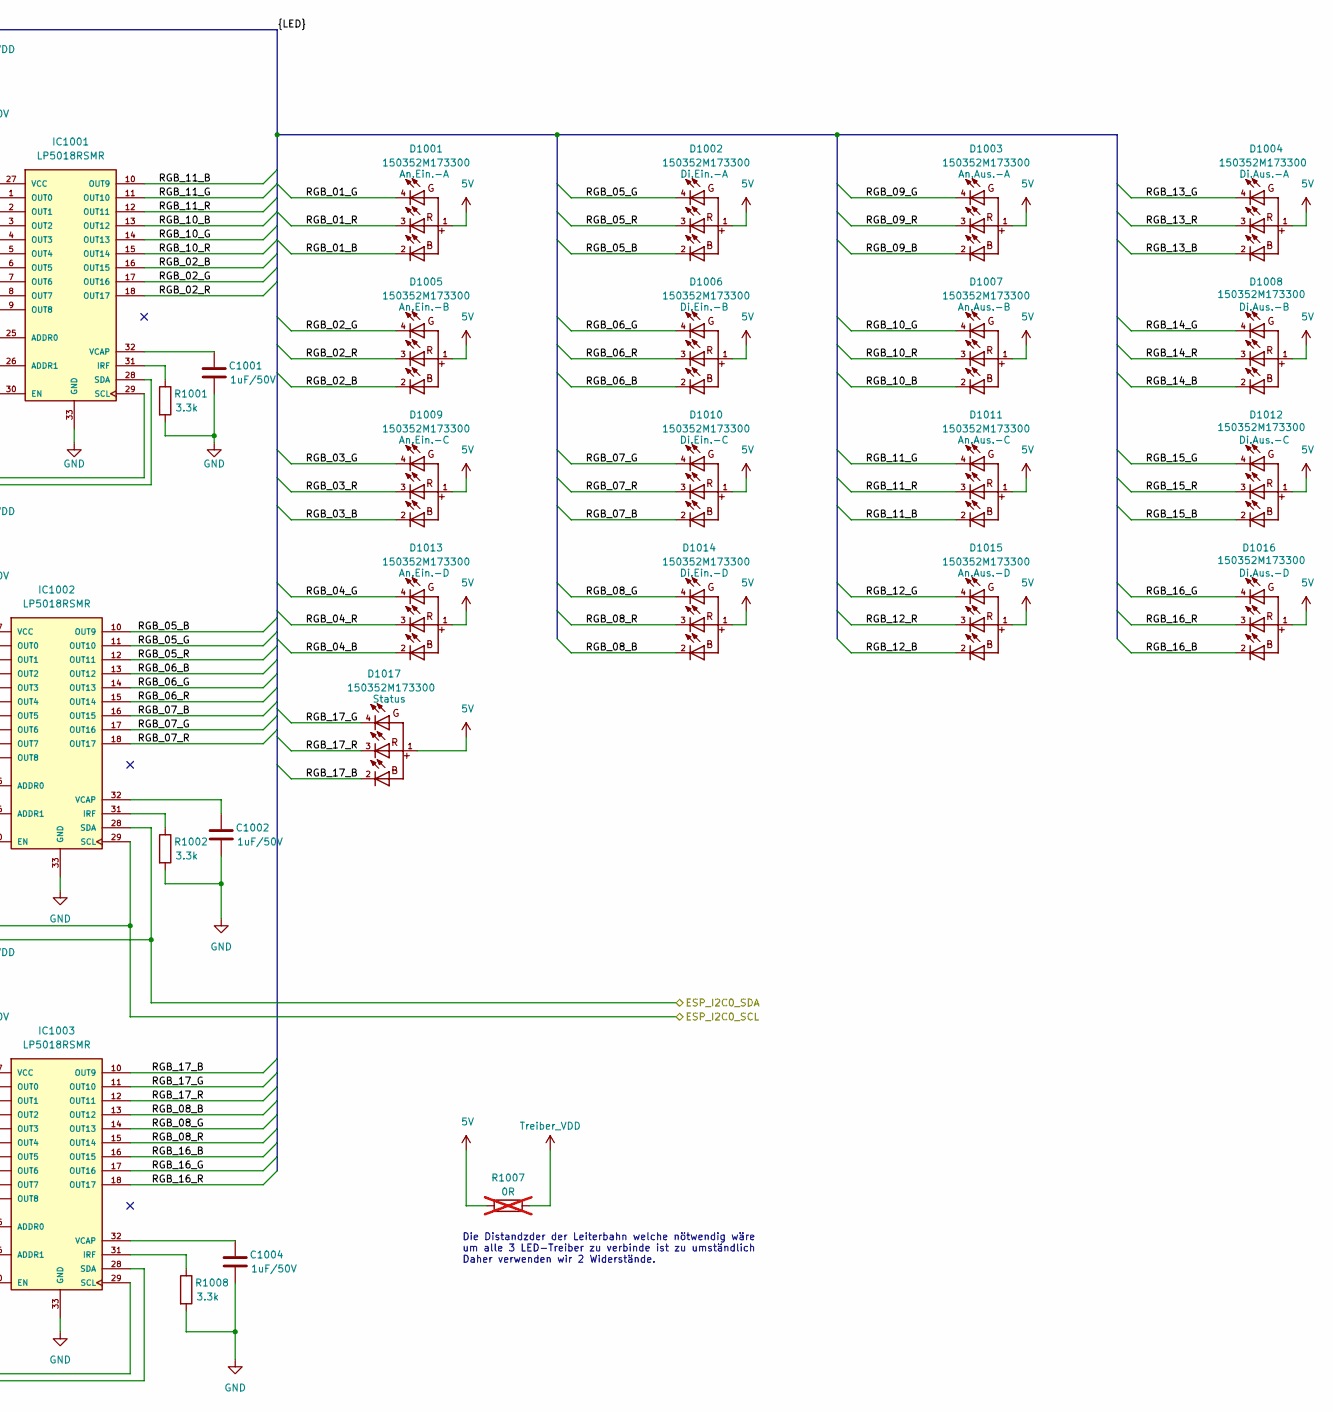
[picture p68: schematic LED-Treiber.kicad_sch, part in row 1, column 2]

Parts:
C1001, C1002, C1004: 1uF/50V; C_0805_2012Metric; JLCPCB PN C28323
C1003, C1006, C1008: 10uF/25V; C_0805_2012Metric; JLCPCB PN C15850
C1005, C1007, C1009: 100nF/50V; C_0805_2012Metric; JLCPCB PN C1711
D1001, D1002, D1003, D1004, D1005, D1006, D1007, D1008, D1009, D1010, D1011, D1012, D1013, D1014, D1015, D1016, D1017: 150352M173300; WL-SFTW_3528_PLCC4; Manufacturer_Part_Number 150352M173300; JLCPCB PN C6785090
IC1001, IC1002, IC1003: LP5018RSMR; VQFN-32_LP5018RSMR; PARTREV 4219108/B 08/2019; JLCPCB PN C2653373
R1001, R1002, R1008: 3.3k; R_0805_2012Metric; JLCPCB PN C26010
R1003, R1004, R1005, R1009, R1010: 10k; R_0805_2012Metric; JLCPCB PN C149881
R1007: 0R; R_1206_3216Metric; JLCPCB PN C17888; not fitted
R1011, R1012, R1013, R1014: 0R; R_0805_2012Metric; JLCPCB PN C17477

Connections:
5V: D1001.1, D1002.1, D1003.1, D1004.1, D1005.1, D1006.1, D1007.1, D1008.1, D1009.1, D1010.1, D1011.1, D1012.1, D1013.1, D1014.1, D1015.1, D1016.1, D1017.1, R1007.1
ESP_I2C0_SCL: IC1001.29 (SCL), IC1002.29 (SCL), IC1003.29 (SCL)
ESP_I2C0_SDA: IC1001.28 (SDA), IC1002.28 (SDA), IC1003.28 (SDA)
GND: C1001.2, C1002.2, C1003.2, C1004.2, C1005.2, C1006.2, C1007.2, C1008.2, C1009.2, IC1001.33 (GND), IC1001.34 (GND), IC1001.35 (GND), IC1001.36 (GND), IC1001.37 (GND), IC1001.38 (GND), IC1002.33 (GND), IC1002.34 (GND), IC1002.35 (GND), IC1002.36 (GND), IC1002.37 (GND), IC1002.38 (GND), IC1003.33 (GND), IC1003.34 (GND), IC1003.35 (GND), IC1003.36 (GND), IC1003.37 (GND), IC1003.38 (GND), R1001.2, R1002.2, R1008.2, R1011.1, R1012.1, R1013.1, R1014.1
unnamed: C1001.1, IC1001.32 (VCAP)
unnamed: C1002.1, IC1002.32 (VCAP)
unnamed: C1004.1, IC1003.32 (VCAP)
unnamed: IC1001.19 (NC_19), IC1001.20 (NC_20), IC1001.21 (NC_21), IC1001.22 (NC_22), IC1001.23 (NC_23), IC1001.24 (NC_24)
unnamed: IC1001.25 (ADDR0), R1011.2
unnamed: IC1001.26 (ADDR1), R1012.2
unnamed: IC1001.30 (EN), R1003.2
unnamed: IC1001.31 (IRF), R1001.1
unnamed: IC1002.19 (NC_19), IC1002.20 (NC_20), IC1002.21 (NC_21), IC1002.22 (NC_22), IC1002.23 (NC_23), IC1002.24 (NC_24)
unnamed: IC1002.25 (ADDR0), R1004.2
unnamed: IC1002.26 (ADDR1), R1013.2
unnamed: IC1002.30 (EN), R1005.2
unnamed: IC1002.31 (IRF), R1002.1
unnamed: IC1003.19 (NC_19), IC1003.20 (NC_20), IC1003.21 (NC_21), IC1003.22 (NC_22), IC1003.23 (NC_23), IC1003.24 (NC_24)
unnamed: IC1003.25 (ADDR0), R1014.2
unnamed: IC1003.26 (ADDR1), R1009.2
unnamed: IC1003.30 (EN), R1010.2
unnamed: IC1003.31 (IRF), R1008.1
RGB_01_B: D1001.2, IC1003.7 (OUT6)
RGB_01_G: D1001.4, IC1003.8 (OUT7)
RGB_01_R: D1001.3, IC1003.9 (OUT8)
RGB_02_B: D1005.2, IC1001.16 (OUT15)
RGB_02_G: D1005.4, IC1001.17 (OUT16)
RGB_02_R: D1005.3, IC1001.18 (OUT17)
RGB_03_B: D1009.2, IC1001.7 (OUT6)
RGB_03_G: D1009.4, IC1001.8 (OUT7)
RGB_03_R: D1009.3, IC1001.9 (OUT8)
RGB_04_B: D1013.2, IC1001.4 (OUT3)
RGB_04_G: D1013.4, IC1001.5 (OUT4)
RGB_04_R: D1013.3, IC1001.6 (OUT5)
RGB_05_B: D1002.2, IC1002.10 (OUT9)
RGB_05_G: D1002.4, IC1002.11 (OUT10)
RGB_05_R: D1002.3, IC1002.12 (OUT11)
RGB_06_B: D1006.2, IC1002.13 (OUT12)
RGB_06_G: D1006.4, IC1002.14 (OUT13)
RGB_06_R: D1006.3, IC1002.15 (OUT14)
RGB_07_B: D1010.2, IC1002.16 (OUT15)
RGB_07_G: D1010.4, IC1002.17 (OUT16)
RGB_07_R: D1010.3, IC1002.18 (OUT17)
RGB_08_B: D1014.2, IC1003.13 (OUT12)
RGB_08_G: D1014.4, IC1003.14 (OUT13)
RGB_08_R: D1014.3, IC1003.15 (OUT14)
RGB_09_B: D1003.2, IC1003.4 (OUT3)
RGB_09_G: D1003.4, IC1003.5 (OUT4)
RGB_09_R: D1003.3, IC1003.6 (OUT5)
RGB_10_B: D1007.2, IC1001.13 (OUT12)
RGB_10_G: D1007.4, IC1001.14 (OUT13)
RGB_10_R: D1007.3, IC1001.15 (OUT14)
RGB_11_B: D1011.2, IC1001.10 (OUT9)
RGB_11_G: D1011.4, IC1001.11 (OUT10)
RGB_11_R: D1011.3, IC1001.12 (OUT11)
RGB_12_B: D1015.2, IC1001.1 (OUT0)
RGB_12_G: D1015.4, IC1001.2 (OUT1)
RGB_12_R: D1015.3, IC1001.3 (OUT2)
RGB_13_B: D1004.2, IC1002.7 (OUT6)
RGB_13_G: D1004.4, IC1002.8 (OUT7)
RGB_13_R: D1004.3, IC1002.9 (OUT8)
RGB_14_B: D1008.2, IC1002.4 (OUT3)
RGB_14_G: D1008.4, IC1002.5 (OUT4)
RGB_14_R: D1008.3, IC1002.6 (OUT5)
RGB_15_B: D1012.2, IC1002.1 (OUT0)
RGB_15_G: D1012.4, IC1002.2 (OUT1)
RGB_15_R: D1012.3, IC1002.3 (OUT2)
RGB_16_B: D1016.2, IC1003.16 (OUT15)
RGB_16_G: D1016.4, IC1003.17 (OUT16)
RGB_16_R: D1016.3, IC1003.18 (OUT17)
RGB_17_B: D1017.2, IC1003.10 (OUT9)
RGB_17_G: D1017.4, IC1003.11 (OUT10)
RGB_17_R: D1017.3, IC1003.12 (OUT11)
Treiber_VDD: C1003.1, C1005.1, C1006.1, C1007.1, C1008.1, C1009.1, IC1001.27 (VCC), IC1002.27 (VCC), IC1003.27 (VCC), R1003.1, R1004.1, R1005.1, R1007.2, R1009.1, R1010.1

Notes on the sheet:
LP5018DGSR: https://www.ti.com/lit/ds/symlink/lp5018.pdf?ts=1762988633305
Riref = Kiref * (Viref/Iset) Kiref= 105; Viref = 0,7V; IF (LED) = 30mA Riref = 105 * (0,7V/ 30mA) Riref = 2.450 Ohm Probe: Iset = (Kiref*Viref)/ Riref = (105*0,7V) / 2500 ohm Iset = 29,4 mA
Die Distandzder der Leiterbahn welche nötwendig wäre um alle 3 LED-Treiber zu verbinde ist zu umständlich Daher verwenden wir 2 Widerstände.
https://www.we-online.com/components/products/datasheet/150141M173100.pdf
