CodeByMika/technikerarbeit2026-hardwarepruefadapter/Hardware/hardware-pruefadapter/PowerSupplyUnit.kicad_sch

## KiCad design Hardware/hardware-pruefadapter/PowerSupplyUnit.kicad_sch (2026-06-18)

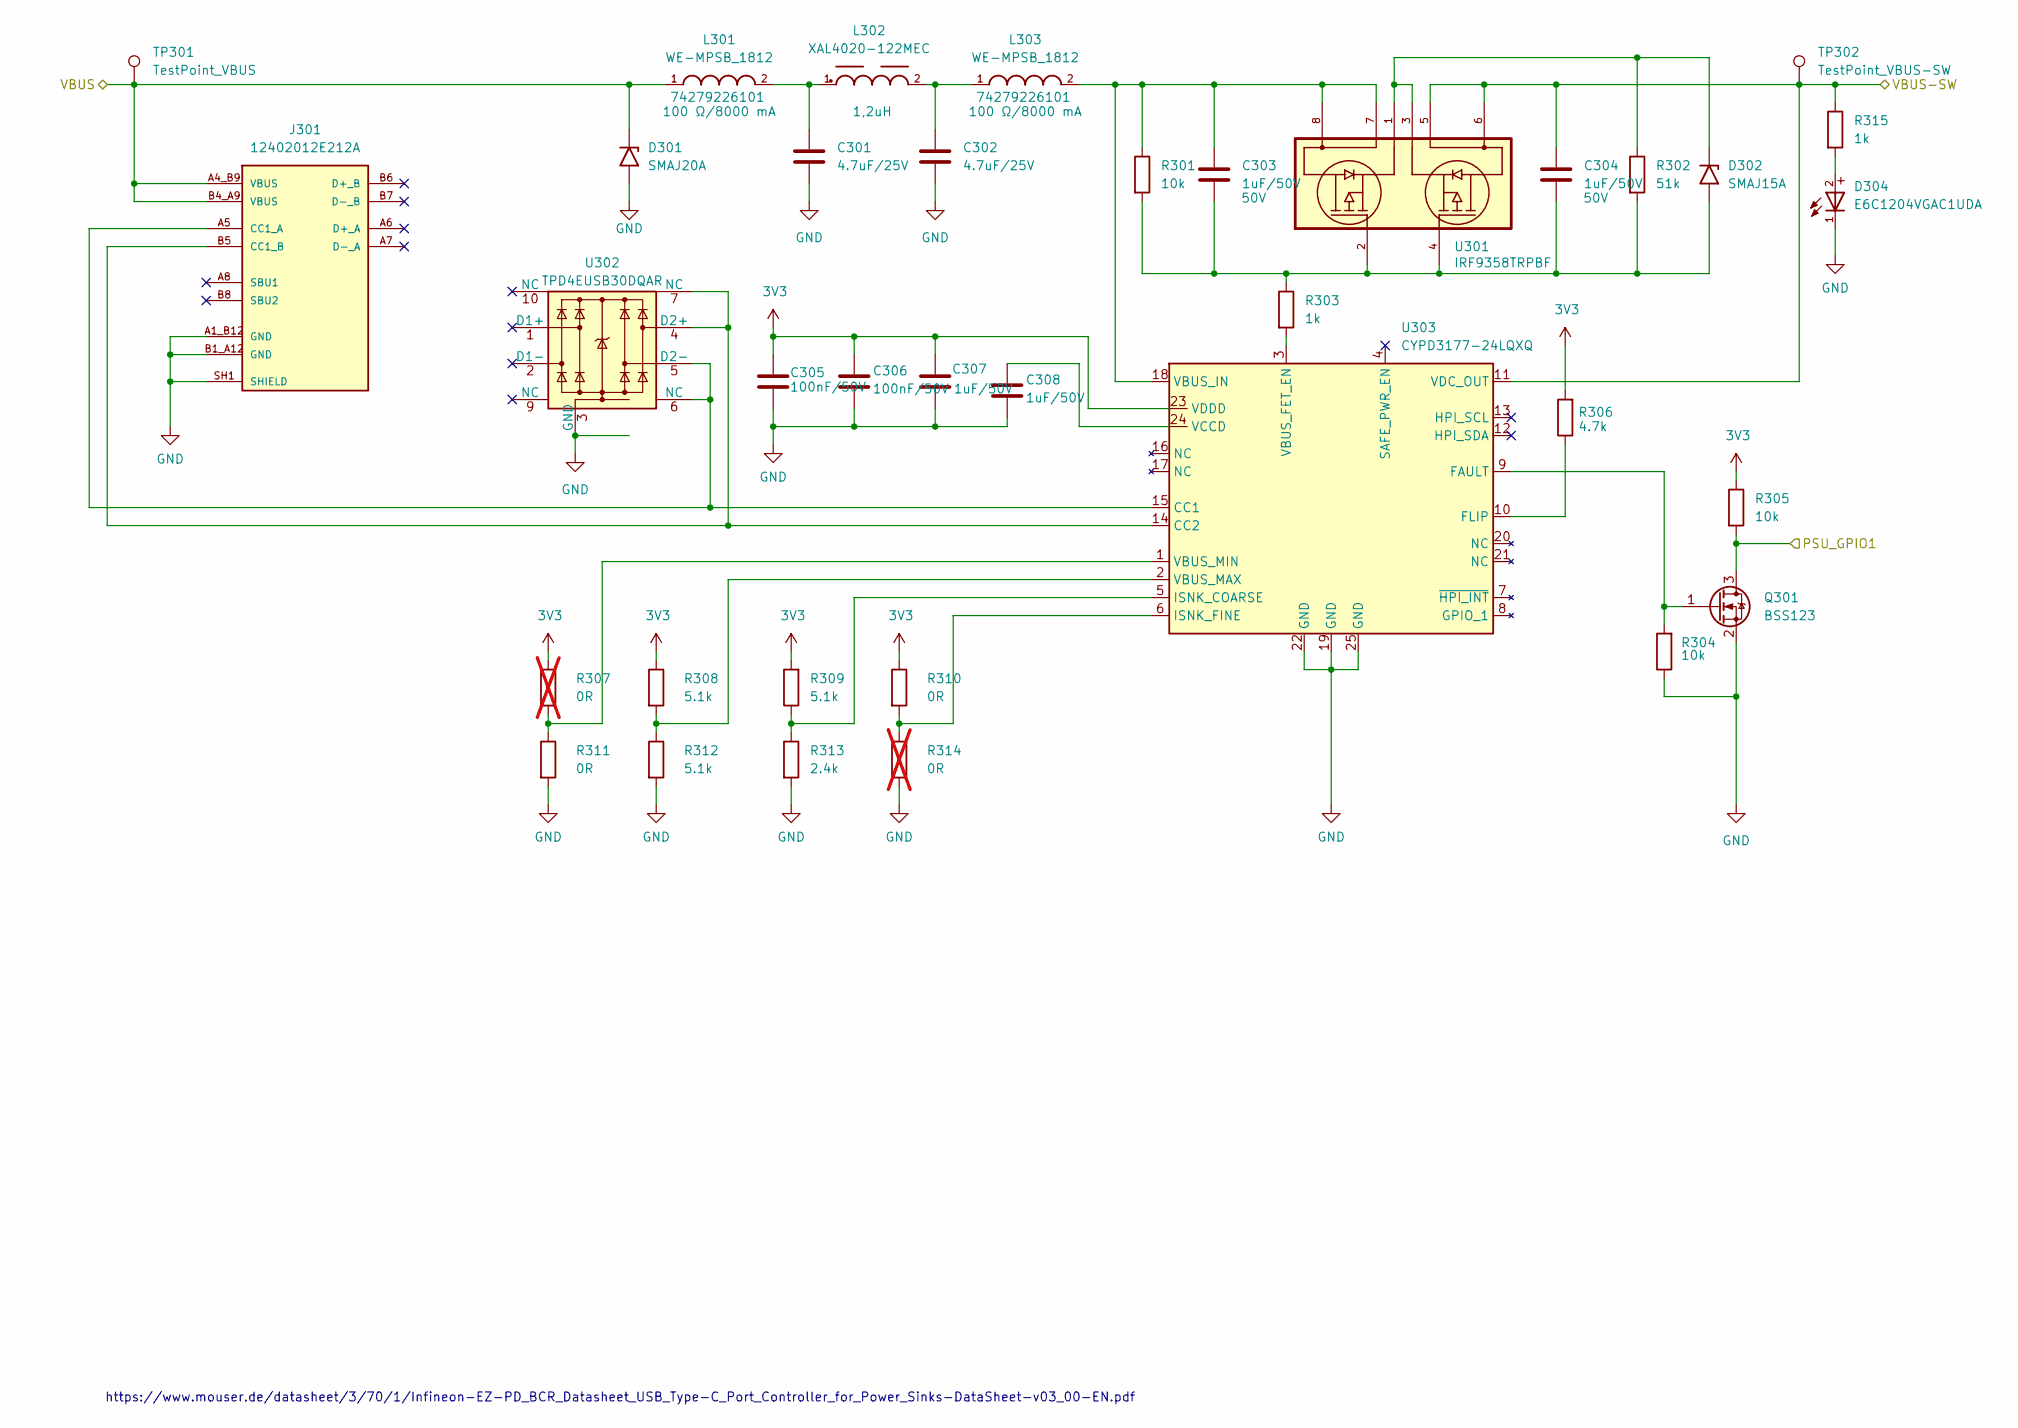
[picture p69: schematic PowerSupplyUnit.kicad_sch]

Parts:
C301, C302: 4.7uF/25V; C_1206_3216Metric; JLCPCB PN C1872
C303: 1uF/50V; C_0805_2012Metric; JLCPCB PN C28323
C304: 1uF/50V; C_1206_3216Metric; JLCPCB PN C1848
C305, C306: 100nF/50V; C_0603_1608Metric; JLCPCB PN C14663
C307, C308: 1uF/50V; C_0603_1608Metric; JLCPCB PN C15849
D301: SMAJ20A; D_SMA; Manufacturer_Part_Number SMAJ20A; JLCPCB PN C10763
D302: SMAJ15A; D_SMA; Manufacturer_Part_Number SMAJ15A; JLCPCB PN C23424
D304: E6C1204VGAC1UDA; WL-SMSW_1204_A; Manufacturer_Part_Number E6C1204VGAC1UDA; JLCPCB PN C375482
J301: 12402012E212A; AMPHENOL_12402012E212A; PARTREV 4; JLCPCB PN C5150972
L301, L303: WE-MPSB_1812; Manufacturer_Part_Number 74279226101; JLCPCB PN C5155961
L302: XAL4020-122MEC; WE-MAPI_4020; Manufacturer_Part_Number XAL4020-122MEC; JLCPCB PN C19191653
Q301: BSS123; SOT-23; Manufacturer_Part_Number LBSS123LT1G; JLCPCB PN C8491
R301, R305: 10k; R_0805_2012Metric; JLCPCB PN C149881
R302: 51k; R_0805_2012Metric; JLCPCB PN C17737
R303: 1k; R_0603_1608Metric; JLCPCB PN C21190
R304: 10k; R_0603_1608Metric; JLCPCB PN C25804
R306: 4.7k; R_0603_1608Metric; JLCPCB PN C23162
R307, R314: 0R; R_0603_1608Metric; JLCPCB PN C15402; not fitted
R308, R309, R312: 5.1k; R_0603_1608Metric; JLCPCB PN C23186
R310, R311: 0R; R_0603_1608Metric; JLCPCB PN C15402
R313: 2.4k; R_0603_1608Metric; JLCPCB PN C22940
R315: 1k; R_0805_2012Metric; JLCPCB PN C17513
TP301: TestPoint_VBUS; TestPoint_Pad_D1.5mm
TP302: TestPoint_VBUS-SW; TestPoint_Pad_D1.5mm
U301: IRF9358TRPBF; SOIC127P600X175-8N; MPN IRF9358TRPBF; JLCPCB PN C537847
U302: TPD4EUSB30DQAR; USON-10_2.5x1.0mm_P0.5mm; Manufacturer_Part_Number TPD4EUSB30DQAR; JLCPCB PN C90627
U303: CYPD3177-24LQXQ; QFN-24-1EP_4x4mm_P0.5mm_EP2.75x2.75mm; Manufacturer_Part_Number CYPD3177-24LQXQ; JLCPCB PN C2959321

Connections:
3V3: C305.1, C306.1, C307.1, R305.1, R306.2, R307.1, R308.1, R309.2, R310.1, U303.23 (VDDD)
GND: C301.2, C302.2, C305.2, C306.2, C307.2, C308.2, D301.2 (A2), D304.1, J301.A1_B12 (GND), J301.B1_A12 (GND), J301.SH1 (SHIELD), J301.SH2 (SHIELD), J301.SH3 (SHIELD), J301.SH4 (SHIELD), Q301.2 (S), R304.1, R311.2, R312.2, R313.2, R314.2, U302.3 (GND), U302.8 (GND), U303.19 (GND), U303.22 (GND), U303.25 (GND)
unnamed: C301.1, L301.2, L302.1
unnamed: C302.1, L302.2, L303.1
unnamed: C303.1, L303.2, R301.1, U301.7, U301.8, U303.18 (VBUS_IN)
unnamed: C303.2, C304.2, D302.2 (A2), R301.2, R302.2, R303.1, U301.2, U301.4
unnamed: C308.1, U303.24 (VCCD)
unnamed: D302.1 (A1), R302.1, U301.1, U301.3
unnamed: D304.2, R315.2
unnamed: J301.A5 (CC1_A), U302.5 (D2-), U302.6 (NC), U303.15 (CC1)
unnamed: J301.B5 (CC1_B), U302.4 (D2+), U302.7 (NC), U303.14 (CC2)
unnamed: Q301.1 (G), R304.2, U303.9 (FAULT)
unnamed: R303.2, U303.3 (VBUS_FET_EN)
unnamed: R306.1, U303.10 (FLIP)
unnamed: R307.2, R311.1, U303.1 (VBUS_MIN)
unnamed: R308.2, R312.1, U303.2 (VBUS_MAX)
unnamed: R309.1, R313.1, U303.5 (ISNK_COARSE)
unnamed: R310.2, R314.1, U303.6 (ISNK_FINE)
PSU_GPIO1: Q301.3 (D), R305.2
VBUS: D301.1 (A1), J301.A4_B9 (VBUS), J301.B4_A9 (VBUS), L301.1, TP301.1
VBUS-SW: C304.1, R315.1, TP302.1, U301.5, U301.6, U303.11 (VDC_OUT)

Notes on the sheet:
https://www.mouser.de/datasheet/3/70/1/Infineon-EZ-PD_BCR_Datasheet_USB_Type-C_Port_Controller_for_Power_Sinks-DataSheet-v03_00-EN.pdf
