CodeByMika/technikerarbeit2026-hardwarepruefadapter/Hardware/hardware-pruefadapter/RS232.kicad_sch

## KiCad design Hardware/hardware-pruefadapter/RS232.kicad_sch (2026-06-18)

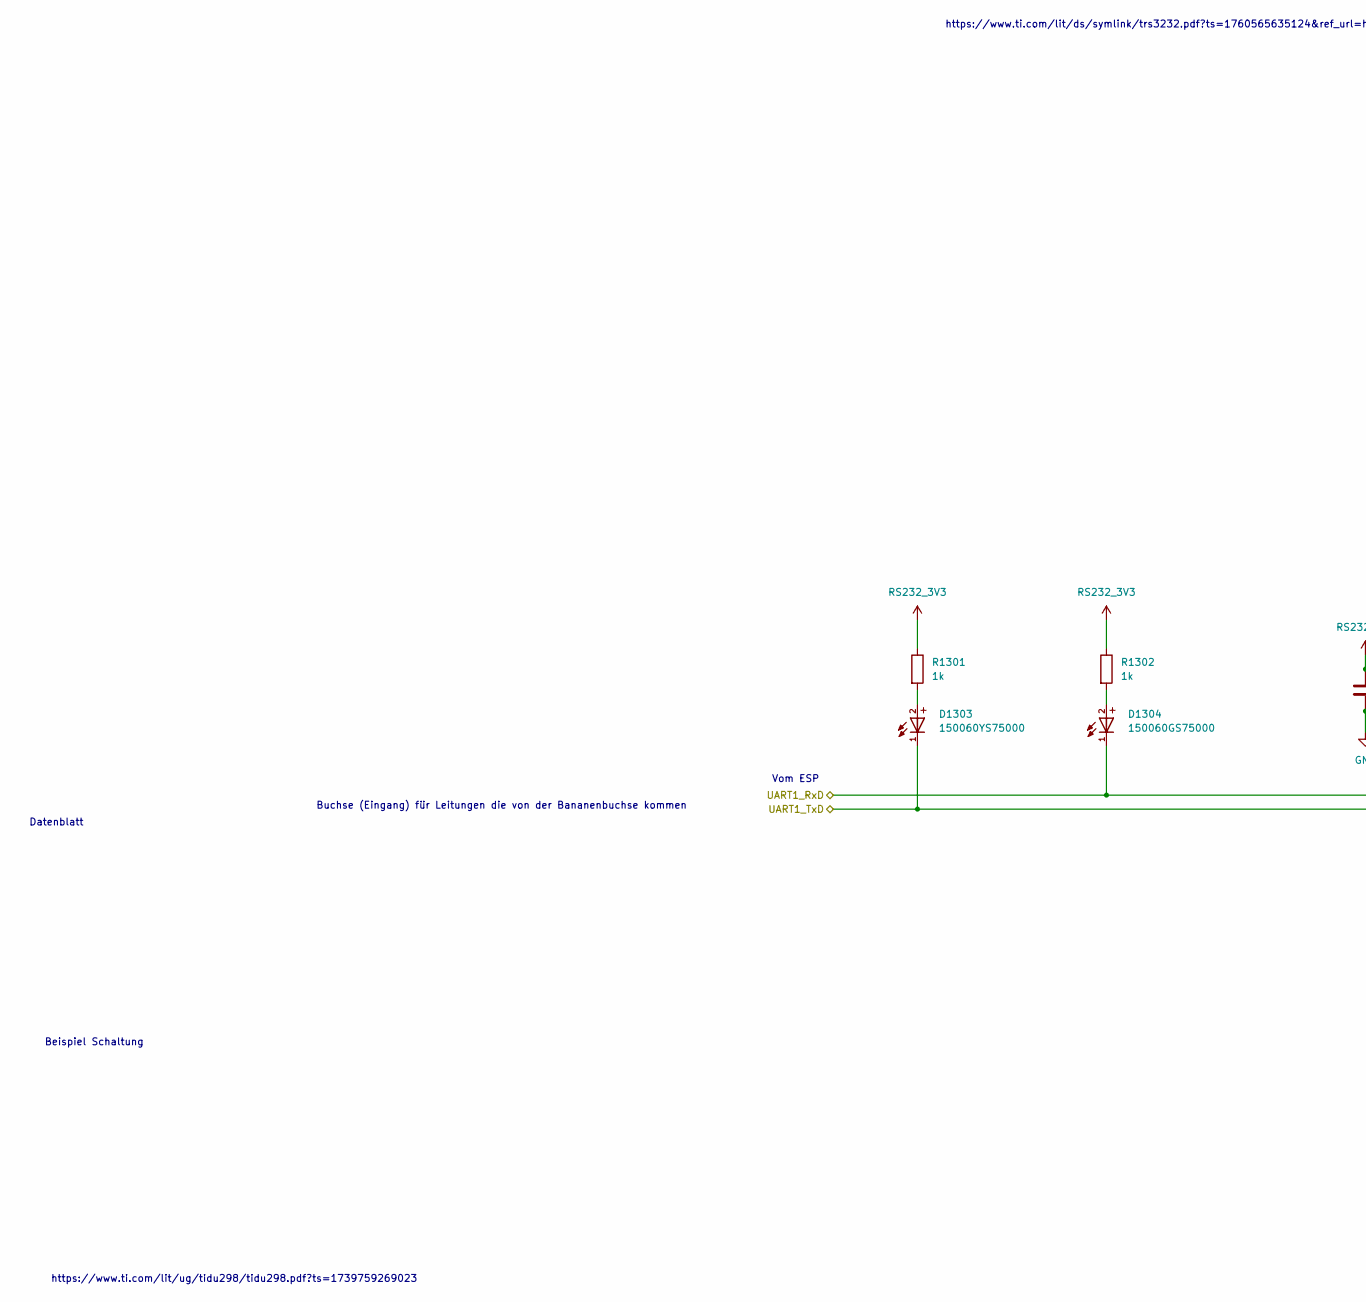
[picture p70: schematic RS232.kicad_sch, part in row 1, column 1]

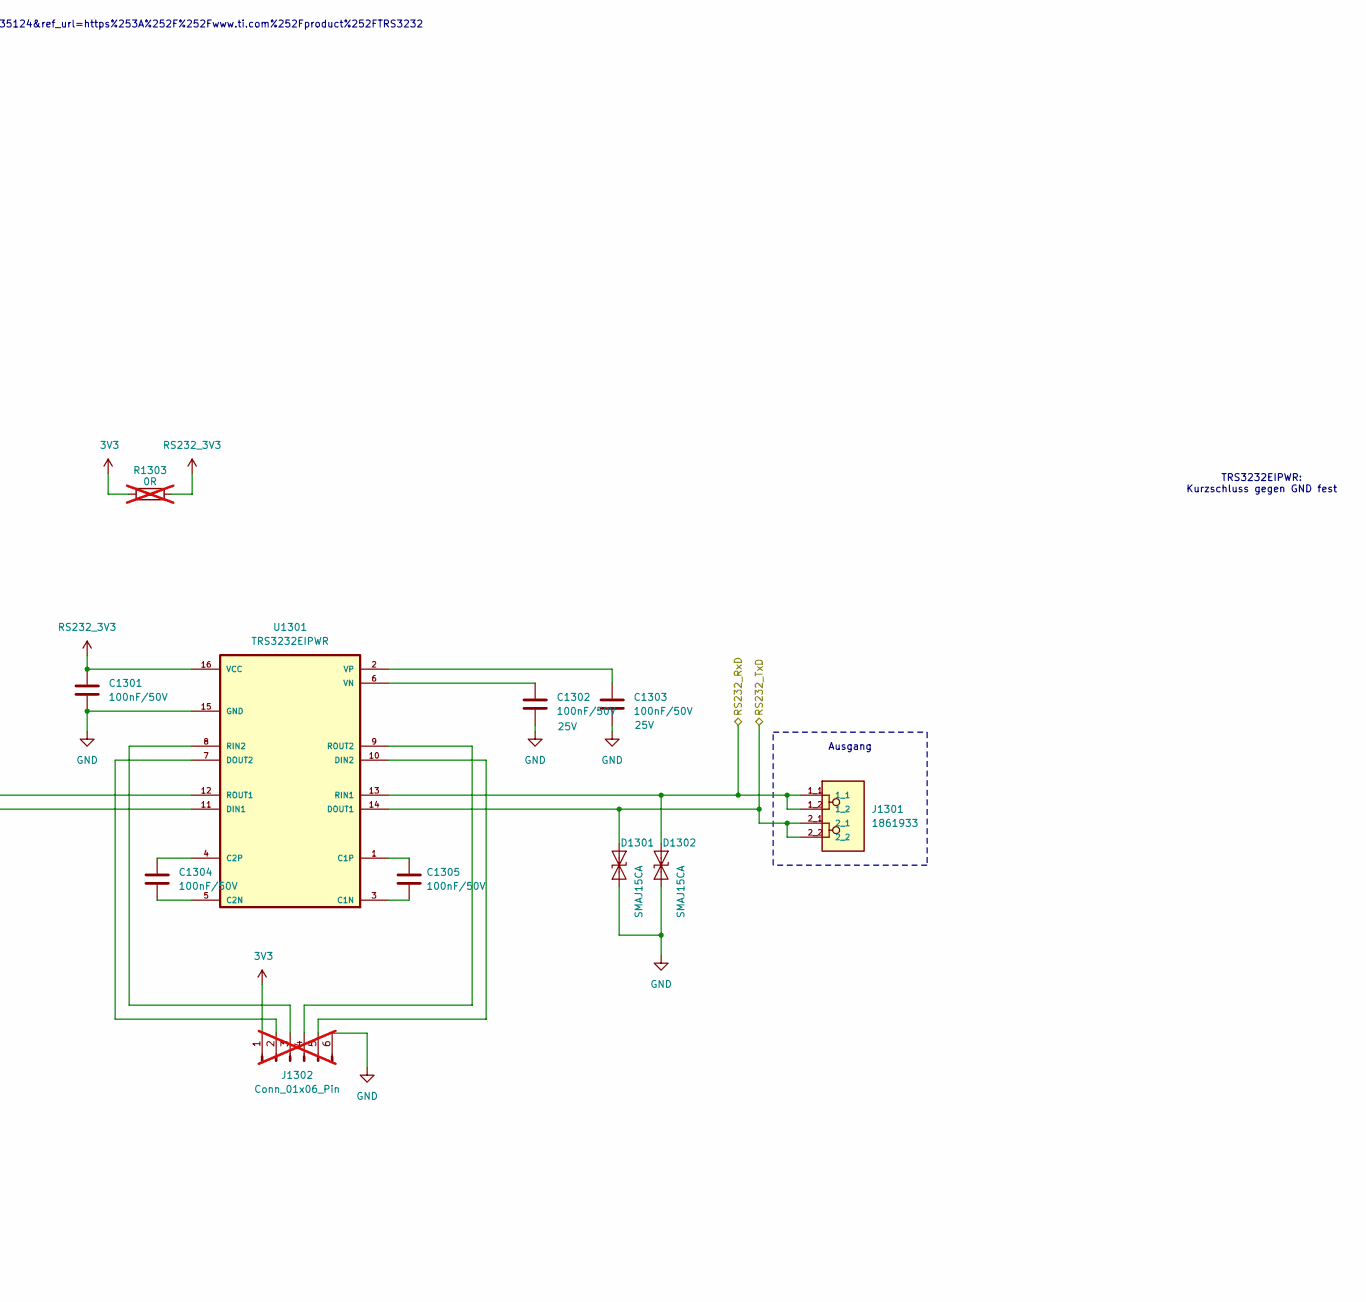
[picture p71: schematic RS232.kicad_sch, part in row 1, column 2]

Parts:
C1301, C1302, C1303, C1304, C1305: 100nF/50V; C_0805_2012Metric; JLCPCB PN C1711
D1301, D1302: SMAJ15CA; D_SMA; Manufacturer_Part_Number SMAJ15CA; JLCPCB PN C46985
D1303: 150060YS75000; WL-SMCW_0603_Yellow; Manufacturer_Part_Number 150060YS75000; JLCPCB PN C6784997
D1304: 150060GS75000; WL-SMCW_0603_Green; Manufacturer_Part_Number 150060GS75000; JLCPCB PN C5252984
J1301: 1861933; PHOENIX_1861933; PARTREV 28.08.2017; JLCPCB PN C5483323
J1302: Conn_01x06_Pin; PinHeader_1x06_P2.54mm_Vertical; not fitted
R1301, R1302: 1k; R_0805_2012Metric; JLCPCB PN C17513
R1303: 0R; R_1206_3216Metric; JLCPCB PN C17888; not fitted
U1301: TRS3232EIPWR; SOP65P640X120-16N; Manufacturer_Part_Number TRS3232EIPWR; DigiKey_Part_Number 296-22598-1-ND

Connections:
3V3: J1302.1, R1303.1
GND: C1301.2, C1302.2, C1303.2, D1301.2 (A2), D1302.2 (A2), J1302.6, U1301.15 (GND)
unnamed: C1302.1, U1301.6 (VN)
unnamed: C1303.1, U1301.2 (VP)
unnamed: C1304.1, U1301.4 (C2P)
unnamed: C1304.2, U1301.5 (C2N)
unnamed: C1305.1, U1301.1 (C1P)
unnamed: C1305.2, U1301.3 (C1N)
unnamed: D1303.2, R1301.2
unnamed: D1304.2, R1302.2
unnamed: J1302.2, U1301.7 (DOUT2)
unnamed: J1302.3, U1301.8 (RIN2)
unnamed: J1302.4, U1301.9 (ROUT2)
unnamed: J1302.5, U1301.10 (DIN2)
RS232_3V3: C1301.1, R1301.1, R1302.1, R1303.2, U1301.16 (VCC)
RS232_RxD: D1302.1 (A1), J1301.1_1, J1301.1_2, U1301.13 (RIN1)
RS232_TxD: D1301.1 (A1), J1301.2_1, J1301.2_2, U1301.14 (DOUT1)
UART1_RxD: D1304.1, U1301.12 (ROUT1)
UART1_TxD: D1303.1, U1301.11 (DIN1)

Notes on the sheet:
Vom ESP
Buchse (Eingang) für Leitungen die von der Bananenbuchse kommen
https://www.ti.com/lit/ds/symlink/trs3232.pdf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
Datenblatt
Beispiel Schaltung
TRS3232EIPWR: Kurzschluss gegen GND fest
https://www.ti.com/lit/ug/tidu298/tidu298.pdf?ts=1739759269023
Ausgang
