CodeByMika/technikerarbeit2026-hardwarepruefadapter/Hardware/hardware-pruefadapter/RS485.kicad_sch

## KiCad design Hardware/hardware-pruefadapter/RS485.kicad_sch (2026-06-18)

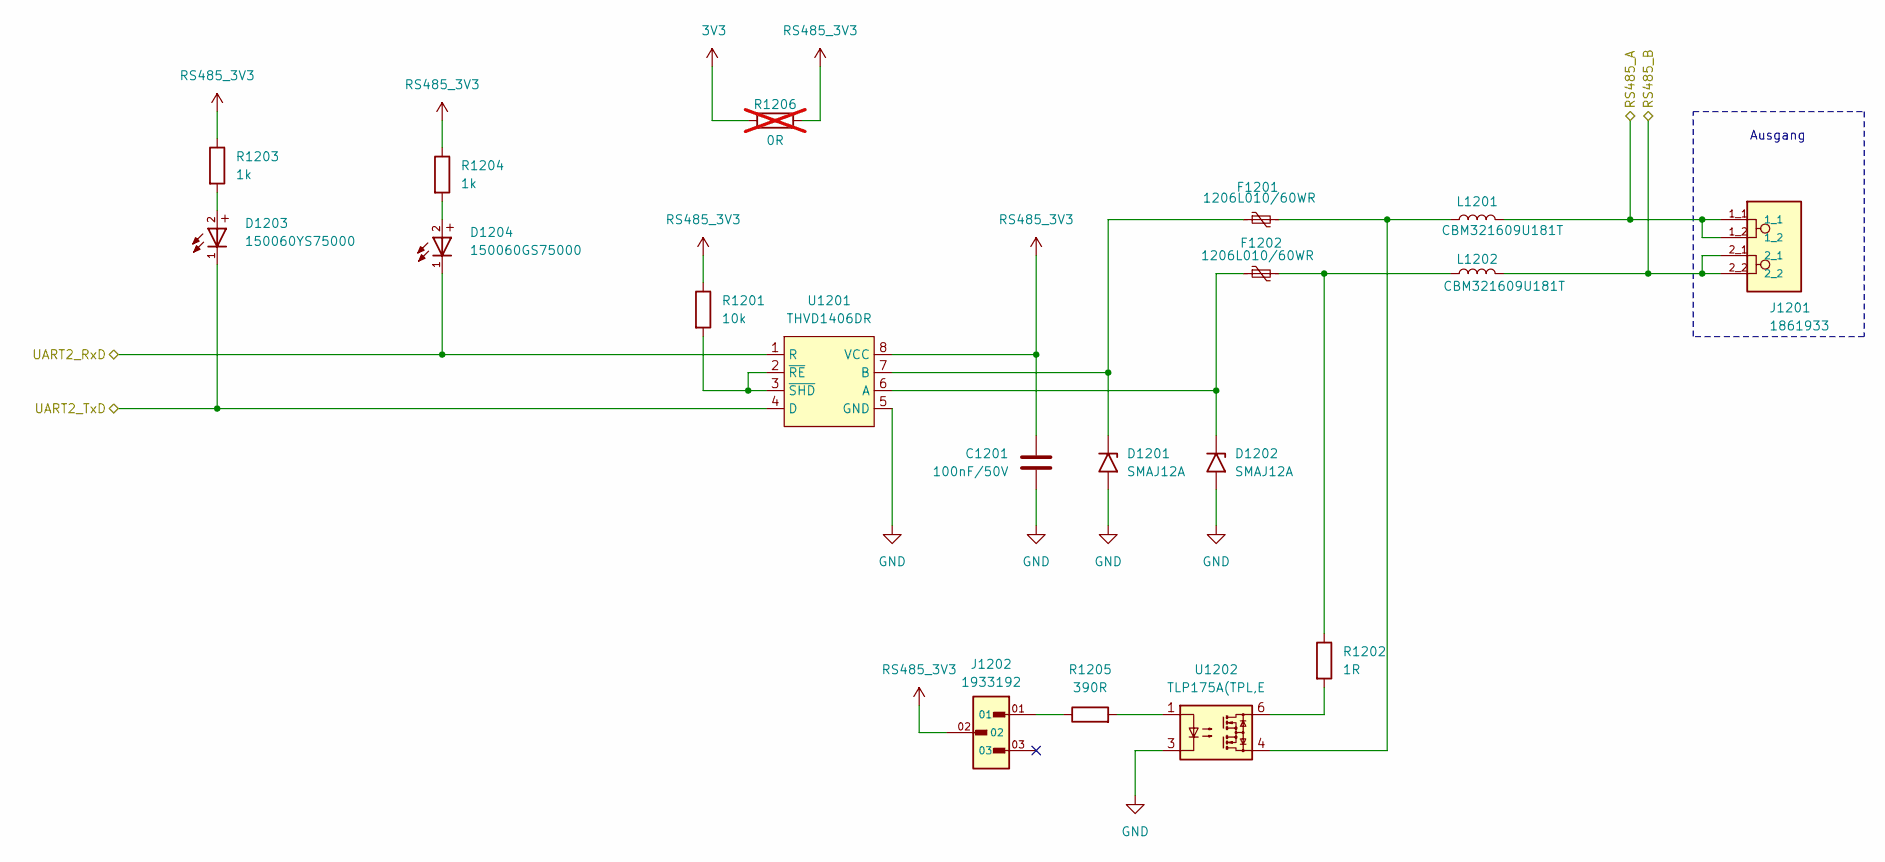
[picture p72: schematic RS485.kicad_sch]

Parts:
C1201: 100nF/50V; C_1206_3216Metric; JLCPCB PN C24497
D1201, D1202: SMAJ12A; D_SMA; Manufacturer_Part_Number SMAJ12A; JLCPCB PN C28613
D1203: 150060YS75000; WL-SMCW_0603_Yellow; Manufacturer_Part_Number 150060YS75000; JLCPCB PN C6784997
D1204: 150060GS75000; WL-SMCW_0603_Green; Manufacturer_Part_Number 150060GS75000; JLCPCB PN C5252984
F1201, F1202: 1206L010/60WR; Fuse_1206_3216Metric; Manufacturer_Part_Number Littelfuse; JLCPCB PN C2153714
J1201: 1861933; PHOENIX_1861933; PARTREV 28.08.2017; JLCPCB PN C5483323
J1202: 1933192; PHOENIX_1933192; PARTREV 29.05.2019; JLCPCB PN C5266027
L1201, L1202: CBM321609U181T; L_1206_3216Metric; Manufacturer_Part_Number CBM321609U181T; JLCPCB PN C391192
R1201: 10k; R_0805_2012Metric; JLCPCB PN C149881
R1202: 1R; R_1206_3216Metric; JLCPCB PN C17928
R1203, R1204: 1k; R_0805_2012Metric; JLCPCB PN C17513
R1205: 390R; R_0805_2012Metric; JLCPCB PN C17655
R1206: 0R; R_1206_3216Metric; JLCPCB PN C17888; not fitted
U1201: THVD1406DR; SOTFL50P160X60-8N; Manufacturer_Part_Number THVD1406DR; JLCPCB PN C5215918
U1202: TLP175A(TPL,E; MFSOP6-4_4.4x3.6mm_P1.27mm; Manufacturer_Part_Number TLP175A(TPL,E; JLCPCB PN C141522

Connections:
3V3: R1206.2
GND: C1201.2, D1201.2 (A2), D1202.2 (A2), U1201.5 (GND), U1202.3
unnamed: D1201.1 (A1), F1201.1, U1201.7 (B)
unnamed: D1202.1 (A1), F1202.1, U1201.6 (A)
unnamed: D1203.2, R1203.2
unnamed: D1204.2, R1204.2
unnamed: F1201.2, L1201.1, U1202.4
unnamed: F1202.2, L1202.1, R1202.1
unnamed: J1202.01, R1205.1
unnamed: R1201.2, U1201.2 (~RE), U1201.3 (~SHD)
unnamed: R1202.2, U1202.6
unnamed: R1205.2, U1202.1
RS485_3V3: C1201.1, J1202.02, R1201.1, R1203.1, R1204.1, R1206.1, U1201.8 (VCC)
RS485_A: J1201.1_1, J1201.1_2, L1201.2
RS485_B: J1201.2_1, J1201.2_2, L1202.2
UART2_RxD: D1204.1, U1201.1 (R)
UART2_TxD: D1203.1, U1201.4 (D)

Notes on the sheet:
Ausgang
