CodeByMika/technikerarbeit2026-hardwarepruefadapter/Hardware/hardware-pruefadapter/Spannungen.kicad_sch

## KiCad design Hardware/hardware-pruefadapter/Spannungen.kicad_sch (2026-06-18)

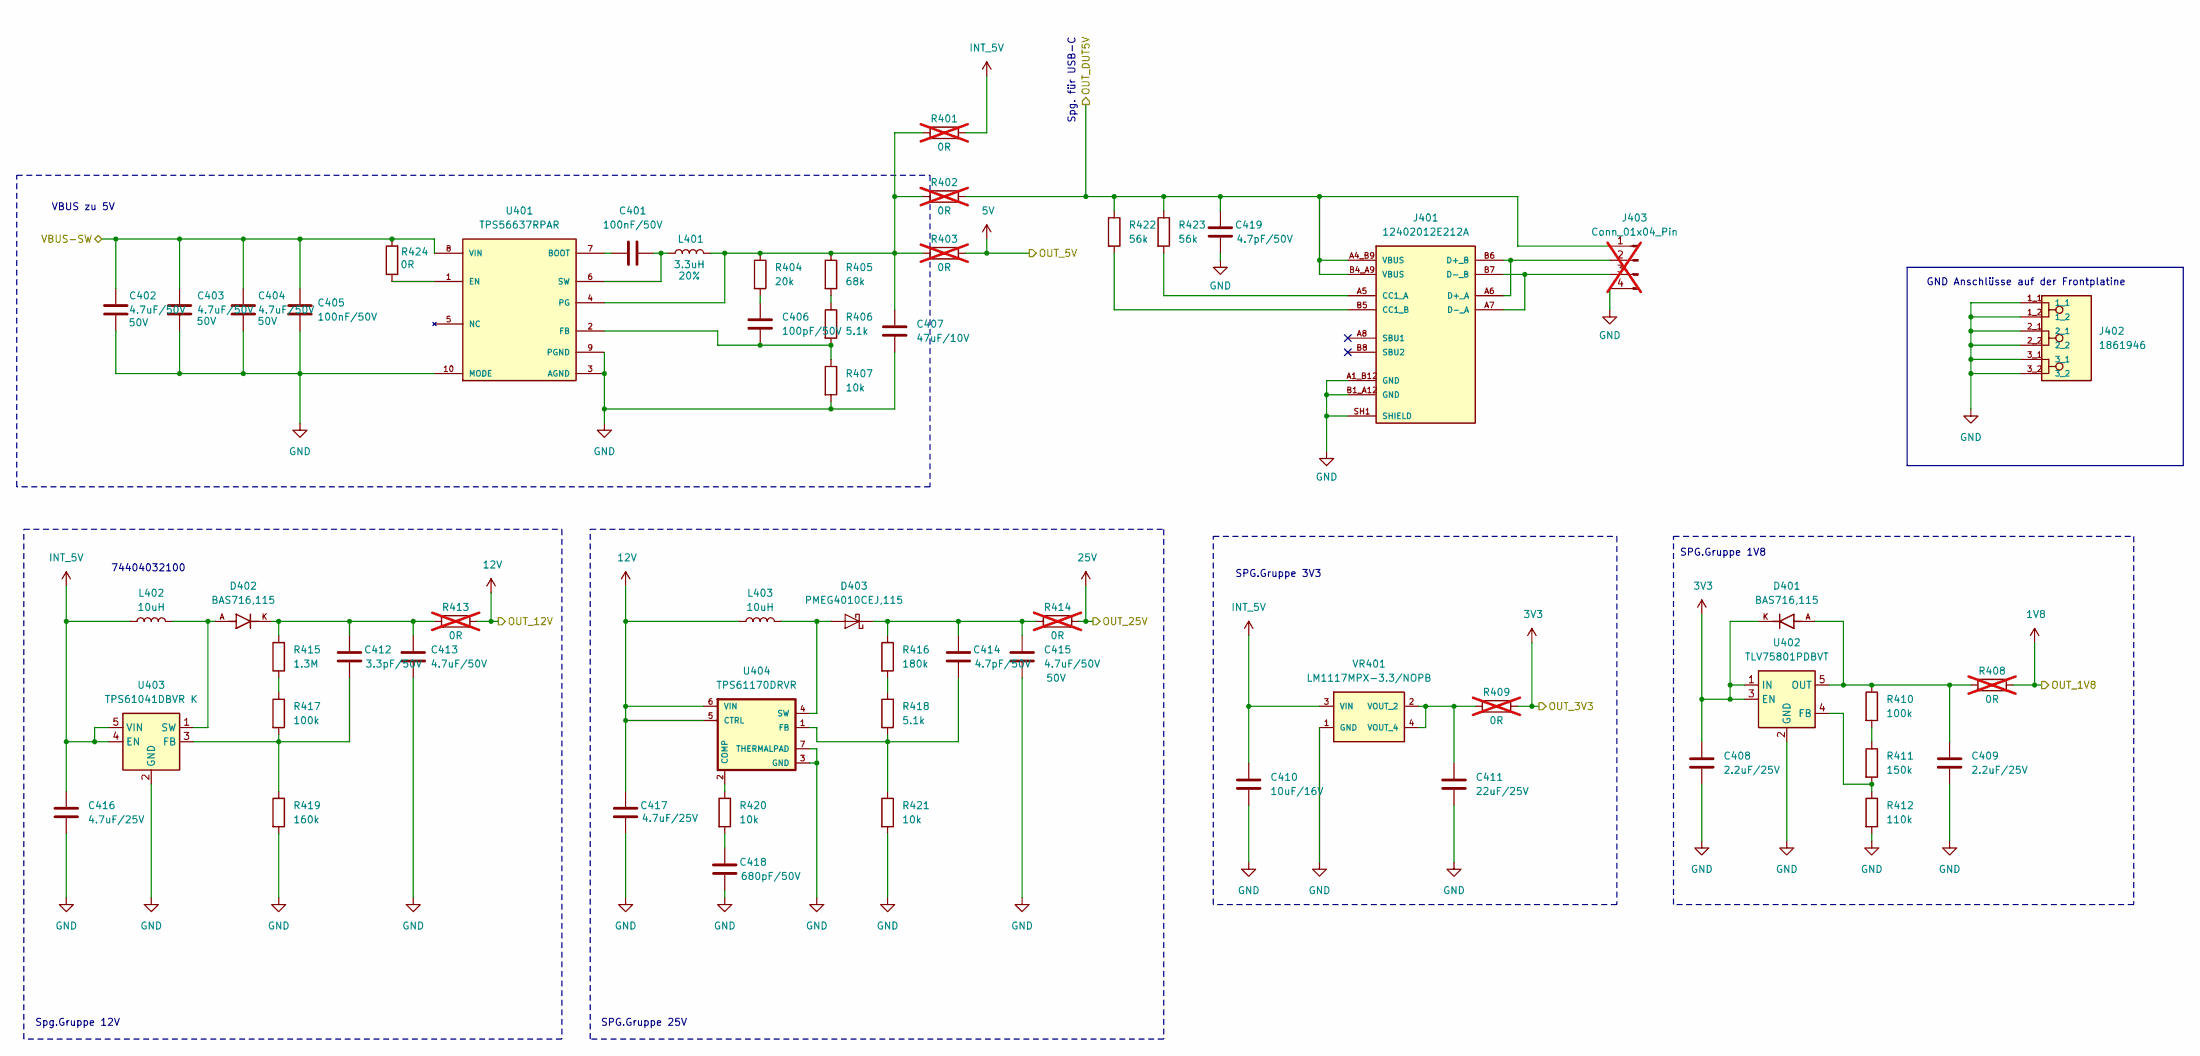
[picture p73: schematic Spannungen.kicad_sch]

Parts:
C401, C405: 100nF/50V; C_0805_2012Metric; JLCPCB PN C1711
C402, C403, C404, C413, C415: 4.7uF/50V; C_1206_3216Metric; JLCPCB PN C29823
C406: 100pF/50V; C_0805_2012Metric; JLCPCB PN C1790
C407: 47uF/10V; C_1206_3216Metric; JLCPCB PN C96123
C408, C409: 2.2uF/25V; C_0805_2012Metric; JLCPCB PN C19110
C410: 10uF/16V; C_1206_3216Metric; JLCPCB PN C1849
C411: 22uF/25V; C_1206_3216Metric; JLCPCB PN C12891
C412: 3.3pF/50V; C_0805_2012Metric; JLCPCB PN C170106
C414, C419: 4.7pF/50V; C_0805_2012Metric; JLCPCB PN C1820
C416, C417: 4.7uF/25V; C_0805_2012Metric; JLCPCB PN C1779
C418: 680pF/50V; C_0805_2012Metric; JLCPCB PN C1754
D401, D402: BAS716,115; DIO_BAS716_115; PARTREV 2; JLCPCB PN C282366
D403: PMEG4010CEJ,115; D_SOD-323F; Manufacturer_Part_Number PMEG4010CEJ,115; JLCPCB PN C50704
J401: 12402012E212A; AMPHENOL_12402012E212A; PARTREV 4; JLCPCB PN C5150972
J402: 1861946; PHOENIX_1861946; Manufacturer_Part_Number 1861946; JLCPCB PN C6368767
J403: Conn_01x04_Pin; PinHeader_1x04_P2.54mm_Vertical; not fitted
L401: 3.3uH; INDDFN750X750X310-2N; Manufacturer_Part_Number XAL7030-332MEC; JLCPCB PN C5448588
L402: 10uH; WE-LQS_3015; Manufacturer_Part_Number 74404032100; JLCPCB PN C1329386
L403: 10uH; WE-LQS_5020; Manufacturer_Part_Number 74404052100; JLCPCB PN C7193153
R401, R402, R403, R408, R409, R414: 0R; R_1206_3216Metric; JLCPCB PN C17888; not fitted
R404: 20k; R_0805_2012Metric; JLCPCB PN C4328
R405: 68k; R_0805_2012Metric; JLCPCB PN C17801
R406, R418: 5.1k; R_0805_2012Metric; JLCPCB PN C27834
R407, R420, R421: 10k; R_0805_2012Metric; JLCPCB PN C149881
R410, R417: 100k; R_0805_2012Metric; JLCPCB PN C149504
R411: 150k; R_0805_2012Metric; JLCPCB PN C17470
R412: 110k; R_0805_2012Metric; JLCPCB PN C17422
R413: 0R; R_0805_2012Metric; JLCPCB PN C17477; not fitted
R415: 1.3M; R_0805_2012Metric; JLCPCB PN C26109
R416: 180k; R_0805_2012Metric; JLCPCB PN C101955
R419: 160k; R_0805_2012Metric; JLCPCB PN C17485
R422, R423: 56k; R_0805_2012Metric; JLCPCB PN C17756
R424: 0R; R_1206_3216Metric; JLCPCB PN C17888
U401: TPS56637RPAR; CONV_TPS56637RPAR; PARTREV A; JLCPCB PN C841386
U402: TLV75801PDBVT; SOT-23-5; Manufacturer_Part_Number TLV75801PDBVT; JLCPCB PN C2868412
U403: TPS61041DBVR K; SOT-23-5; Manufacturer_Part_Number TPS61041DBVR K; JLCPCB PN C9846
U404: TPS61170DRVR; SON65P200X200X80-7N; Manufacturer_Part_Number TPS61170DRVR; JLCPCB PN C15163
VR401: LM1117MPX-3.3/NOPB; VREG_LM1117MPX-3.3_NOPB; PARTREV O; JLCPCB PN C9662

Connections:
1V8: R408.2
3V3: C408.1, D401.K, R409.2, U402.1 (IN), U402.3 (EN)
5V: R403.2
12V: C417.1, L403.1, R413.2, U404.5 (CTRL), U404.6 (VIN)
25V: R414.2
GND: C402.2, C403.2, C404.2, C405.2, C407.2, C408.2, C409.2, C410.2, C411.2, C413.2, C415.2, C416.2, C417.2, C418.2, C419.2, J401.A1_B12 (GND), J401.B1_A12 (GND), J401.SH1 (SHIELD), J401.SH2 (SHIELD), J401.SH3 (SHIELD), J401.SH4 (SHIELD), J402.1_1, J402.1_2, J402.2_1, J402.2_2, J402.3_1, J402.3_2, J403.4, R407.2, R412.2, R419.2, R421.2, U401.3 (AGND), U401.9 (PGND), U401.10 (MODE), U402.2 (GND), U403.2 (GND), U404.3 (GND), U404.7 (THERMALPAD), VR401.1 (GND)
INT_5V: C410.1, C416.1, L402.1, R401.2, U403.4 (EN), U403.5 (VIN), VR401.3 (VIN)
unnamed: C401.1, U401.7 (BOOT)
unnamed: C401.2, L401.1, U401.6 (SW)
unnamed: C406.1, R404.2
unnamed: C406.2, R406.2, R407.1, U401.2 (FB)
unnamed: C407.1, L401.2, R401.1, R402.1, R403.1, R404.1, R405.1, U401.4 (PG)
unnamed: C409.1, D401.A, R408.1, R410.1, U402.5 (OUT)
unnamed: C411.1, R409.1, VR401.2 (VOUT_2), VR401.4 (VOUT_4)
unnamed: C412.1, C413.1, D402.K, R413.1, R415.2
unnamed: C412.2, R417.2, R419.1, U403.3 (FB)
unnamed: C414.1, C415.1, D403.1 (K), R414.1, R416.1
unnamed: C414.2, R418.2, R421.1, U404.1 (FB)
unnamed: C418.1, R420.2
unnamed: D402.A, L402.2, U403.1 (SW)
unnamed: D403.2 (A), L403.2, U404.4 (SW)
unnamed: J401.A5 (CC1_A), R423.2
unnamed: J401.A6 (D+_A), J401.B6 (D+_B), J403.2
unnamed: J401.A7 (D-_A), J401.B7 (D-_B), J403.3
unnamed: J401.B5 (CC1_B), R422.2
unnamed: R405.2, R406.1
unnamed: R410.2, R411.1
unnamed: R411.2, R412.1, U402.4 (FB)
unnamed: R415.1, R417.1
unnamed: R416.2, R418.1
unnamed: R420.1, U404.2 (COMP)
unnamed: R424.1, U401.1 (EN)
OUT_DUT5V: C419.1, J401.A4_B9 (VBUS), J401.B4_A9 (VBUS), J403.1, R402.2, R422.1, R423.1
VBUS-SW: C402.1, C403.1, C404.1, C405.1, R424.2, U401.8 (VIN)

Notes on the sheet:
SPG.Gruppe 1V8
SPG.Gruppe 3V3
Spg.Gruppe 12V
GND Anschlüsse auf der Frontplatine
74404032100
VBUS zu 5V
SPG.Gruppe 25V
Spg. für USB-C
